Abse2001/g350-linux-handheld/docs/AM3352_DDR38_CHECKPOINT.md

# DDR38 routing checkpoint — 2026-10-04

Installed versions: tscircuit **0.0.2744**, core **0.0.2080**, capacity-autorouter **0.0.958**, CLI **0.1.2237**. The earlier immutable upgrade binder still verifies these packages and the unchanged default DDR30 copper.

The editable [DDR38 candidate](../experiments/am3352-command-clock-seeded-775-replay.circuit.tsx) preserves all 23 checked data/reset guides, the previously checked clock pair and all fixed host copper. Trials 766–776 replan uncommitted fanout reservations and negotiate manual command carriers on Top/Bottom. The complete replay restores every differential-pair declaration. Independent KiCad numeric-pad connectivity confirms **38 of 49 DDR signals connected** in one coherent placement, with 140 trace pieces, 175 full-depth through-vias, 212 logical components and 912 physical pads on four copper layers. All 125 original trace pieces and 141 original vias are retained. Both bytes and all three pairs pass planar relative skew.

The actual local tsci phase **DDR_COMMAND_CLOCK_BUS_LANES**, using **bus_lanes**, ran on the remaining 11 commands with all 140 fixed traces and 912 pads. Its input is independently verified against the complete replay. Only already guided pair declarations are omitted in the diagnostic continuation; the complete source retains them. [Trial 776](../dist/am3352-command-clock-seeded-775-native-phase-attempt-776/result.json) timed out at its configured 60-second routing limit (77.624 seconds total build wall time), producing no complete new output. Partial solver paths are not counted as successful routing.

All-layer Gerber shorts: **zero**. Independent physical clearance/drill violations: **zero**. KiCad still reports 418 presentation warnings, 499 reported/capped host opens and the same five explicitly ignored checks. Exact local library generation preserves all 15,379 physical records. RAM supply/ground/bypass plane connectivity remains 18/21/28; USB retains 38 numeric-pad assignments and 40 copper continuity checks. Top and Bottom snapshots were inspected. TypeScript and helper syntax checks pass.

DDR is unqualified: 11 command/control signals are missing; 14 routed command/clock signals fail the **41.75–44.29 mm** nominal range; **A2/A9/A13/A14/A8** exceed TI's **31.75 mm** reduced-class-spacing allowance. Complete command-group matching, coupling, impedance, return transitions, package/via delays and termination/ODT remain open. The separate DDR34 branch passes physical/connectivity checks but its A9 has a same-net length ambiguity: route sum 41.775130 mm versus graph path 40.536307 mm. That electrical branch is not promoted.

The fixture remains **100 × 124 × 1.6 mm** and does **not** have verified original G350 shell fit. Host power/storage/display/controls/audio/Linux work remains incomplete. Fabrication remains blocked before modification of any of the 205 historical fabrication files. No commit, GitHub push or tscircuit publication was made. The default stays DDR30; the older DDR33 spacing-repaired checkpoint remains immutable.

Evidence: [checked summary](../checks/integrated/am3352-command-clock-seeded-775-replay-check-summary.json), [nominal and spacing review](../checks/integrated/am3352-command-clock-seeded-775-replay-spacing-and-nominal-review.json), [native input preservation](../checks/integrated/am3352-command-clock-seeded-775-replay-native-phase-input-validation.json). Guidance: [tscircuit DDR routing](https://docs.tscircuit.com/guides/routing-ddr) and [TI AM335x datasheet SPRS717L, Tables 7-61/62/68/69](https://www.ti.com/lit/ds/sprs717l/sprs717l.pdf).

Next work: coordinate the remaining 11 command escapes and native phases, repair nominal lengths and spacing, then run fresh complete-interface checks. Measured original-shell geometry and the powered handheld/Linux implementation remain required before release.
