Abse2001/g350-linux-handheld/docs/AM3352_DDR_ROUTING.md

# AM3352 DDR routing record — 2026-10-04

## Compatible command package exits — trials 794–808

The first five-path opening leaves BA0/A3 competing for one RAM exit. Exact owner diagnostics identify additional reservations, and opening nine unqualified command routes provides individually legal candidates for all 32 remaining endpoints. The initial joint search reaches 400,000 choices. Factoring independent candidate regions and propagating pairwise support identifies an incompatible CPU candidate set in 0.829 seconds; this is a result for the generated candidate domains, not a proof that the PCB cannot be routed.

The next source opens all 17 staged command/control routes for a complete 24-signal replan, preserving both checked data bytes, reset, the clock pair and all reference/USB copper. It retains 25 complete DDR channels, 127 trace pieces, 145 vias, 212 logical components and 912 SMT pads. Actual local tsci `DDR_COMMAND_CLOCK_BUS_LANES` trials 796/801 use core 0.0.2080 on 16/24 open commands; both time out with no complete output. Source/input audits verify the actual numeric pad endpoints, all fixed copper and the four-layer Top/Bottom signal restriction. All three pair declarations remain present in the complete editable sources.

The factored manual search assigns **all 48 package exits in 48 choices**, including exact mutual foreign-land and drill separation. It adds 48 through-vias and 48 Top prefix pieces. The source refills its original continuous GND/DDR1V5 boundaries around those signal holes with the existing 0.12 mm pour margin. Independent KiCad verifies all **24 CPU and 24 RAM numeric pads to their intended full-depth vias**, all 25 retained complete CPU/RAM DDR channels, RAM supply/ground/bypass connectivity at **18/21/28**, and USB numeric assignments/continuity at **38/40**. Both byte groups and all three pairs retain relative planar skew. All-layer shorts and physical clearance/drill violations are zero. The partial board explicitly retains **48 dangling-via warnings**, **418 presentation warnings**, **499 reported/capped host opens** and the same five ignored checks. Exact local library generation preserves 13,725 physical records; both surface snapshots were inspected. [Independent checked package-exit summary](../checks/integrated/am3352-command-compatible-fanouts-802-check-summary.json).

Direct combined native trial 803 fails negotiated lane search. Phased native trial 804 obtains six via-free carriers: A11, RASn, A2, A7, A14 and A6. A guarded manual repair pass retains those exact six and plans five additional carriers, leaving 13 commands unresolved. These interconnect plans remain nonexportable until combined with their local prefixes in an editable source and independently checked. The true through-via terminal permits either outer face; the wrapper records the face actually chosen by the unchanged guarded bridge. Earlier off-grid and wrapper-assertion retries are retained as rejected logs; one retry loaded its old assertion before the edit finished and its runtime helper snapshot is explicitly marked unreproducible. No PCB copper from those retries was accepted.

The package pad and via shape audit confirms circular geometry is already represented correctly. Next work should coordinate the unresolved carriers with exit choices and examine whether the conservative raster guard excludes physically legal thin corridors. Every accepted repair must preserve the actual 0.1016 mm copper clearance, 0.20 mm drill-to-pad clearance and 0.254 mm drill-edge spacing, then pass independent combined checks. The full target remains all 49 DDR signals, complete timing/spacing/impedance/returns/termination, the powered handheld and Linux, and measured original G350 shell integration. The checked fallback remains DDR42; the default remains DDR30. Registry rechecks still match tscircuit 0.0.2744, core 0.0.2080, capacity-autorouter 0.0.958 and CLI 0.1.2237. Typechecking passes. Fabrication stays blocked and all 205 historical fabrication files are unchanged. No GitHub or tscircuit push was made.

## Latest checked partial routing: DDR42

The editable [DDR42 replay](../experiments/am3352-command-fine-782-replay.circuit.tsx) connects **42 of 49 actual CPU/RAM pad pairs** on four layers. It preserves the original 23 data/reset guides, the previously checked clock pair, all 125 original trace pieces, all 141 original vias, and every component, physical pad and fixed reference/USB piece. The new replay contains **144 trace pieces and 187 full-depth through-vias**. Independent KiCad connectivity, all-layer shorts, physical clearance/drill checks and filled RAM reference-plane connectivity pass. Both bytes and all three pairs pass relative planar skew. [Bound checks](../checks/integrated/am3352-command-fine-782-replay-check-summary.json).

Installed and registry-verified versions remain **tscircuit 0.0.2744, core 0.0.2080, capacity-autorouter 0.0.958 and CLI 0.1.2237**. The [native continuation](../experiments/am3352-command-fine-782-replay-native-phase.circuit.tsx) runs the Host's `DDR_COMMAND_CLOCK_BUS_LANES` phase through local tsci with `autorouter="bus_lanes"`. Trial 783 preserves all 144 fixed pieces and 912 SMT pads, then fails with **No collision-free local dogbone assignment**. Only already guided pair declarations are omitted in this diagnostic; the complete editable replay retains all three declarations.

Seven signals are missing: **A3, RASn, WEn, A2, A12, A11 and CKE**. Seventeen routed command/clock signals fail the placement-derived **41.75–44.29 mm** nominal range. **A9, A13, D12, A10, A14, A4 and A8** exceed the **31.75 mm** reduced-class-spacing allowance. Preserving D12 geometry does not preserve its spacing exposure when new neighboring command routes are added. The full command group, coupling, impedance, return transitions, package/via delays and termination/ODT remain unqualified. There are still 418 presentation warnings, 499 reported/capped host opens and five explicitly recorded ignored checks.

Exact local diagnostics identify five unqualified command carriers blocking the remaining package exits: **A7, BA0, CASn, A4 and ODT**. Opening these produces a temporary 37-signal planning stage while preserving data/reset/clock/reference/USB copper. Actual native trial 791 runs on its 12 open commands, 139 fixed traces and 912 pads, then times out without complete output. Simultaneous manual-fanout trials 792 and 793 find individually legal candidates for all 24 endpoints but fail the joint assignment: BA0's remaining RAM exit conflicts with every A3 RAM candidate. Expanded guarded surface searches do not resolve that conflict. These stages add no checked complete signals and do not replace DDR42. Trial 790's partial carrier plan also does not exceed the checked DDR42 result.

The default remains DDR30. Fabrication is blocked: complete DDR timing/spacing and host routing, the powered peripherals and Linux, and measured original G350 shell geometry remain required. The 100 × 124 mm routing fixture does not fit the original shell. No GitHub or tscircuit publication was made for this partial checkpoint.

The requested bootstrap uses tscircuit's **native `bus_lanes` preset**, implemented by `BusLanesPipelineSolver`. The installed core is now 0.0.2080 and capacity-autorouter is 0.0.958; historical trials retain their original version records; attempts 1–16 below used 0.0.2048, and attempts 17–207 used 0.0.2050. The current [DDR guide](https://docs.tscircuit.com/guides/routing-ddr), [autorouting phase API](https://docs.tscircuit.com/elements/autoroutingphase) and [breakout API](https://docs.tscircuit.com/elements/breakout) were read and applied. The user's `lane_bus` refers to the documented `bus_lanes` name.

## Implementation

The two packages are individual JLCPCB imports, corrected against primary ball maps. Every one of the420 physical balls remains present. There are49 numeric-pin trace connections:22 byte signals,26 synchronous address/command/clock signals and asynchronous reset. DQS0, DQS1 and CK have explicit differential-pair constraints. The old8-layer trials used independent L3/L7/L5 buses. The current4-layer candidate permits DDR wires only on top/bottom, reserving both inner reference layers.

The active `am3352-powered-host.circuit.tsx` uses four native DDR routing phases followed by a power/control phase. The isolated `am3352-ddr-clearance-bootstrap.circuit.tsx` retains the same DDR routing approach. Local pad-to-layer dogbones are generated by the DDR preset; the interconnect then stays on its assigned signal layer. Separate manual-fanout experiments preserve the autorouter for the channel. An opposing-boundary experiment reserves distinct bottom/top exit regions for the two bytes and command bus, with larger fanout areas.

The documented phase configuration is `autorouter="bus_lanes"`; `routingPhaseIndex` on each named electrical trace assigns it to that pass. Buses group those traces but do not create their electrical connections. The preset preserves prior fanout copper, includes its planar lengths in matching, and adds no intermediate channel vias. `pcbAllowedLayers` and `preferredLayers` restrict allowed layers. Supplied fanouts therefore need compatible layer exits and a winding order that permits a planar connection.

For manual local changes, the supported interface is `<breakout pcbTracePaths={paths}>` (also available on its `<fanout>` alias). Saved paths are keyed by port selector and must cover every routing connection owned by that breakout. The global channel still runs `bus_lanes`. A later `reroute` phase can target earlier routed connections or a rectangular region; this does not waive connectivity, clearance, or timing checks. Supply escapes need explicit connections and plane mapping through `fanoutPourNetMap`, rather than overlaying the guide's separate power-dogbone example.

The guide's Winbond example has 47 signals. Our selected Micron 4 Gb x16 part has 49, including A13 and A14; its map must not be replaced by the example's map. Its M7 is NC. All CPU/RAM terminals are independently checked against the selected primary ball maps.

## Checked partial result

Attempt 10 routed byte0 in 7.5 seconds, then byte1 timed out at 90 seconds. The aborted render discarded all copper. `export-am3352-diagnostic.mjs` recovers the **unchanged** completed first-phase traces from the exact second-phase input, verifies the original two pad endpoints and physical via dimensions, and retains the native timeout record. It makes a partial diagnostic with source/checkpoint/result hashes, never a release bundle.

| Check on this diagnostic | Result |
|---|---|
| Continuous processor-to-RAM signals | 11/49; 38 open |
| Full-depth through-vias | 22, 0.35 mm lands / 0.15 mm drills |
| Byte0 end-to-end planar skew | 0.635 mm, passes 0.635 mm limit |
| DQS0 end-to-end planar skew | 0.127 mm, passes 0.127 mm limit |
| Gerber shorts, all eight layers | 0 |
| KiCad copper/drill violations | 0 |
| Complete DDR continuity/timing | Fails: remaining buses incomplete |
| Powered host / fabrication readiness | False |

Evidence is in `checks/integrated/am3352-clearance-11-*`, with the actual checked circuit retained in `routing/am3352-byte0-native-diagnostic.circuit.json`. The inspected snapshot is `images/am3352-memory-clearance-11.png`. The original 0.30 mm lands had 31 copper-to-drill violations under the same 0.20 mm hole-clearance rule. Larger lands reserve the missing clearance without reducing that rule. KiCad exports are verified against the actual Circuit JSON before logical via-layer pairs are normalized to physical F.Cu–B.Cu spans; exact duplicates are removed and geometry is preserved during library preparation.

Timeout reports omit only `lastProgress.debugGraphics`, a large presentation overlay; the full original failure-file hash and all timeout metadata remain. A before/after hash comparison confirms that compacting the error message changed no physical or source records. The default continuity check still rejects the retained native error and all 38 open signals.

## Attempts and current failure

| Attempt | Geometry/strategy | Outcome |
|---|---|---|
| 1–2 | 0.4572/0.254 mm vias; numeric-terminal correction | Local dogbones, then negotiated search failed |
| 3 | Separate bus phases, larger vias | Byte0 timeout |
| 4 | Direct native dogbones, 0.30/0.15 mm | Byte0 routed; byte1 timeout; 31 drill-clearance errors |
| 5 | RAM shifted to (+3, −23) mm | Byte0 timeout |
| 6 | Manual opposing dogbone quadrants | Byte0 routed; byte1 timeout; incomplete export |
| 7 | Manual fanouts, 0.127 mm clearance | Byte0 timeout |
| 8 | Whole-byte swap, manual fanouts | Byte0 timeout |
| 9 | Within-byte DQ permutation | No shared DQS0 tuning corridor |
| 10 | Direct native dogbones, 0.35/0.15 mm | Byte0 routed and physical checks passed; byte1 timeout |
| 11 | All 49 dogbones coordinated in one phase, separate buses | Negotiated lane search exhausted |
| 12 | Byte1-first phase order | Byte1 timeout at 90.1 s |
| 13 | Larger, opposing ordered fanouts | First fanout stopped responding; externally terminated after exceeding 3 min |
| 14 | Permute byte1 DQ only; byte1 first | Native byte1 routed in 8.6 s; subsequent byte0 had no collision-free dogbone assignment |
| 15 | Both byte lanes together, separate timing buses | Negotiated search timed out at 90.0 s |
| 16 | Prepare all 98 native dogbones together; replay through `pcbTracePaths` | Both package escapes accepted; byte0 channel timed out at 90.2 s |
| 17 | Full 142-component power/DDR draft; latest core 0.0.2050 | Byte0 failed during local dogbone assignment after 30.7 s; no channel copper retained |
| 18 | Move bypass parts out of signal escape corridors, preserving TI limits | Local escape preparation advanced; native solver rejected the rounded board outline after 21.9 s |
| 19 | Same 142-component placement, rectangular outline | Byte0 routed in 51.4 s; byte1 dogbone assignment failed in 0.8 s |

Changing phase order tests whether prior through-vias consume later escapes. Coordinated dogbones test simultaneous site assignment. Ordered fanouts address winding and local congestion directly. Failed phases are not counted as completed connections. An empty-copper render is rejected by the independent connectivity check before the default shorts command.

TI allows [within-byte DQ swapping and complete byte-lane swapping](https://e2e.ti.com/support/processors-group/processors/f/processors-forum/1205797/am4376-about-ddr3-data-line-swapping), including the matching DQS and DM signals when swapping whole bytes. These trial maps have independent bijection/function/group checks. Address and command maps remain fixed. They are experiments, not a claim of successful routing.

The byte1-only map has a separately recovered, unchanged native 11-signal diagnostic. Its end-to-end byte skew is 0.635 mm, DQS1 skew is 0.011685 mm, and it has zero all-layer Gerber shorts and zero KiCad physical violations. The other 38 signals remain open. Its native failure and downstream missing-copper records are retained. Evidence: `checks/integrated/am3352-byte1-11-*`. The two independently checked byte diagnostics cannot be combined into a 22-signal result: their escape sites have not been routed and checked together.

The guide's saved-fanout interface was applied in attempt 16. `bootstrap-am3352-native-dogbones.mjs` verifies the actual source terminals, prepares the 98 escapes using the installed native DDR solver, and records hashes before translating only local coordinates into component-relative `pcbTracePaths`. The four global phases still run `bus_lanes`. Preparation is an escape result, not channel connectivity or DRC approval.

The default entry now advances the actual host source, including PMIC and decoupling. The two-package routing fixtures remain isolated experiments; their physical checks do not cover that larger board.

The power draft keeps three of its twenty CPU DDR high-speed capacitors beneath the CPU. The other CPU parts and all twelve RAM parts move beside the packages to leave signal-via corridors open. The generated-layout audit retains TI's maximum nearest power/ground distance of 10.16 mm for CPU capacitors and 3.81 mm for RAM capacitors, with zero native placement errors. These nominal placement checks do not establish the eventual capacitor-via topology or effective capacitance. Attempt 18 also exposed an additional native solver restriction: its lane stage rejects custom board outlines. The active routing draft therefore uses a rectangular 100 by 124 mm outline.

Attempt 19 supplies a new checked result on that actual larger placement: eleven continuous byte0 signals, twenty-two physical through-vias, 0.635 mm byte skew, 0.127 mm DQS0 skew, zero all-layer Gerber shorts and zero independent copper/drill errors. KiCad retains **402 silkscreen warnings and 499 unconnected host items**. The native byte1 failure and downstream missing-copper records remain intact. This is incomplete host copper, not an overall DRC pass. Evidence: `checks/integrated/am3352-host-byte0-19-*`; exact circuit: `routing/am3352-host-byte0-native-diagnostic.circuit.json`.

## Remaining qualification

The active board now uses **four layers maximum**. The preceding eight-layer attempts remain historical. Attempt 21 uses the actual 185-component clock/boot/power placement and completes byte0: 11/49 signals, 22 through-vias spanning exactly four layers, zero Gerber shorts, zero KiCad copper/drill errors, passing byte0/DQS0 planar skew, 416 silkscreen warnings and 499 unconnected host items. Attempt 22 reserves all 98 DDR escapes against all 821 actual SMT-pad obstacles but fails its complete planar channel search after 7.81 seconds. Attempt 23 rotates RAM by 180 degrees and times out in byte0. Attempt 24 explicitly guides native fanout exits into facing corridors and times out during CPU fanout. A general-router repair trial retains the native byte0 bootstrap; any resulting channels still require full continuity, end-to-end skew, shorts and independent physical checks. None of these trials qualifies the stackup or reference planes.

The standalone fixtures have no power nets, planes or decoupling. Through attempt25, the host source had logical power nets/decoupling but no completed power copper or planes. Repair attempt25 preserves native byte0 and times out after90 seconds. The0.635/0.127mm checks measure planar copper only; they exclude package delays and via depth. Pair spacing and impedance need the fabricator stackup. TI's reference via guidelines differ from the fine-drill trial. Complete all49 signals and the powered board, then rerun continuity, skew, shorts, physical DRC and stackup-aware review before producing fabrication files.

## Current four-layer candidate with reference regions

TI SPRS717L Tables7-61/62 require two signal layers, a full ground reference and a full DDR power reference. The current source therefore reserves **inner1 GND / inner2 DDR_1V5**, with signals on **top/bottom** and18mil lands/10mil drills. Attempt21's inner1 signal route is historical and cannot qualify this allocation. The independent routing check now rejects inner signal copper, undersized trial vias, missing reference regions and DDR wires outside the reserved region.

At attempt 27, the 204-component source integrated the DM3D-SF microSD holder, its separate regulator and reset supervisor. Both inner reference regions rendered, with one CPU DDR bypass loop: two bottom traces and two through-vias outside all solder pads. Further RAM power progress is recorded below. All 49 end-to-end DDR channels remain unfinished.

| Attempt | Current outer-layer strategy | Result |
|---|---|---|
|26|Fresh204-component tsci source, bytes bottom / command top,18mil vias|44 local escapes prepared; native planar channel search fails in9.43s|
|27|Retain authored bypass copper and its vias; keep all882 SMT-pad obstacles; confine routing to the reference region|44 local escapes; native channel search fails in9.82s|
|28|Ordered outer-layer fanouts|Constructor rejects the undersized27-exit corner band; no copper generated|
|29|Wider facing fanouts, separate0.6mm exit corridors, both outer layers available for local crossings|CPU fanout reaches its61s deadline without completing; no completed DDR copper|

That earlier source/partial-bypass diagnostic passes all-layer Gerber shorts and has zero KiCad error-severity violations after library preparation. It retains **418 warnings and 499 unconnected host items**. Independent DDR continuity fails 0/49. Those checks cover that partial source only. Evidence is `checks/integrated/am3352-four-layer-reference-*`; its snapshot is `images/am3352-four-layer-reference-source.png`.

The KiCad converter initially discarded `excludeRefs` and prohibited the socket housing over its own no-copper areas. Export preparation verifies both polygons against the source, retains all track/via/pad/pour prohibitions, and gives only the J_SD housing an explicit footprint exception. No copper item is exempted and no DRC error is hidden. At that stage, library preparation preserved 227 physical records while assigning 206 local footprint identities (204 parts plus two via primitives).

## RAM reference and bypass copper — 2026-10-03

The native DDR bootstrap now reserves 44 actual byte signal escapes while assigning all 18 RAM supply and 21 RAM ground escapes. The 39 reference escapes are represented in `RamReferenceEscapes.tsx` as individual tscircuit vias and direct traces from the exact package pins. Solver-only plane targets are not exported as artificial electrical terminals or manufactured copper. All 882 component pad obstacles and the original bypass copper remain in the input.

`RamBypassLoops.tsx` adds short manual traces and separate plane vias for both terminals of all 12 RAM 100 nF capacitors and both RAM 22 uF bulk capacitors. The source now contains 69 traces and 69 full-depth 18/10 mil vias, including the original CPU capacitor loop. CPU/PMIC power routing, VREF copper, effective capacitance and all DDR signal channels are still incomplete.

| Attempt | Strategy | Result |
|---|---|---|
|30|Run each source bus_lanes phase separately, preserving previous copper|Byte0 times out at 60 s; no completed channel|
|31|Joint supply/ground preparation with coincident virtual plane targets|Input direction cannot be inferred; corrected for the next trial|
|32–33|Joint CPU/RAM reference escapes, retaining 44 signal dogbones; narrower local stubs in 33|No complete collision-free assignment|
|34|RAM reference escapes, with all signal dogbones reserved|All 39 RAM supply/ground escapes assigned and then implemented as explicit source copper|
|35|Reprepare signals against the generated 39 RAM escapes|All 44 local byte escapes still available; no channel solve claimed|
|36|Byte0-only ordered CPU/RAM boundary fanouts on the actual source|CPU fanout times out after 92.69 s; one solver step overran the 60 s limit|
|37|Reprepare signals with 14 new manual capacitor loops|44 escapes prepared; physical checks then find two same-net overlapping drill pairs|
|38|Correct the affected capacitor row, retain the new package/bypass copper|44 signal escapes remain available; physical and RAM plane connectivity checks pass|

The right-side capacitor row at y=-28 mm now places its vias 0.4 mm above that row. This clears the top ZQ resistor while retaining legal spacing to the preceding row's holes. The minimum hole-edge separation across all 69 vias is 0.446 mm, exceeding the 0.254 mm rule. The failed pre-fix DRC is retained in `am3352-ram-bypass-before-hole-fix-drc.json`. Same-net holes are checked explicitly in source audits; the partial physical summary rejects all non-presentation violations regardless of severity.

KiCad's native connectivity engine verifies all 39 RAM supply/ground pads and all 28 bypass terminals reach the corresponding actual filled reference plane through the expected vias. Final independent DRC has **zero physical violations at any severity**, with **418 presentation warnings and 499 unconnected host items**. All-four-layer Gerber shorts pass. Source power, boot and storage audits pass on the same source hash. DDR continuity remains **0/49**, so this is not an overall DRC or fabrication pass.

Evidence: `checks/integrated/am3352-ram-bypass-check-summary.json` and `am3352-ram-bypass-copper-connectivity.json`; actual circuit and KiCad board are in `dist/diagnostics/am3352-ram-bypass`. Library preparation retains all 428 physical records with 273 matching local footprints. Snapshot: `images/am3352-ram-bypass-source.png`. No GitHub or tscircuit publication was made.

## Guided native channel and manual DQS tuning — 2026-10-03

Attempts39–46 edit local fanouts on a conservative 0.02 mm grid while retaining all actual pads, source copper, 18/10 mil full-depth vias and both inner reference planes. Attempt46 completes all22 byte0 package fanouts. Attempt48 uses the native channel as an explicitly untuned connectivity bootstrap, and attempt49 removes seven unused native via branches. The complete pad-to-pad paths are saved as editable `pcbPath` source in `am3352-guided-byte0-replay.circuit.tsx`; no completed board is imported. This first replay has eleven continuous DDR signals and30 DDR vias, but fails byte0 and DQS0 planar matching.

The matched channel initially stalled because the coupled-pair solver treated original package pads as channel terminals after their fanouts were complete. Attempt52 removes only those completed-package `componentId` associations from the global-channel obstacle descriptors. Every physical pad, position, layer, net owner and source metadata record remains unchanged and is asserted. The native solver immediately finds all eleven channel candidates, then rejects them for insufficient tuning room. Failed child candidates are not exported or counted as completed signals.

Attempt53 adds two chamfered 45-degree trombones to the shorter DQS0 CPU top fanout, adding2.073970 mm without new vias. Full-byte attempt54 still fails its common DQS tuning corridor. Attempt58 therefore checks a pair-matched intermediate channel with the original DQS constraint retained and the whole-byte limit deferred only for that intermediate solve. The saved tscircuit source and independent timing check retain the full0.635 mm byte requirement and correctly reject it.

| Check on the actual attempt58 source replay | Result |
|---|---|
| Actual CPU-to-RAM continuous signals |11/49; native KiCad and independent Circuit JSON agree|
| Physical layers / signal layers |4 / top and bottom only|
| DDR vias / all through-vias |26 /95;0.4572 mm lands,0.254 mm drills|
| Existing power/reference copper |All69 traces/vias retained|
| RAM reference / bypass connections |39 balls and28 capacitor terminals reach actual filled planes|
| DQS0 planar skew |1.42e-14 mm; passes0.127 mm limit|
| Byte0 planar skew |16.272935 mm; fails0.635 mm limit|
| Gerber shorts |0 across all four layers|
| Independent physical violations |0 at every severity|
| Presentation warnings / unconnected host items |418 /499|
| Fabrication readiness |False|

Exact editable source: `experiments/am3352-guided-byte0-pair-matched-replay.circuit.tsx`, with paths in `routing/am3352-guided-byte0-pair-matched-paths.json`. Generated circuit SHA256: `e13b018aac80c7a465efcc81e6e2b05556ffa2127124b5b3954e397dd82934cd`. Evidence: `checks/integrated/am3352-guided-byte0-pair-matched-check-summary.json`. The bottom snapshot was visually inspected. Package/via delay, differential coupling in the fanouts, stackup impedance and complete electrical timing remain unqualified.

Attempts55–57 test a TI-permitted complete byte swap on the same physical host; all22 local fanouts complete but the native full-byte matcher rejects23.175 mm skew. Attempts59–60 widen ordinary exit pitch to0.8 mm, retaining adjacent DQS exits; local fanouts complete but pair matching still fails. Attempt61 moves the DQS exits to the edge of the bundle; its fanouts complete and its channel remains unqualified. Attempt62 independently assigns both packages' DQ exits before deriving a permitted within-byte DQ permutation. That preparation is not completed channel copper; the actual numeric-pin tscircuit source must be rebuilt and checked before routing it.

The default entry still has0/49 complete DDR channels. These separate replay experiments do not relax its release guard. All work remains local; no GitHub or tscircuit push was made.

## Byte0 matched with the native router — attempt74

Attempts62/65–69 derive and rebuild an actual DQ-only permutation from both packages' independently assigned exits. The source, numeric pin ownership and all local copper identities are rebound together; DQS/DM, byte1 and command/clock remain unchanged. Conservative manual tuning balances DQS0, but the native global matcher still rejects the shared tuning corridor. Attempt63's edge-pair exits and attempt64's native octilinear tuning option also fail and contribute no completed channel copper.

Attempt70 shifts the candidate exit strip to start at x=-3.6 mm, with0.8 mm ordinary pitch and adjacent DQS exits at2.4/2.72 mm. Both package fanouts complete. The actual source is rebuilt with `memory-byte0-centered-swizzled-connections.json`; attempt71 prepares its native escapes and attempt72 verifies/rebinds every exact pad endpoint and copper owner. Attempt73 adds a2-tooth chamfered trombone to the CPU bottom DQS0 escape, adding1.931371 mm without new vias. A guarded geometric search rejects collisions and unintended return-leg shortcuts before any independent PCB approval.

**Attempt74 uses the unmodified native `BusLanesPipelineSolver`, with `fanout:'none'` and all original0.635/0.127 mm bus/pair limits retained. It solves the complete eleven-signal byte channel and performs the global length tuning.** No failed solver candidate is used. Saved full pad-to-pad paths are replayed through tscircuit `pcbPath`, with both packages still individual JLCPCB imports and all four native DDR phases present.

| Independent check on the actual attempt74 replay | Result |
|---|---|
| Actual continuous CPU-to-RAM signals |11/49; Circuit JSON and native KiCad agree|
| Byte0 planar skew |0.635000000393 mm; passes0.635 mm with floating-point tolerance|
| DQS0 planar skew |1.07e-14 mm; passes0.127 mm|
| Four-layer Gerber shorts |0|
| Physical DRC at every severity |0|
| DDR vias / total through-vias |22 /91;18/10 mil full-depth geometry|
| Existing power/reference copper |All69 traces/vias retained|
| RAM reference and bypass connectivity |All39 balls and28 capacitor terminals connected to actual filled planes|
| Presentation warnings / unconnected host items |418 /499|
| Complete DDR / fabrication readiness |False;38 DDR signals remain open|

Exact editable replay: `experiments/am3352-guided-byte0-matched-replay.circuit.tsx`. Paths: `routing/am3352-guided-byte0-matched-paths.json`. Actual circuit SHA256: `49e01f91deea61b258f6f12ec62dc0ed42582a47027c88eb4c14655a393a05f0`. Checked KiCad board SHA256: `bb7f0affe829d7f08f2c9478b18bdacae5465f8562be09f19c4dd89dec15b8db`. Evidence: `checks/integrated/am3352-guided-byte0-matched-check-summary.json`. The inspected snapshot is `images/am3352-guided-byte0-matched-bottom.png`. Library preparation preserves all6584 physical records and273 exact footprints.

Next routing work is byte1 on this same geometry and copper, followed by command/clock and reset. The separate earlier byte1 diagnostics cannot be combined with this result. Package/via delays, impedance and differential fanout coupling remain unqualified. The default source still has0/49 channel routes; the checked replay is explicit and separate. No files have been pushed to GitHub or tscircuit during this milestone.

## Both bytes in one checked four-layer source — 2026-10-03

Attempt 75 starts from the actual checked byte0 source and prepares only the 22 remaining byte1 pad dogbones. All 80 existing trace pieces, 91 existing holes and 882 SMT pads are retained. The first local trials identify a trapped RAM C2/D9 escape. The isolated source moves only C1's reference via from (-2.8,-23) to (-3.8,-22.2); its direct power connection is 0.7211 mm. The revised source independently retains all 39 RAM plane connections, all 28 bypass-terminal connections and the first byte's exact geometry, planar matching and physical checks.

Attempts 79–84 edit the native C2 dogbone and four inward-facing RAM dogbones, then test bottom channels on the left and right. Local package congestion prevents a completed channel. Attempts 85–94 assign byte1's channel to top while retaining byte0 on bottom. Unused bootstrap via branches are pruned before local search; all 22 native top pad wires remain. No actual power or byte0 hole is removed. The local search distinguishes the actual start layer from an existing via, enforces at most two new full-depth vias per local fanout, keeps guarded wire checks and checks via geometry at its exact point. Via-point grid padding had unnecessarily rejected legal interstices; fabrication clearances and drill limits are unchanged.

The top candidate places negative DQS1 at x=3.6 mm and positive DQS1 at x=3.92 mm, with a fixed DM1 handoff at x=-0.4 mm. Two CPU data dogbones turn north into different interstices. Attempt 96 completes all 22 package fanouts. The generated tscircuit source is rebuilt with `memory-byte1-top-centered-swizzled-connections.json`; attempt 98 verifies the actual pad endpoints and every rebound copper owner. Only DQ bits within byte1 are permuted. Byte0, DQS, DM, command, clock and reset retain their intended associations.

Attempt 99 finds all 11 native channel paths but rejects DQS length matching. Attempt 100 adds 2.682843 mm to the shorter CPU top DQS1 fanout. The full-byte trial then identifies insufficient tuning clearance on D8/D9. A pair-only intermediate remains explicitly unqualified. Subsequent manual edits add 11 mm to D8 across RAM bottom/top fanouts and 7 mm to D9 across RAM top and CPU top fanouts. Failed local candidates produce no accepted paths. These local edits add no holes. The native channel is still responsible for final routing and matching.

**Attempt 110 completes byte1 with both original limits enabled: 0.635 mm byte skew and 0.127 mm DQS skew.** It retains all actual copper and pad geometry. Only the already-completed package association is removed from global-channel pad descriptors, as in byte0; no physical obstacle or owner is removed. Both complete byte paths are then replayed as editable tscircuit `pcbPath` source using individual component imports.

| Check on the actual two-byte replay | Result |
|---|---|
| Exact continuous CPU/RAM pad pairs | 22/49; Circuit JSON and native KiCad agree |
| Copper allocation | Four layers; byte0 bottom, byte1 top, inner1 GND, inner2 DDR_1V5 |
| Byte0 / byte1 planar skew | 0.635 mm / 0.635 mm; both pass |
| DQS0 / DQS1 planar skew | Approximately zero / zero; both pass |
| DDR / all through-vias | 40 / 109; 0.4572 mm lands and 0.254 mm drills |
| Existing power/reference copper | 69 trace pieces and 69 vias retained |
| RAM reference / bypass connections | All 39 balls and 28 terminals reach the actual filled planes |
| All-four-layer Gerber shorts | Zero |
| Independent physical violations | Zero at every severity |
| Presentation warnings / unconnected host items | 418 / 499; host count does not measure DDR continuity |
| Complete DDR / fabrication readiness | False; 27 command/clock/reset signals remain open |

The active entry is now `experiments/am3352-guided-both-bytes-matched-replay.circuit.tsx`, selected by `index.circuit.tsx`. Its actual circuit SHA256 is `ed9d355f38dd8ef13c8c6104b7feae9632a7beb926dbcdce04dbdac01d6d978c`; its checked KiCad board SHA256 is `32b215d263182e077278e9e9be5e3bec9e8f4d4ae68e6ba23f39535207117feb`. Evidence: `checks/integrated/am3352-guided-both-bytes-matched-check-summary.json`. Library preparation preserves all 13286 physical records and 273 exact footprints. The top snapshot was visually inspected.

The complete 49-signal check correctly remains failed. This milestone qualifies planar matching and physical copper checks only. Package/via delays, differential coupling, stackup impedance, return paths, full CPU/PMIC power and the handheld peripherals/software remain unfinished. TI's [Table 7-69 and accompanying DDR3 guidance](https://www.ti.com/lit/ds/symlink/am3352.pdf) were rechecked for within-byte matching; separate byte lengths do not need to match each other. No fabrication bundle or remote publication was produced.

Attempt 111 prepares the next native input with all 22 checked byte signals, all 91 source trace pieces and 109 actual vias retained. The remaining 27 connections are command/clock/reset. Attempt 112 reaches its 30-second native lane-routing deadline without an accepted completed output; the checked two-byte source remains unchanged. The active index rebuild is electrically and physically identical to that source; only its filesystem metadata hash differs, recorded in `am3352-guided-both-bytes-active-index-equivalence.json`.

## Current active bytes and reset — attempt131

The active entry now selects `am3352-guided-both-bytes-and-reset-replay.circuit.tsx`: **23/49 exact CPU/RAM pad pairs are connected**, with all 22 previously checked byte paths preserved verbatim. All 26 command/clock signals remain open. The source has 92 trace pieces and the same 109 through-vias; reset adds no holes.

The direct reset trial129 reaches its45-second native routing deadline without accepted copper. Attempt130 manually escapes the actual G2/T2 pads to top-layer handoffs at CPU(-16,-7.96) and RAM(-9,-33.96). Attempt131 routes those handoffs with the native `BusLanesPipelineSolver` in four iterations. Its51.037mm complete planar reset path has no synchronous length-match requirement. No completed board is imported; the full path is editable `pcbPath` source.

Independent Circuit JSON and KiCad checks agree on23 connected signals. Both original byte limits remain passed:0.635mm byte skew and0.127mm DQS skew. All-four-layer Gerber shorts are zero, physical DRC has zero violations at any severity, and all39 RAM reference balls plus28 bypass terminals still reach their actual filled planes. The418 presentation warnings and499 unconnected host items remain. Library preparation preserves all13419 physical records and273 exact footprints.

Checked source SHA256:`2c72f2f082db98ec4b816ac334bd0502b2f1f926abdedd5a995b0ed6bafcab04`; checked board SHA256:`242068fb4237b632a9a545cc65f1aa451c029de279e4ffae07ee778152ab37a1`. Evidence: `checks/integrated/am3352-guided-both-bytes-and-reset-check-summary.json`. The top snapshot was inspected. Complete DDR, electrical timing/impedance, powered host, peripherals and Linux bring-up remain unfinished; fabrication is blocked. No remote publication was made.

### Command/clock experiments113–128

These experiments precede the checked reset route and are isolated from the active board. Full native bottom dogbone assignment fails; individual diagnostics find no CPU bottom dogbone for ODT, CSn0 and A1. Same-layer top preparation needs no dogbones. Local top search identifies the existing byte1 DQS1 fanout at(2,-27.8) and its adjacent wire as a barrier to the RAM clock breakout.

An isolated source opens only DQS1/DQSn1 while preserving the other20 byte paths and all69 power/reference pieces. Attempt119 prepares all26 RAM command/clock dogbones jointly. Its artificial bottom CPU targets are solver preparation descriptors only; the actual saved channel input keeps every real top CPU pad. No artificial terminal is exported as hardware. Manual CPU fanouts must start at those exact numeric pads.

Common facing handoffs remain congested. Left-side trials use RAM x=-9 with0.48mm exit spacing, CPU x=-16 and a26mm y offset. Initial clock exits at y=-28 hit the actual top bulk-capacitor pad; y=-30.4/-30.08 avoids it. Removing all unused native bottom branches preserves26 top pad wires but still fails aggregate fanouts. Attempt127 instead removes only CKE's unused native bottom branch, freeing the clock's adjacent escape while retaining25 native through-dogbones. Attempt128 still fails aggregate RAM fanout routing. Failed candidates contribute **zero accepted command/clock channels**.

The next command/clock run must retain or explicitly account for the newer checked reset copper. Native bootstrap outputs, temporary strobe openings and failed local fanouts cannot be counted as completed source routes. Four layers, both reference regions, all actual pads, wire clearances and same-net drill spacing remain enforced. Alternative outer-layer allocation or a revised bypass layout may need a separately rebuilt and checked source.

### Joint synchronous breakout reservation — attempt132

The fresh `am3352-joint-ddr-breakout-host.circuit.tsx` retains all69 actual power/reference pieces,882 SMT pads, both reference regions and the same corrected memory map. Its DDR channel paths are deliberately empty; the checked23-signal board remains active. Native preparation temporarily targets bottom for both bytes and command/clock, while reset remains top. This is a dogbone bootstrap only, not a final channel-layer decision.

**Native `BusLanesPipelineSolver.prepare` successfully reserves all96 CPU/RAM escapes for all48 synchronous signals together.** Each exact CPU/RAM pad has one18/10mil full-depth dogbone. This avoids freezing one byte's fanouts before providing command pins with breakout sites. The source audit checks every endpoint, layer span and diameter, and checks drill spacing across all69 existing plus96 reserved holes. Minimum hole-edge clearance is0.446mm, above0.254mm.

Evidence: `checks/integrated/am3352-joint-ddr-breakout-source-audit.json`. Source SHA256:`fe69070a7bc659551dacbb0774ac3d633de80bfd3925e3ba5bf2b562c34e6b13`. **No new end-to-end channel is counted from this reservation.** The next native phases must retain these shared breakout reservations while editing local fanouts and routing each actual channel. Unused native branches may be pruned only with explicit provenance; all manufactured power/reference copper remains fixed or separately rebuilt and checked.

### Independent joint breakout checks and command fanout trials

The native reservation diagnostic refills both existing reference boundaries around all96 signal holes. KiCad verifies every exact numeric pad-to-via connection:48 CPU and48 RAM. All18 RAM supply balls,21 ground balls and28 bypass terminals remain connected to the filled planes. All-layer Gerber shorts and clearance violations are zero. **All96 dangling-via warnings remain**, together with418 presentation warnings and499 unconnected host items. These are unfinished reservations, not a full physical-DRC or fabrication pass. Library preparation preserves all620 physical records and273 exact footprints. Evidence:`checks/integrated/am3352-joint-native-breakout-check-summary.json`; verifier:`npm run check:joint-breakout-evidence`.

Attempts134–136 complete all26 RAM left-side natural fanouts but fail aggregate CPU alignment. The four-via local crossing option preserves the same18/10mil geometry,4mil copper clearance and10mil hole-edge separation. Actual source copper and all other native reservations remain obstacles. Attempt139 tries a native bottom command channel directly from the joint dogbones with the original0.635mm/0.127mm limits; it fails with `no_planar_route` and produces no accepted channel. The alternative bottom allocation is declared in its separate source wrapper; the active top command allocation is unchanged.

Attempt145 completes **all26 CPU natural fanouts** to facing handoffs, with13 additional CPU vias. Direct RAM alignment to that order fails. Attempt146 instead reaches21 RAM fanouts toward the RAM lower edge; an extended48-pass ordering search in147 still fails. Neither contributes a completed command/clock connection.

Attempt148 composes the disjoint completed CPU natural fanouts from145 and RAM natural fanouts from135, preserving every exact source terminal. All52 command escape descriptors now contain their completed natural local routes. The44 native byte dogbones stay unchanged. Only unused, unmanufactured command via branches are pruned when a local route starts on their top land. This reserves106 signal vias plus69 original power/reference vias; all signal-hole spacing passes the source geometry check. Attempt149 aligns the already escaped CPU ends outside the BGA before another native channel phase. These local fragments still count as **zero new end-to-end channels** until independent complete-path checks pass.

The combined natural-fanout diagnostic now passes independent KiCad connectivity for all52 exact package pads to their outboard ends. All-layer Gerber shorts and clearance violations are zero. All39 RAM reference balls and28 bypass terminals retain plane connectivity. Its47 dangling-via warnings,44 dangling-track warnings,418 presentation warnings and499 unconnected host items remain; no full physical-DRC pass is claimed. Library preparation preserves all4726 physical records and273 exact footprints. Evidence:`checks/integrated/am3352-natural-command-fanouts-check-summary.json`; verifier:`npm run check:natural-command-fanouts`.

Attempt149 exhausts32 outboard alignment orders without a complete result. Attempt150 permits up to six new full-depth vias per local alignment and exhausts48 ordering passes without a complete result, with every copper and hole clearance unchanged. Both signal layers remain top/bottom; neither reference plane carries a signal. No native channel or timing pass is claimed from these incomplete alignments. The independently checked natural fanouts remain available for the next routing approach; no remote publication was made.

### Outer-layer command terminals and repair — attempts151–194

The separate `am3352-joint-ddr-dual-layer-command-host.circuit.tsx` explicitly permits command signals on top and bottom. Both inner reference planes remain reserved. Its physical and logical Circuit JSON records match the fresh host, apart from filesystem metadata. The checked 23-signal default remains unchanged.

Attempts151–157 add full-depth vias outside the natural command fanouts to provide both outer terminal lands. Attempt157 checks grid bounds and exact goal coordinates, and successfully prepares all 52 terminal paths: 51 new vias and one reused via. It retains all 69 original power/reference trace pieces and holes and all 44 native byte dogbones.

The actual terminal diagnostic independently verifies all 26 CPU and 26 RAM pad-to-terminal connections in KiCad. It has 226 through-vias, zero all-layer Gerber shorts and zero clearance violations at every severity. All 18 RAM supply balls, 21 ground balls and 28 bypass terminals still connect to the filled planes. The 96 dangling-via warnings, 418 presentation warnings and 499 host unconnected items remain. All 273 exact footprints and 4,808 physical records survive library preparation. **This is a terminal diagnostic with zero full DDR channels.** Evidence: `checks/integrated/am3352-dual-layer-command-terminal-check-summary.json`; verifier: `npm run check:command-terminals`.

The command channel is split into 24 individual connectivity phases and one clock-pair phase for the native bootstrap. The original 0.635 mm whole-command timing group is explicitly deferred in that bootstrap, retained in source and required by the final checker. The clock-pair target remains 0.127 mm. A bootstrap result without matching does not qualify DDR operation.

Native trials158/159 retain four partial command channels before `no_planar_route`. Manual sequential repairs160–174 keep every actual pad, source supply path, native fanout and drilled-hole obstacle, but trap later routes. Capacity-pipeline trials175/176 fail fixed-route promotion or static reachability; they produce no accepted output. Additional terminal vias restrict the available space.

Attempts177–184 therefore keep the natural non-clock fanouts and add only four clock-terminal vias. The native `BusLanesPipelineSolver` trial184 times out with four temporary channels, including both clocks. Attempt187 retains only the two native clock channels as an unqualified bootstrap; its clock skew is about 2.898 mm, so matching still fails. Attempts186/188 sequentially repair additional command paths but again trap later routes. Failed runs remain isolated from the checked source.

Attempt189 negotiates temporary manual bridges: fixed source copper and fanouts remain strict obstacles, while authored bridge paths may be moved to resolve crossings. Every proposed route must still meet the unchanged four-layer, 4 mil copper and 18/10 mil via geometry, 0.2 mm drill-to-pad and 0.254 mm hole-edge rules. Its 24 temporary manual paths plus two native clock paths retain two conflicts after ten passes, and the candidate is explicitly unaccepted. Attempt190's capacity solver also fails static reachability. Attempt193 resumes the temporary bridges with greater crossing penalties but retains the same conflict pair; it is interrupted to refine legal via-site search. Attempts191/192 stop at resume-prefix validation before routing.

Attempt194 resumes the unaccepted candidate using a 0.04 mm via-placement grid instead of 0.2 mm. This changes candidate-site search resolution, not via sizes or required clearances. No route from that trial is accepted without editable-source replay, exact pad continuity, all-layer shorts, independent DRC, original group/pair timing and combination with the other DDR channels.

The timing checker now correctly includes **A10–A14** in the 26-signal command group; the previous single-digit address regular expression omitted them. It asserts group sizes 11/11/26 and allows only top/bottom signal segments. The unchanged default still passes both byte and DQS limits, while its complete 49-signal check correctly fails on the 26 open command/clock signals. Its evidence verifier passes after the checker correction.

The user now requires fit in the **original G350 shell**. The 100 × 124 mm routing fixture is not the final mechanical PCB and does not fit the listed external envelope. Measured outline, mounts, ports, controls and assembly clearances are pending; see `G350_SHELL_FIT.md`. Integration into that geometry will require fresh routing checks. Fabrication remains blocked and nothing has been pushed remotely during these trials.

### Separate command connectivity milestone — attempt203

The finer via-grid trial194 retains conflicts and is interrupted for targeted terminal access. Trial195 adds the already checked RAM terminal vias for A10 and BA0. Trial199 still retains crossings. Trial200 also adds their two CPU terminal vias; the other package fanouts and original supply copper stay fixed. Trial201 verifies that every unchanged trace, physical obstacle and native clock path matches the prior bootstrap. Its changed terminal paths come from checked trial157. Attempts196/197 stop before routing because the rebind assertion initially compared package associations without applying native preparation's existing association normalization; attempt198 resolves that comparison without removing any physical pad.

Trial202 reduces its crossings to A10 and BA2. The coarse 0.04 mm wire grid still finds overlapping routes. **Trial203 also tests a 0.02 mm wire grid when a coarse path exists but overlaps temporary copper. It completes all 24 authored command bridges plus the two native clock channels with zero detected conflicts.** Via dimensions, all clearance limits and both reserved reference planes remain unchanged. Candidate-site resolution and crossing costs are search parameters, not manufacturing-rule relaxations.

The full pad-to-pad paths are saved as editable tscircuit source. Independent DRC finds a 0.04 mm A2 backtrack at the channel/RAM handoff; removing only its tip exposes another return leg. The final A2 cleanup removes same-layer wire loops and overlapping return legs, preserving every via and both package endpoints. It removes 5.461564 mm of redundant path traversal and changes no other signal. Every replacement follows existing copper. The initial and intermediate failed diagnostics remain separate from the final replay.

| Check on `am3352-command-unmatched-pruned-replay.circuit.tsx` | Result |
|---|---|
| Exact CPU/RAM pad pairs | All 26 command/clock signals; Circuit JSON and native KiCad agree |
| Copper allocation | Four layers; signals top/bottom; inner1 GND and inner2 DDR_1V5 |
| All-layer Gerber shorts | 0 |
| Independent physical violations at every severity | 0 |
| Existing power/reference copper | All 69 pieces and 69 vias retained |
| DDR / total through-vias | 130 / 199, with 0.4572 mm lands and 0.254 mm drills |
| RAM reference / bypass terminals | All 39 balls and 28 terminals reach filled planes |
| Command skew / original limit | 53.181565 mm / 0.635 mm; fails |
| Clock-pair skew / original limit | 2.897559 mm / 0.127 mm; fails |
| Open signals in this separate source | Both bytes and reset: 23 |
| Presentation warnings / whole-host unconnected items | 418 / 499 |
| Library preparation | 273 exact footprints and all 7,005 physical records preserved |
| Fabrication readiness / original-shell fit | False / unverified |

Actual Circuit JSON SHA256: `dc5757cf33c468e5fb7da9d55ff0c26e49b4cc113c1d504bdc1f0cb9a364c523`. Final checked KiCad board SHA256: `dd5020c238054a6ffafd325deb55a0559b655e76e9e630abfccc3ab185912063`. Evidence: `checks/integrated/am3352-command-unmatched-pruned-check-summary.json`; verifier: `npm run check:command-routing-evidence`. Full DDR continuity/timing correctly remains failed.

The active default still preserves the checked 23 byte/reset signals. A cross-candidate hole/via screen finds **five conflicts** if those paths are combined with the new command routes, including two different-net vias at identical coordinates. These candidates cannot be added together or counted as a complete 49-signal board. Evidence: `checks/integrated/am3352-command-byte-merge-hole-diagnostic.json`; its diagnostic command correctly exits with failure. New byte routing must use compatible shared package escapes, followed by original class/pair matching and independent checks on the combined source. No fabrication bundle or remote push was made.

### Compatible command-first byte reservations — attempts204–220

Native preparation204 retains the actual 95 command/power trace pieces, 199 holes, all 882 pads and both microSD keepouts. It prepares all 44 byte dogbones against that copper. Direct native remaining-channel trial205 exhausts negotiated lane search without a complete output. Local trial206 stops at priority-name validation; trial207 cannot escape the RAM strobe area toward right-side handoffs.

On 2026-10-03 the toolchain was updated to tscircuit 0.0.2742, tsci 0.1.2237, capacity-autorouter 0.0.955 and core 0.0.2056. Typechecking passes. Native preparation208 generates the same 44 dogbones as204. Layer selection209 restores byte0 bottom and byte1 top. Pruning210 removes only 22 unused, unmanufactured byte1 bottom branches, retaining all 44 native top pad wires, all 22 byte0 dogbones and all actual source copper.

The separate physical diagnostic has 139 trace pieces and 221 through-vias. Independent KiCad checks verify **all 22 CPU and 22 RAM byte pad-to-terminal paths** and preservation of all 26 command channels. All-layer Gerber shorts and clearance violations are zero. All 39 RAM reference balls and 28 bypass terminals retain filled-plane connectivity. Its 22 dangling-track and 22 dangling-via warnings remain; they prevent a full physical DRC pass. The diagnostic has 418 presentation warnings, 499 unconnected host items and 273 exact footprints; library preparation preserves all 7,071 physical records. **No new end-to-end byte channel is connected.** Evidence: `checks/integrated/am3352-command-first-native-byte-check-summary.json`; verifier: `npm run check:command-first-byte-breakouts`.

Trials211–214 keep the same manufacturing rules while pruning unused branches, widening the RAM search to x=-17.5 and trying a 0.04 mm candidate-via grid. They still cannot leave the strobe area. The 0.04 mm value controls candidate placement, not hole dimensions or required clearances. Boundary diagnostics215/216 identify contacts with WEn, RASn, ODT, additional command tracks and supply holes. Boundary contacts identify repair targets; they do not prove a minimum cut or authorize removing fixed power copper.

The new `am3352-command-local-access-host.circuit.tsx` deliberately opens only WEn, RASn and ODT channel copper while retaining every logical endpoint, all other 23 command paths and all 69 original power/reference pieces. It is an isolated access diagnostic, not an accepted replacement. The latest tsci build passes and native bootstrap217 again prepares all 44 byte dogbones. Trial220 reaches the left-side RAM corridor but cannot reach right-side handoffs. All three opened command signals require complete rerouting and original class/pair matching after compatible byte paths are established. The checked active byte/reset board and the checked full-command candidate remain unchanged. Original-shell mechanics and fabrication qualification are still pending; no remote push or order bundle was produced.

Trial221 routes both RAM byte0 strobe fragments to left-side handoffs, then fails on source_trace_3 (DDR_D1). Those local fragments are not independently qualified full channels and their pair skew is not accepted. Trial222 changes pair handoffs and routing priority; the RAM mask fragment reaches a handoff, but DDR_D1 also fails when attempted first. Its reachable region is bounded by A7, CKE, CASn and the neighboring byte1 mask pad wire. Both trials exit with `LOCAL_MODIFICATION_ORDER_CYCLE`; no solver remains running, no complete byte bus is saved, and no new end-to-end channel is counted. Further command/local-escape changes must retain explicit source provenance and repeat physical and original timing checks.

### RAM orientation trial — attempts223–255

The six-command access source223 opens only WEn/RASn/ODT/A7/CKE/CASn copper, retains the other20 command channels and every logical net, and preserves all69 power/reference pieces. A centralized guard accepts only the exact documented three- or six-command diagnostic opening sets. Fanout trials226–228 still fail aggregate routing and contribute no accepted full channel.

A separate source rotates RAM 180 degrees about(0,-27), while CPU and actual component placements remain fixed. All39 RAM supply/ground escape coordinates are transformed explicitly, including the prior C1 correction. Source-copper audits require the explicit rotated layout and exact180-degree placement; old paths default toRAM 0 and cannot silently replay atRAM 180. The69 power/reference pieces pass source checks, all-layer shorts, independent DRC and all39 RAM+28 bypass filled-plane connectivity. This is a separately checked placement, not a relaxation of fixed supply copper.

Native preparation 229 jointly reserves all96 CPU/RAM synchronous escapes using core 0.0.2056. Layer selection 230 restores byte0 BOTTOM and byte1/commandTOP. Pruning 231 removes only22 unused byte1 bottom branches; all96 native top pad wires remain. The unpruned diagnostic is rejected because its plane refill strands a RAM supply via; the plane guard is retained. The pruned diagnostic passes every48 CPU+48 RAM exact pad-to-terminal connection and every39 RAM+28 bypass reference connection. It has165 trace pieces/143 through-vias, zero all-layer shorts and clearance violations,74 dangling-via and22 dangling-track warnings,418 presentation warnings and499 host unconnected items. All598 physical library records and273 exact footprints are preserved. No full DDR channel is counted. Evidence:`checks/integrated/am3352-ram-rotated-180-pruned-breakout-check-summary.json`; verifier:`npm run check:rotated-breakout-evidence`.

Trial 232 completes all11 RAM+11 CPU byte0 fanouts, deriving an8-DQ-only within-byte permutation. The actual tscircuit source is rebuilt with that map. Trials233–243 preserve native reservations and explicitly rebind RAM copper owners and report names. Failed trial 242 is rejected before routing when stale report ownership disagrees with a handoff. Trial 244 keeps all RAM paths and replans CPU paths with y ≥ -10.5 mm, preventing CPU fanouts from entering the inter-package channel. All22 local fanouts complete. Trial 245 adds0.1439191898578649 mm to one RAM strobe fanout to balance their fixed lengths. Normalizing only the completed420 package-pad component associations retains every882 pad geometry and net owner.

Matched native trial 246 reaches all11 channels but fails whole-byte tuning because no shared strobe tuning corridor exists. Pair-matched bootstrap 247 retains the original0.127 mm strobe limit and defers only whole-byte matching in the intermediate solve. The original0.635 mm byte limit remains in the source, provenance and independent checker. Its11 native channels are saved as editable `pcbPath` source in `am3352-ram-rotated-180-byte0-pair-replay.circuit.tsx`. Unused future escape reservations are not exported as full channels.

The actual replay has204 components/882 pads,80 trace pieces and99 through-vias (69 power/reference+30 DDR). Independent Circuit JSON and KiCad checks agree on11 connected signals. All-layer shorts and physical DRC violations at every severity are zero;273 exact footprints and2147 physical records are preserved. All39 RAM and28 bypass connections retain filled-plane continuity. DQS0 planar skew is0 mm; whole-byte skew is16.1054563835856 mm, which **fails**0.635 mm. The other38 DDR signals remain open, with418 presentation warnings and499 host unconnected items. Source SHA256:`36cb1b7e99db09fb818299fc2f0aae61a9659a863b17c0f29f6d1112095f8731`; board SHA256:`edf60197598fd0a6a769e0b39bd798a1d9c6a529169150caf3280899bf5a3461`. Evidence:`checks/integrated/am3352-ram-rotated-180-byte0-pair-check-summary.json`; verifier:`npm run check:rotated-byte0-evidence`. Both full and detail bottom snapshots were inspected. This remains separate from the checked23-signal default and from all RAM 0 command paths.

Manual strobe extension 248 finds no clear candidate among354 guarded local trombones. Native octilinear matching 249 also fails tuning clearance, retaining11 unaccepted bootstrap channel records for diagnosis. Joint bottom preparation 250 around the saved byte0 copper fails dogbone assignment. Top preparation 251 retains all actual80 pieces/99 holes and uses the 76 exact remaining DDR pad terminals without creating new holes. Trial 252 stops at priority-name validation before fanout routing. Trial 253 completes all11 RAM byte1 fanouts but fails CPU aggregate ordering after24 replans; no new full byte1 channel is counted. Byte1-only bottom preparation 254 also fails dogbone assignment. Trial 255 reuses the same11 RAM fanouts and widens the CPU search region without changing actual source copper. Its final status is recorded separately below. Full DDR matching, stackup-aware timing, powered host, peripherals and measured original-shell integration remain required. No remote push or manufacturing bundle is produced.

Trials 255 and 256 fail CPU aggregate ordering after 32 replans, including the six-via option. Boundary diagnostics identify adjacent byte1 data/mask/strobe paths sealing a CPU ball's top-layer escape. Native CPU-only trial 257 also fails dogbone assignment around the saved byte0 copper; its virtual RAM preparation targets are diagnostic descriptors and are never exported as hardware. These trials contribute zero new channels.

Trial 258 returns to the fresh joint bootstrap, retaining all eleven native CPU byte1 through-dogbones before byte0 routing. Only the eleven unused RAM byte1 bottom branches are pruned. All 96 native top pad wires and 85 signal holes remain; all 69 source power/reference pieces are unchanged. The diagnostic exports 165 trace pieces and 154 through-vias and passes the continuous reference-plane refill guard. Independent checks are recorded separately; no completed DDR channel is claimed from these reservations. Subsequent fanouts must preserve the CPU reservations, route around their real holes, and pass original timing and physical checks together. This supersedes the failed approach of reserving CPU byte1 escapes after byte0 copper is frozen.

The early CPU-reservation diagnostic independently passes all 48 CPU and 48 RAM exact numeric pad-to-terminal connections and every RAM supply, ground and bypass-plane connection. All-layer Gerber shorts and clearance violations are zero. Its 85 dangling-via and eleven dangling-track warnings remain, together with 418 presentation warnings and 499 host unconnected items. All 273 exact footprints and 609 physical records are preserved. This provides no end-to-end DDR channels. Evidence: `checks/integrated/am3352-ram-rotated-180-byte1-cpu-reserved-check-summary.json`; verifier: `npm run check:rotated-cpu-reservations`.

Rebase 259 checks that the joint input, actual source hash, memory map and every native descriptor remain unchanged except for restoring the eleven CPU byte1 through-via branches. It reuses the eleven byte0 RAM paths, all confined to y <= -18 mm and clear of the restored CPU holes. Trial 260 replans only CPU byte0 fanouts with all early reservations retained. The actual native paths, memory owners, supply copper, signal layers and manufacturing clearances remain enforced.

Trial 260 completes all eleven CPU byte0 fanouts, retaining all eleven RAM paths and all 96 native terminal descriptors, including the eleven CPU byte1 through-hole reservations. Its fixed strobe lengths are 17.080874452027917 mm and 17.844204896855324 mm before matching; no complete byte channel is claimed from the local fanouts. Subsequent native phases must keep these early reservations throughout both-byte routing.

Trial 261 adds 0.7633304448274068 mm to the shorter fixed strobe path, balancing both at 17.844204896855324 mm. Native pair-bootstrap 262 completes eleven byte0 channels while preserving the early CPU byte1 reservations. Native strobe skew is zero; whole-byte skew remains **15.48604512861603 mm against 0.635 mm**. This new shared geometry has not yet received independent combined copper checks and does not inherit the earlier replay's physical pass.

Stage 263 retains all 33 byte0 local/channel pieces alongside the actual source and all 96 native terminal descriptors. A dedicated provenance guard checks exact source/native hashes, the saved native output, signal owners, layer/via geometry, and retention of the original timing requirements. Local and channel helpers validate this explicit phase prefix rather than treating it as newly connected source copper. Coordinated trial 264 reaches both RAM byte1 strobe handoffs, then cycles on DDR_D10. Its reachable-boundary diagnostics identify source supply vias14/20, nearby real pads, unused RAM native top wire ends and one retained byte0 fanout. It adds zero accepted byte1 channels. The next repair must retain the early CPU reservations and actual supply copper; it may need to revise unused RAM native wire handoffs before planning new local escapes. All owned solver/native-check sessions finished; no remote push, commit, fabrication archive or order was made.

## Full native via pattern with explicit RAM power bridge (269–270)

The RAM180 coordinated trials 265–267 replaced exactly eleven unused RAM byte1 tip descriptors with actual pad starts. The strict edit validator rejects any other native geometry change. These single-point starts are not physical breakout copper. The local search still trapped neighboring DQ/DM pins; the alternative bottom-start byte0 trial 268 also ended in a route-order cycle. No new complete channels were accepted from these trials.

A separate editable source, `experiments/am3352-ram-rotated-180-power-bridge-host.circuit.tsx`, now retains the full native 96-via signal pattern. It authors a 1.93137085 mm, 0.1016 mm-wide **power** trace on inner2 from existing D2 supply via `(2, -30.2)` to existing B2 supply via `(2, -31.8)`, via `(2.4, -30.6)` and `(2.4, -31.4)`. It adds no drill. Signal routing remains TOP/BOTTOM. This trace restores D2's connection when the native signal holes isolate it from the continuous pour; removing an isolated pour island must not delete this explicit copper.

Core 0.0.2056 creates Via's named ports before parent attachment and assumes two layers at that point. A diagnostic-only local adapter exposes inner2 on exactly those two named reference vias. It changes no router, physical via position, diameter or span. The exported inner2 layer, actual net and all three trace segments are independently verified. The source-copper audit requires explicit opt-in and rejects any different bridge position, layer, width or endpoints. The refill guard accepts only D2 through this exact bridge, with B2 inside the continuous plane; every other reference via must remain directly contained.

`checks/integrated/am3352-ram-rotated-180-power-bridge-breakout-check-summary.json` binds the final artifacts by SHA256. All-layer Gerber shorts are zero. Final native KiCad DRC has zero clearance violations, **96 dangling signal-via warnings**, 418 presentation warnings and 499 host unconnected items. All 96 native pad-to-via breakouts, all 18 RAM supply balls, 21 RAM ground balls and 28 bypass terminals pass independent connectivity checks. The power bridge survives native export as all three exact segments and connects D2 to the filled plane. All 273 local footprints and 623 physical records survive library preparation. The circuit contains 166 trace pieces and 165 through-vias, including 70 source power traces and 69 source vias. **Zero of 49 CPU-to-RAM channels are complete in this diagnostic.**

Preparation 269 uses native `BusLanesPipelineSolver.prepare`; 270 retains every native escape while restoring byte0 BOTTOM and byte1/command/reset TOP channel allocation. These checks qualify that breakout geometry only. Later fanouts/channel copper need fresh combined shorts, DRC, plane, continuity and timing checks. This candidate is separate from the checked RAM0 23-channel replay and the separately checked RAM180 11-channel replay. Their counts cannot be added. The original shell geometry is still unverified, and the 100 × 124 mm diagnostic fixture does not fit that shell. Run `npm run check:rotated-power-bridge-breakouts` to revalidate the saved evidence.

The full-via local byte1 trial 271 exposed an outer-layer search bug when it encountered the new fixed inner2 power trace. The correction 272 restricts wire blockage to the searched outer layers while retaining that trace as an obstacle to all new full-depth vias. Trial 272 achieved all eleven RAM and ten CPU local escapes, then exhausted its 24 CPU replans. Trial 273 retained the same eleven RAM paths and tried existing CPU vias' bottom lands; it also ended incomplete. Trials 274–275 permitted within-byte DQ exit reassignment, with strobe/mask paths fixed; neither completed all local escapes, so no new pin map was emitted or applied and no new complete byte1 channels were accepted. The local helper may reuse the fixed first RAM package during this reassignment only with the same source, native-escape hash, bus, channel layer, grid, pitch and validated actual endpoints. Any successful permutation must still rebuild the actual tscircuit source and copper ownership before native channel routing. These incomplete local paths inherit none of the checked breakout's physical qualification.

## Matched rotated byte1 replay (276–332)

The next local trials retain the exact 70-trace power-bridge source, reference geometry, 882 real pads and four-layer rules. Only unused CPU byte1/command bottom branches are pruned. Nine CPU byte1 routes start at their actual numeric top pads; both CPU strobes reuse their original full-depth native vias and start on bottom. Restricting their new return vias to the handoff corridor avoids blocking the data fanouts. The final preparatory geometry has 61 reserved signal holes. These preparation descriptors are routing inputs, not a claim of completed copper.

Trial 288 completes all 22 CPU/RAM byte1 local fanouts. Its physical diagnostic independently verifies all 22 pad-to-exit paths, all RAM reference/bypass connections, zero all-layer shorts and zero clearance violations. It still contains 50 dangling-via and 43 dangling-track warnings and no end-to-end channels. The 273 exact footprints and 3115 physical records survive library preparation. Later local edits require their own checks.

After a local strobe balance, native trial 292 completes all eleven channels. Its separately saved editable replay passes physical checks and correct numeric pad-to-pad continuity, but whole-byte skew fails at 17.927981 mm. That candidate remains recorded as `checks/integrated/am3352-ram-rotated-180-byte1-pair-check-summary.json`.

Manual trials 294–331 test local length additions against actual fixed copper and full-depth drill obstacles without adding holes or relaxing clearance. A single large D8 edit fails, while smaller edits fit. The final accepted branch contains 34 additions; the earlier pair-only branch is retained separately. Native trial **332** then runs `BusLanesPipelineSolver` in `matched-handoffs` mode with the original **0.635 mm byte and 0.127 mm differential limits present in its input**. All eleven channels solve with 0.000758615 mm byte skew and effectively zero strobe skew. The original source owns every pad and net; manual fanouts and native channels are replayed as editable `pcbPath` points.

The actual matched replay contains 204 components, 882 pads, 81 trace pieces (70 power + 11 DDR) and 111 full-depth vias (69 power + 42 DDR). Source geometry checks and native KiCad agree on eleven correct pad-to-pad channels. All-layer Gerber shorts and physical DRC violations at every severity are zero. All 18 RAM supply balls, 21 ground balls, 28 bypass terminals and the three-segment D2 power bridge pass filled-plane connectivity. Library preparation preserves all 273 footprints and 3402 physical records. The minimum hole-edge clearance is 0.255117 mm. Its full and detail top snapshots were inspected.

Source SHA256: `93584236ccc2abf71f833b2d6c55de801a3e3f4281291c013875403a156fbe39`; final native board SHA256: `dc419e1f0d832d91572c59182e566204e5fa3d33ebec1e6fff4b5d7edcfde85f`. Evidence: `checks/integrated/am3352-ram-rotated-180-byte1-matched-check-summary.json`; verifier: `npm run check:rotated-byte1-matched-evidence`; source: `experiments/am3352-ram-rotated-180-byte1-matched-replay.circuit.tsx`.

This is a **separate eleven-channel planar/physical milestone**. The other 38 DDR signals, complete powered host, USB-C/display/controls/audio, impedance and electrical timing, Linux startup and measured original-shell fit remain unfinished. There are still 418 presentation warnings and 499 host unconnected items. Neither the checked RAM0 23-signal source nor earlier RAM180 byte0/command candidates are combined with this geometry. No ordering files are released and the default entry is unchanged.

Follow-up 333 preserves this exact 81-trace replay and all real obstacles, but native preparation of the remaining byte0/command escapes fails with `No collision-free local dogbone assignment`. Isolating byte0 in 334 prepares all 22 native pad escapes. The phase-selection option changes only the connections passed to native preparation; every actual pad, keepout, existing route and hole stays in the input. Trial 337 reaches an order cycle at RAM DQM0. Routing the mask first in 338 does not escape. Trial 339 replaces only its unused RAM via branch with a single-point descriptor at the exact actual pad; trial 340 still fails. That marker is not manufactured copper, and none of these trials adds a complete checked channel.

Comparison 341 starts from the earlier, physically checked but unmatched byte1 replay and also prepares all 22 byte0 escapes. Trial 342 fails at the same mask, so the failure cannot be attributed solely to the later length additions. A separate source replays early byte0 trial 262 with the explicit power bridge, preserving actual pad ownership and audited 70-trace power copper. Its source geometry audit passes, but joint remaining-bus preparation 343 fails. This new composition is not independently physically qualified. Both-byte routing requires further coordinated escape/corridor work; the two eleven-signal candidate counts are not added. All follow-up solver handles ended, and fabrication export remains blocked before ordering files are written.

## Fixed byte0 with remaining native reservations (344–348)

Trial 344 reuses 74 byte1/command terminal descriptors from native preparation 258 against the actual early-byte0 replay. A strict rebase checks the source and input hashes, unchanged component/pad/keepout geometry, the connection map, all actual terminal positions and the authored byte0/power copper. It adds 63 future signal holes to the 97 existing holes. The eleven RAM byte1 descriptors retain top tips without new holes. The resulting diagnostic contains 155 trace pieces and 160 through-vias; the actual byte0 routes stay fixed.

Fresh all-layer Gerber checks find zero shorts. Native KiCad verifies eleven correct byte0 pad-to-pad channels, all 74 remaining CPU/RAM pad-to-terminal paths, all 18 RAM supply balls, 21 ground balls, 28 bypass terminals and the exact three-segment D2 power bridge. There are zero clearance violations at every severity. All 273 footprints and 2466 physical records survive library preparation. The diagnostic still has **63 dangling-via warnings, eleven dangling-track warnings, 418 presentation warnings and 499 host unconnected items**. Byte0 planar skew remains **15.486045 mm against 0.635 mm**; strobe skew is zero. The reservations add no complete channels, and the separately matched byte1 replay is not combined with this layout.

Evidence: `checks/integrated/am3352-ram-rotated-180-byte0-fixed-reused-reservations-check-summary.json`; verifier: `npm run check:fixed-byte0-reservations`. Circuit SHA256: `1c346099fa9651fdd96b9d0438675baa06024ac6181c830fab1d99a2333f877f`; native board SHA256: `ed10e711fa3db65c17daa398f2af60d2459595c2fa74ff445912e3e534fdcedc`. Its top/detail CAD snapshots were rendered and inspected. This qualifies only the stated reservations and existing copper, not a fabrication release.

Trials 345–348 change unused byte1 native branches into exact top-pad start markers while retaining the actual byte0 copper. Both local trials finish eleven RAM fanouts. With CPU strobe bottom branches retained, 346 cycles at the CPU strobe; with all eleven CPU starts on top, 348 cycles between mask/data approaches. Neither completes the new byte1 phase or inherits trial 344's physical checks.

## RAM180 whole-byte-swap alternative (349 onward)

The alternative source `experiments/am3352-ram-rotated-180-byte-swapped-power-host.circuit.tsx` uses the existing `memory-byte-swapped-connections.json` map with RAM180 and the explicit power bridge. Each complete group moves together: eight DQ signals plus its DM and DQS/DQSn. Command/address/reset mapping remains fixed. This follows [TI's AM335x DDR3/DDR3L swapping guidance](https://e2e.ti.com/support/processors-group/processors/f/processors-forum/1205797/am4376-about-ddr3-data-line-swapping); AM335x software leveling still needs to be configured and tested. The pin/byte-association validator passes. Improved routing is an experimental hypothesis, not an established benefit.

Native preparation 349 supplies all 96 synchronous escape descriptors, and 350 restores byte0 BOTTOM and other channel buses TOP without changing the escapes. Trial 351 rejects an incorrect priority source ID before routing. Corrected trial 352 completes all 22 byte0 local fanouts while preserving all other native reservations. Trial 353 adds 1.326173 mm to the shorter strobe locally. Native coupled trial 354 still fails with `No legal coupled corridor and package approaches`; the connectivity-only diagnostic 355 also fails to finish. These trials contribute zero accepted complete channels and have no independent physical qualification. The original byte/differential limits remain mandatory for any release.

On 2026-10-03, the official npm registry was checked again: pinned tscircuit 0.0.2742, tsci CLI 0.1.2237 and capacity-autorouter 0.0.955 were still current. Installed core remains 0.0.2056. Typechecking and the existing matched-byte1 and power-bridge evidence verifiers pass after the new helpers were added. No remote push, fabrication archive or order was made.

Trial 356 reuses the same eleven RAM paths and confines new CPU fanouts to y >= -10.5 mm. All 22 local paths then complete. After local pair balance 357, native **358 completes all eleven byte0 channels** in fourteen steps. Its strobe planar skew is effectively zero; whole-byte skew still fails at **13.888612 mm against 0.635 mm**. This shows that the earlier local paths' backtracking beyond the channel handoff was obstructing this candidate's solve; it does not qualify the complete interface.

The new editable replay builds with `--routing-disabled --disable-parts-engine`, the same workflow used for other saved native/manual paths. Native channel routing has already run separately in 358. An attempted default replay build triggered core's differential-pair lookup on the incomplete remaining phases and emitted incomplete-board errors; that output was rejected and replaced by the deliberate replay build. The saved source has zero circuit errors and exactly preserves the authored power and eleven DDR paths.

Fresh independent checks verify all eleven correct numeric pad-to-pad routes, all 18 RAM supply balls, 21 ground balls, 28 bypass terminals and the three explicit D2 bridge segments. All-layer shorts and physical DRC violations at every severity are zero. All 273 exact footprints and **2081 physical records** survive library preparation. The replay contains 81 trace pieces and **93 through-vias (69 power + 24 DDR)**, with 418 presentation warnings and 499 host unconnected items. The earlier byte0 replay used 28 DDR vias. That comparison does not imply complete DDR timing or fabrication readiness.

Evidence: `checks/integrated/am3352-ram-rotated-180-byte-swapped-byte0-pair-check-summary.json`; verifier: `npm run check:byte-swapped-byte0-evidence`; editable source: `experiments/am3352-ram-rotated-180-byte-swapped-byte0-pair-replay.circuit.tsx`. The current checked circuit is preserved at `dist/diagnostics/am3352-byte-swapped-byte0-checked/circuit.json`, SHA256 `b2a550463ac76cec7149902942f9ad01a3c4e17df5641562f1c7cb52264f284f`; native board SHA256 remains `3535ba6d10cc94fc13cfe9337cb9d79167e331ea45b901a85b07235154adc44b`. A CLI rebuild changed the project-wide filesystem metadata hash. Source/shorts/planar checks and native DDR/reference audits were refreshed against the preserved snapshot; native regeneration 377 exactly matches both the earlier 359 input and its 74 escape descriptors.

Native preparation **359 prepares all 74 remaining byte1/command terminal descriptors against this actual byte0 copper**. Phase 360 retains them while restoring the final TOP channel allocation. Unlike earlier failed joint preparations, this requires no reuse of reservations from a different source. These descriptors have not been independently physically qualified together. Trial 361 returns nine CPU and eleven RAM byte1 starts to exact top pads, keeps both CPU strobe through-vias, and retains CPU command top tips/RAM command full vias. Trial 362 cycles at RAM D8. Trial 363 additionally prunes only the 26 unmanufactured RAM command via branches into top tips, leaving every actual source hole and trace unchanged; trial 364 then cycles at RAM D10. Neither adds a complete byte1 channel, and those edited bootstraps inherit no physical check.

Follow-up trials 365/366 reorder data before the strobe pair and allow up to six local vias; both fail to complete all RAM byte1 escapes. Preparation 367 retains the eleven RAM native via branches and prunes the command branches into top tips; forced-bottom trial 368 and top-start trial 372 fail at D10. Preparation 369 replaces all 52 unused command descriptors with exact TOP pad markers, retaining the real source pads and copper; trial 370 still cycles after 58 route-order attempts. Right-facing trial 373 and outward-facing trials 375/376 also fail (376 exhausts 32 replans). No trial contributes accepted byte1 channels. Invalid 371 used a nonexistent bootstrap path and was rejected before routing. All solver handles have ended.

Native regeneration 377 uses the preserved, freshly checked byte0 source. Layer restoration 378 and pad-start preparation 379 exactly reproduce the earlier native inputs/descriptors without changing the fixed 81 traces, 93 holes, width, clearance or original timing requirements. The new bootstrap is the current reproducible starting point. The separately added USB source draft is checked independently; it is not part of these 882-pad DDR search inputs.

The new candidate remains separate from the active 23-channel RAM0 replay and the matched RAM180 byte1 replay. The default entry stays unchanged. Whole-byte matching, all other DDR phases, powered host/peripherals, Linux/software leveling, impedance/electrical timing and original-shell dimensions remain required. All owned solver handles ended without a commit or remote push.

USB follow-up runs 380/381 fail pipeline package refinement, while direct native lane bootstrap 382 routes both CPU data connections and 383 routes both CC connections. Editable manual local connections and a 0.0635mm D− loop addition produce the checked USB replay described in `docs/INTEGRATED_HOST.md`. Its fresh source, all-layer shorts, native USB/DDR/reference connectivity and physical DRC checks pass. This replay retains eleven DDR channels and still fails whole-byte matching; it is not part of the 882-pad DDR input above. Integrating it with the default checked RAM0 23-channel source requires a fresh combined routing/check pass, rather than adding separate counts.

The latest registry check finds capacity-autorouter 0.0.956. It is installed and pinned in both lockfiles; tscircuit 0.0.2742, tsci 0.1.2237 and core 0.0.2056 remain unchanged. Typechecking passes. Fresh native USB runs 384/385 produce byte-identical inputs and outputs to 382/383. Frozen circuit/board checks remain bound to their snapshots. No solver handle is live, no fabrication package or order was generated, and no commit or remote push was made.

The current default is now the combined RAM0 DDR23/shared-USB-C replay, `experiments/am3352-ddr-usbc-replay.circuit.tsx`. Its DDR connection map, both byte/reset paths and RAM reference geometry remain unchanged. Fresh all-layer shorts, independent physical DRC, actual KiCad pad connectivity and planar timing checks preserve all 23 channels. The six USB control phases use native `SOLVERS.BusLanesPipelineSolver`; same-net ownership aliases in fixed-copper routing input correct the solver's ID-only obstacle handling while retaining every original coordinate, width, layer, via and other-net obstacle. Manual local PMIC escape/ground traces remain editable in `routing/am3352-ddr-usbc-final-routes.json`. The evidence binder checks each native output against its authored route and all prior copper against the hash-bound source. See `checks/integrated/am3352-ddr-usbc-control-check-summary.json`.

This adds no DDR command/clock channels: 26 remain open. The four-layer limit and original-shell target remain in force; full timing, host completion and measured shell geometry are still required before fabrication.

## RAM0 clock and strobe continuation — 2026-10-03

Fresh phases now operate on every actual pad and all fixed DDR/USB copper of the checked combined source. `scripts/route-am3352-ddr-on-checked-source.mjs` uses native `SOLVERS.BusLanesPipelineSolver`, reserves inner1/inner2 for reference planes, and restores the converter's omitted fixed-via dimensions from the actual source holes. All 912 pad obstacles, four copper layers, 18/10 mil full-depth vias and original source timing limits remain enforced. CPU-only preparation uses explicitly non-exportable virtual opposite endpoints; manual adapters restore the actual top-side pads before any channel solve.

| Trials | Result and accepted scope |
|---|---|
| 398–410 | Clock preparation on fixed DDR23 fails at RAM local access. Opening DQS1 alone permits CPU preparation and individual manual RAM exits, but no complete clock pair. A bypass-pad obstruction and the D7/DQS1 fences are recorded. |
| 411 | Joint command/strobe native preparation fails after opening both strobes. |
| 412 | Both-strobes-open source permits a full native clock pair: four real CPU/RAM dogbones, two complete channels, 5539 steps. |
| 414–418 | Strobe bottom routing and RAM preparation fail local dogbones; top routing times out. CPU-only preparation creates two real dogbones. |
| 419–425 | Guarded manual fanouts restore all four strobe exits after extending the CPU search. Every existing copper item and physical clearance stays fixed. |
| 426/429 | Native coupled pair routing fails package/corridor search, including after the fixed fanout lengths were balanced. |
| 427 | Native continuity bootstrap completes both strobe channels. Source timing requirements remain unchanged; this intermediate solve defers matching. |
| 428 | One guarded manual trombone balances the fixed fanout lengths, but coupled run 429 still fails. This local-only candidate is not exported or accepted. |
| 430–434 | A manual carrier repair fails its clearance guard. Directional top/bottom handoff trials fail to escape both CPU strobes together. No failed geometry is promoted. |

The first replay, `experiments/am3352-ddr-usbc-native-clock.circuit.tsx`, has source SHA256 `8fd18065e5761b51b1ae10e9ff0bb5c08513f23ae06880642be76c50a78bba5c`. Its 23 connected DDR signals comprise 21 preserved original channels plus CK/CKn; DQS1/DQSn1 are open. Clock planar lengths are 34.499100/34.422483 mm, giving **0.076616 mm skew against 0.127 mm**. Exact source geometry, native pad connectivity, RAM references, preserved USB-C, independent physical DRC and all-layer shorts pass. It preserves 123 earlier trace pieces and 125 earlier holes, adding two clock traces and four holes. The complete trial has 125 trace pieces and 129 through-vias. Evidence: `checks/integrated/am3352-ddr-usbc-native-clock-check-summary.json`; run `npm run check:ddr-clock-evidence`.

The next replay, `experiments/am3352-ddr-usbc-clock-strobes-unmatched.circuit.tsx`, has source SHA256 `b873abda47fab6d420109e1bbf3376e8e995e595f5c1fc5795a7d8affafb3ee2`. It preserves every previous clock/DDR/USB trace and hole, and joins the native run 427 carriers to the guarded manual fanouts. The saver removes the unused CPU native via branch when the actual local path reuses its top land; no dangling branch is included in the authored paths. This **single source connects 25/49 DDR signals**, with 127 trace pieces and 137 through-vias. All 25 exact pad pairs, USB's 38 numeric assignments/40 connected pad and ground checks, and all 18/21/28 RAM supply/ground/bypass connections pass native independent checks. Physical DRC and all-layer shorts are zero. All 293 local footprints and 14147 physical library records are preserved; 418 presentation warnings and 499 reported host opens remain.

**DQS1 and whole-byte1 planar skew still fail at 7.145626 mm.** The positive and negative strobe routes contain two and six vias respectively, so propagation delay and return-path qualification also remain unresolved. Clock, byte0 and DQS0 planar limits still pass. The remaining 24 DDR address/control signals are open. Evidence: `checks/integrated/am3352-ddr-usbc-clock-strobes-unmatched-check-summary.json`; run `npm run check:ddr-strobe-evidence`. The default stays on the checked both-byte/reset/shared-USB-C source; these diagnostic counts are not added to it.

The shell's global CLI was found to report runtime 0.0.2444 and omit microSD keepouts in exports. Use `node_modules/.bin/tsci` (CLI package 0.1.2237/runtime 0.0.2742). Affected new exports and shorts checks were rerun. Current-project-CLI builds reproduce every non-metadata record of both frozen replays; source snapshots were not overwritten. The corrected export verifies both keepout polygons and enforces their copper restrictions with the explicit housing exception only for J_SD. All solver handles have ended. No commit, remote push, fabrication package or order was made.

Next: preserve the checked new clock and repair the DQS pair with original byte/pair limits. The original checked CPU/channel sections reach RAM-boundary handoffs DQSn1=(3.6,-18), DQS1=(3.92,-18); reusing those sections while repairing the obstructed RAM tails is a candidate to check. Equal via/package delays and controlled impedance still require qualification. Then route all 24 address/control signals and verify the entire command/clock class. Full host/peripherals, Linux bring-up and the measured original G350 shell remain release requirements.

## Repaired clock and both bytes together — 2026-10-04

Run 435 reuses the exact checked CPU/channel strobe sections through RAM-boundary handoffs (3.6,-18)/(3.92,-18). RAM-only runs 436–439 each reach one handoff but the first top route fences off the other pad. The guarded short RAM via in 440 passes preliminary geometry but 441 remains trapped on bottom. A longer positive escape reaches a full-depth via at (1.2,-25.4). Reproducible preparation 445 samples wires at no more than 0.005 mm with a 0.003 mm guard, while retaining all 125 clock-source traces, 129 physical holes and 912 pads. Run 446 reaches both RAM handoffs, using three further positive RAM vias. These local paths remain manual supplements to the checked native bus_lanes clock/byte bootstrap. The CPU/channel sections are reused checked copper, not newly generated dogbones. Crossing proposal 444 fails its unchanged copper/drill preflight and is not exported.

Joining the CPU sections to the RAM tails gives strobe lengths 53.720144/51.001321 mm. Replacing only the positive inward tuning turn between (10.723902814,-13.97236) and (10.723902814,-14.90324) with its straight outer leg removes 2.767005 mm. Guarded preflight finds a minimum 0.12 mm copper edge gap there. Actual tscircuit source validation then confirms **DQS1=50.953139 mm, DQSn1=51.001321 mm, skew=0.048182 mm**, with four/two through-vias. The original other nine byte1 lengths remain 50.535880–51.170880 mm, preserving the byte's 0.635 mm planar limit. Clock skew remains 0.076616 mm. Via/package delays, coupling and the reviewed fabrication stackup still need electrical qualification.

The frozen checked source is `dist/diagnostics/am3352-ddr-usbc-repaired-strobes-candidate/circuit.json`, SHA256 `aa7dce6e20cf0173895ecee9ed5e7dbfd8f815fba47bfc64b8dc8eed3f536ae3`. It has **127 trace pieces and 135 full-depth 18/10 mil vias**, preserving every prior 125 trace/129 hole of the clock source. All 25 exact DDR pad pairs, USB's 38 numeric assignments/40 connected checks and the 18/21/28 RAM supply/ground/bypass terminals pass independent native checks. All-layer Gerber shorts and physical DRC violations are zero; 418 presentation warnings and 499 reported host opens remain. KiCad library preparation preserves all 13831 physical records and 293 footprints. Both snapshots were visually inspected. [Bound evidence](../checks/integrated/am3352-ddr-usbc-repaired-strobes-check-summary.json); `npm run check:ddr-repaired-strobe-evidence`. The complete 49-signal audit correctly fails on 24 open address/control signals and the incomplete full command/clock timing group.

The repaired replay is the working default. Its fresh active build must reproduce every checked electrical and physical record except project metadata; `check:shorts` enforces this equivalence before checking all-layer Gerbers. Registry versions remain tscircuit 0.0.2742, CLI 0.1.2237 and capacity-autorouter 0.0.956 on 2026-10-04. No fabrication ordering bundle was produced. The current rectangular 100×124 mm fixture still does not fit the original G350 shell; measured internal geometry is required.

Next: native bus_lanes address/control routing on this complete checked source, with guarded manual fanout/channel repairs as needed. Signals remain on the two outer layers; inner1/inner2 reference planes and the four-layer maximum stay reserved. Complete the entire 26-signal command/clock timing class, full host, Linux/provisioning, final assembly/export and measured shell integration before release.

The 2026-10-04 TI nominal-length review is separate from relative planar skew. Table 7-68 uses the longest actual command/clock Manhattan distance plus 300 mils: this placement has 35.4 mm for A6/A8, giving **CACLM=43.02 mm and a nominal range of 41.75–44.29 mm**. Existing CK/CKn lengths 34.499100/34.422483 mm fall below that range. Their small pair skew is a routing milestone, not electrical qualification; retune both clocks with the complete address/control class. Recompute after mechanical placement changes. Byte DQLM references, spacing, impedance, package/via delay and return paths also need final review. [Placement-derived review](../checks/integrated/am3352-ddr25-ti-nominal-length-review.json), [TI SPRS717L Table 7-68](https://www.ti.com/lit/ds/symlink/am3352.pdf).

Address/control follow-up: native full-bus trials 447/448 fail local dogbones/planar routing respectively. Native top preparation 449 supplies actual pads without new dogbones; adapter450 retains all 127 traces,135 holes,912 pads and the checked25 paths. Manual fanout451 reaches14 RAM endpoints before exhausting handoffs. Trial452 is interrupted to expand the candidate rows inside the existing reference region. Wide-row453 ends in a reordering cycle; even CKE first is trapped on top by the negative-strobe RAM tail and adjacent reference holes/pads. No complete new signal is accepted. [Trial record](../checks/integrated/am3352-ddr25-address-control-trial-status.json). The next repair must preserve or freshly recheck both strobe/byte matching and every changed physical route. All owned solver processes have ended; no commit or remote push was made.

## CKE and joint RAM repairs, attempts 454–467 — 2026-10-04

The checked CKE-access DDR25 replay moves only the negative-strobe RAM elbow and neighbouring D7 tail/channel, retaining all 135 physical holes and every other source record. Both byte groups and all three differential pairs retain relative planar matching. Native attempt454 prepares actual CKE CPU/RAM dogbones but cannot complete its channel. Attempt455 binds those native terminals; attempt456 confirms that the RAM CKE via is enclosed by existing data/strobe copper and reference holes.

Attempt457 temporarily opens only three RAM tails (DQSn1, D1, D7), retaining their checked CPU/channel prefixes and every physical hole. This intermediate is explicitly unexportable. Attempt458 aborts at an overly strict converter-metadata comparison before routing; the guard is corrected to compare physical geometry and independently verify normalized native via dimensions. Attempts459/460 reach left-side RAM/CPU handoffs with guarded local fanouts. Native **bus_lanes attempt461** routes the intervening CKE channel. Attempt462 stages that exact channel while binding the three checked CPU prefixes. Attempt463 exhausts the restricted RAM band; attempt464 expands its upper limit from y=-18 to -16 within actual fixed obstacles and reconnects all three RAM tails.

The first DDR26 replay has a zero-length dangling CKE segment from floating-point join coordinates. The cleaned replay removes only coincident wire points below 1e-7 mm; vias and layer transitions remain. All 26 exact DDR pairs, USB and physical checks then pass, but a new CKE via isolates RAM J9/VDDQ in the DDR power plane. The strict single-plane continuity check rejects it. No reference rule is waived. A scoped DDR power-pour antipad clearance of **0.12 mm** reconnects that supply island while retaining 0.1016 mm copper, 0.20 mm copper-to-drill and 0.254 mm hole-edge minimums, unchanged GND clearance and exact outer plane boundaries. Native zone minimum thickness remains 0.25 mm. Both filled planes and all **18 supply / 21 ground / 28 bypass terminals** pass. [Bound unmatched-DDR26 evidence](../checks/integrated/am3352-ddr-usbc-cke-joint-power-plane-bounded-check-summary.json). This earlier replay still fails DQS1 and byte1 planar matching at 10.167587/10.584847 mm.

Attempt465 aborts at the layer boundary guard before saving copper; the shortcut search is corrected to exclude segments across an immediately preceding via. Attempt466 uses exact segment/circle/rectangle distance checks with a 0.003 mm guard to find ordered wire shortcuts around every current pad, hole and other trace. Attempt467 removes only two negative-strobe wire detours, retaining all **143 holes** and every other electrical/physical record. Negative/positive lengths become **51.032548 / 50.953139 mm**; pair skew is **0.079409 mm**, and both strobes now use four vias. Byte0/byte1 skews are **0.157421 / 0.635000 mm**. Clock and DQS0 relative limits also pass.

The resulting working default is **experiments/am3352-ddr-usbc-cke-matched.circuit.tsx**: 212 components, 912 actual pads, four copper layers, 128 trace pieces, 143 through-vias and **26/49 DDR channels**. Its source SHA256 is **37cce5810c43cc3f70485d5e2990512f6a2a7d8a2f35d316e02bbea0fbbf4997**; checked board SHA256 is **a5056014dbba278425bcc1521d571a67d66062d30a3c2cf73218357fad913aff**. All exact DDR pairs, 38 numeric USB assignments/40 USB connected-pad checks and all RAM references pass. All-layer Gerber shorts and reported physical DRC violations are zero; 418 presentation warnings and 499 reported/capped host opens remain. Exact library preparation preserves all 293 footprints and 13809 physical records. [Checked DDR26 evidence](../checks/integrated/am3352-ddr-usbc-cke-matched-check-summary.json); revalidate with **npm run check:ddr-cke-matched-evidence**. The fresh active build reproduces all 7939 non-metadata source records.

This is relative planar matching, not electrical timing qualification. CKE remains **49.907479 mm**, above the current placement-derived 41.75–44.29 mm nominal range; the clock pair remains below that range and requires retuning. All **23 remaining address/control channels**, package/via delays, coupling/impedance/return paths, full powered host/peripherals/Linux and measured original-shell layout remain required. The original shell target was reconfirmed on October4. The 100×124 mm fixture still does not fit; no fabricated outline, mounting positions or assembled clearance are inferred from its external dimensions. No commit, remote push or ordering package was made.

Follow-up attempts468/469 request all 23 remaining address/control signals on bottom/top while retaining all128 traces,143 holes and912 pads. Bottom fails native dogbone assignment; top exhausts native planar search. Single ODT/CSn0/RASn probes470–475 also fail or time out; no extra channel is counted. Adapter476 binds the checked DDR26 source to real ODT pad starts and retains the native bus timing requirement. Guarded manual attempt477 reaches RAM ODT to the left-side bottom handoff with one added via, but the CPU pad remains enclosed between D14/D10 top copper with no legal layer change. This unfinished fanout is not exported or added to the default. [Trial status](../checks/integrated/am3352-ddr26-address-control-trial-status.json). All owned solver handles have ended.

## ODT channel and nominal repair, attempts 478–490 — 2026-10-04

Exact via-access diagnostics478/479 inspect the reachable CPU ODT pocket against all actual pads, 128 fixed traces and 143 holes. The 0.04 mm search finds no legal via center; 0.02 mm finds three at x=-1.98, y=-9.16/-9.18/-9.20. The land/drill and physical minimums remain 0.4572/0.254 mm and unchanged. A finer search grid only samples more positions. Fanout480 reaches both outer layers but cannot exit above the package. Attempts481–484 move the left-side handoff toward the reachable corridor while preserving the source; x=-13 is reachable on top. Bottom trial485 succeeds with five CPU vias and one RAM via. The preferred top preparation486/fanout487 reaches the same corridor with four CPU vias and no new RAM via. The smaller handoff offset and finer via grid are gated to one command selected from the hash-bound checked DDR26 source.

Native **bus_lanes run488** routes the top carrier in 12.12 seconds. Run489 also routes the bottom alternative but needs six total vias. The preferred source retains run488's actual native carrier plus fanout487's four CPU layer changes at (-1.98,-9.16), (-1.18,-8.4), (-1.18,-9.48), (-2.4,-10.7). The initial complete ODT route is 47.680369 mm. That bootstrap independently passes exact DDR/USB/reference continuity, all-layer shorts and physical DRC, but fails the placement-derived nominal range. It remains separately frozen as `dist/diagnostics/am3352-ddr-usbc-odt-bootstrap-candidate/circuit.json`.

Guarded manual shortcut490 replaces only the via-free top wire section between saved points209/329. It saves **4.662088 mm**, with a preliminary minimum copper edge gap of 0.108218 mm, retaining every ODT via and every other trace. The authored nominal replay has **ODT=43.018281 mm**. Its binder recomputes the actual longest command/clock endpoint Manhattan distance across all26 class members: 35.4 mm, giving CACLM=43.02 mm and range41.75–44.29 mm under the existing TI primary-source review. This is a planar placement check; it does not qualify propagation delay or the unfinished full class.

The new working default is **`experiments/am3352-ddr-usbc-odt-nominal.circuit.tsx`**, with 212 components, 912 actual pads, four layers, 129 trace pieces, 147 full-depth vias and **27/49 connected DDR signals**. Every prior128 trace and143 hole is preserved. Frozen source SHA256: **3f2ef3f83fb4a1aaf427e24dacb24b189cbfc9a30a982d6387641c00b336d6ee**. Checked KiCad board SHA256: **df59459d6aac0c73679ee7976630a1ba64b111c544bf40d8ccd144cc1bb9b644**. Saved paths SHA256: **fd789c5a9f8d2d2eb6170f63090b8f98443b97ac6f2d6d89ef5029c983c56431**.

All27 exact DDR pad pairs,38 numeric USB assignments/40 USB connected checks,18 RAM supply/21 ground/28 bypass terminals and both connected filled reference planes pass. All-layer Gerber shorts and reported physical DRC violations are zero;418 presentation warnings and499 reported/capped host opens remain. Exact local library preparation preserves293 footprints and14149 physical records. Both snapshots were visually inspected. Both byte groups and all three differential pairs retain their checked relative planar limits. [Bound evidence](../checks/integrated/am3352-ddr-usbc-odt-nominal-check-summary.json); revalidate with **`npm run check:ddr-odt-evidence`**.

The full49-signal audit correctly fails on22 open address/control signals and incomplete command/clock matching. CKE remains49.907479 mm and CK/CKn34.499100/34.422483 mm, outside the placement nominal range. Full power/peripherals, Linux provisioning, impedance/package/via timing, final manufacturing exports and measured original G350 shell geometry remain required. The100×124 mm fixture does not fit the shell. No commit, remote push or ordering package was made. All owned solver handles have ended.

The fresh DDR27 active build reproduces all **7,944 non-metadata source records** of the frozen nominal replay. `npm run check:shorts` passes active-source equivalence and all-layer Gerber shorts. TypeScript and owned helper syntax checks pass. The fabrication guard exits before writing ordering files, as expected for this incomplete host and unmeasured shell. [Active equivalence](../checks/integrated/am3352-ddr27-active-index-equivalence.json).

Follow-up runs491/492 request all22 remaining signals while retaining129 traces,147 holes and912 pads. Bottom cannot assign collision-free dogbones; top exhausts planar routing. Individual native CSn0/RASn trials493/494 also fail. Preparations495/496 and499/500 bind the registered checked DDR27 source to its actual top package pads for guarded manual top/bottom alternatives. Manual runs497/498 and501/502 do not finish the left-side fanouts. CSn0's CPU search is confined near its pad by D14/D10 copper. Central facing-handoff RASn trials503/504 reach the RAM handoff at (-0.08,-18), using one/two added RAM vias, but cannot escape the CPU. No complete new channel is counted and none of this partial copper is promoted. The next attempt needs a guarded neighbouring CPU data-trace repair, with fresh byte/pair/reference checks, followed by a native bus_lanes carrier. [Bound trial status](../checks/integrated/am3352-ddr27-address-control-trial-status.json). All owned processes have ended; the checked working count remains27/49.

## CSn0 carrier and D14 CPU repair — attempts 505–524 (2026-10-04)

RASn's guarded local fanouts reached independent left/right CPU handoffs on top and bottom, but the native carriers timed out at attempts 507–513. Inward top CPU targets at 514–515 remained unreachable. These staged copper pieces add no accepted channel.

Attempt 516 opened only the via-free top CPU prefixes of D10 and D14, preserving their channel/RAM tails, every old physical hole and all other copper. Guarded manual CSn0 fanouts at 517 then reached the actual package pads and handoffs. Native **`@tscircuit/core SOLVERS.BusLanesPipelineSolver`** routed the top carrier at 518 in about **1.974 seconds**; joined CSn0 is **42.800714 mm**, with no added vias. The stage remained unexportable until data continuity was restored.

Native attempts 519/520 could rebuild D14 but could not finish D10. The staged D10 manual rebuild at 522 also failed. Attempt 523 restored the entire original D10 route unchanged; it clears the new CSn0 copper by **0.266096 mm**. Only D14's CPU prefix remained open. Guarded manual repair 524 reached the exact unchanged channel handoff using **two new full-depth 18/10 mil vias**, giving final D14 **50.919109 mm**. Its original channel/RAM tail stays unchanged. The intermediate repair report retained an older two-open-prefix bookkeeping count; the final source audit derives complete connectivity from all actual traces and pins rather than that staged count.

The complete replay `experiments/am3352-ddr-usbc-csn-joint.circuit.tsx` now connects **28/49 DDR signals**, with **130 trace pieces/149 through-vias**. All old 147 holes and the other 128 traces are preserved. Native KiCad verifies all 28 exact DDR pad pairs, USB's 38 numeric assignments/40 connected records and all 18 RAM supply/21 ground/28 bypass terminals. Each filled reference plane is one connected region. All-layer Gerber shorts and reported physical DRC violations are zero; 418 presentation warnings and 499 reported/capped host opens remain. Exact local footprint preparation preserves 293 footprints and 14573 physical records. Both snapshots were visually inspected. Byte0/byte1 and all three differential pairs retain relative planar matching. [Bound checks](../checks/integrated/am3352-ddr-usbc-csn-joint-check-summary.json); **`npm run check:ddr-csn-evidence`**.

CSn0 and retained ODT meet the current placement-derived nominal range. CK/CKn/CKE still need nominal tuning; **21 address/control signals remain open**. The full 49-signal audit correctly fails on those opens and the incomplete command/clock timing group. Package/via delays, impedance/return paths, full host power, storage/display/controls/audio, Linux provisioning and measured original G350 shell integration remain required. The active index rebuild reproduces all 7947 non-metadata records of the checked replay. Fabrication remains blocked before generating ordering files. No remote push or order was made.

## A5 native carrier and nominal tuning — attempts 525–535 (2026-10-04)

Fresh native top attempts on A5, A3 and WEn (525–527) timed out without new accepted copper. Registered actual-pad preparations 528/529 preserve all 130 checked DDR28 traces, 149 holes and 912 SMT pad obstacles. Two command invocations at 530/531 stopped at a trace-selection assertion; 532/533 use A5's actual `source_trace_8`. The top CPU fanout remains unreachable. The bottom fanouts at 533 succeed with one CPU and one RAM through-via. Invocation 534 stopped at an argument guard before solving; corrected native **`bus_lanes`** carrier 535 routes in **0.831 seconds**, preserving all existing copper. Joined A5 initially measures **38.744491 mm**.

The editable nominal replay inserts only a via-free octilinear bottom jog into one native carrier segment. Its 0.6 mm chamfers and 2.840698 mm lateral offset add **4.275509 mm**, giving **A5=43.020000 mm**. Both original package fanouts and vias remain unchanged; all previously checked routes and holes remain unchanged. The source audit independently reconstructs the manual/native/manual route before checking the exact declared wire insertion. This changes no clearance rule, plane boundary or physical via dimension.

The complete **DDR29** replay has **131 trace pieces/151 full-depth 18/10 mil vias**. Independent native checks verify all 29 exact DDR pad pairs, USB's 38 numeric assignments/40 connected checks, RAM's 18 supply/21 ground/28 bypass terminals and one connected region per filled reference plane. All-layer shorts and reported physical DRC violations are zero. Both byte groups and all three differential pairs keep their relative planar limits. Exact local library preparation preserves 293 footprints and 14755 physical records. Both snapshots were visually inspected. [Bound evidence](../checks/integrated/am3352-ddr-usbc-a5-nominal-check-summary.json); **`npm run check:ddr-a5-evidence`**.

This becomes the working source only after those independent checks. **20 address/control signals remain open**; the full 49-signal audit fails on those opens and the incomplete command/clock group. Clock/CKE nominal tuning, electrical timing and impedance, complete host/peripheral/Linux integration and measured original G350 shell fit remain unfinished. Fabrication stays blocked. No remote push or order was made.

## WEn nominal native carrier — attempts 536–553 (2026-10-04)

Fresh native top routing of A3, WEn and BA2 at 536–538 times out without accepted copper. Registered actual-pad preparations 539–541 retain every checked DDR29 trace, hole and obstacle. Guarded RAM fanouts succeed at 542–544, while their corresponding CPU target heights remain inaccessible. The CPU search reaches the left side at other heights, so this is a target-location failure rather than a boxed package ball. RAM fanouts are reused unchanged at 545–547, with CPU side offsets of 24 mm for A3 and 22 mm for WEn/BA2. All three complete package-fanout sets then succeed.

Native channel search is limited to the actual rectangular DDR power-reference envelope with a 0.3 mm border margin: X=−17.5…17.5 mm, Y=−38.5…9.5 mm. Every fixed trace, pad, via and obstacle is retained. The 420 completed CPU/RAM fanout pads lose only their channel-terminal component association; their geometry and copper owner identifiers remain unchanged. Initial ring adapters at 548–550 stop before solving; corrected native **`bus_lanes`** runs 551–553 complete all three separate candidate carriers in about 1.8 seconds each. A3 totals **47.601879 mm** and still fails nominal length. WEn totals **43.228641 mm**, and BA2 **43.245209 mm**, both within the placement-derived range. These candidates are separate alternatives and must not be added to one another's connection counts.

WEn's replay `experiments/am3352-ddr-usbc-wen-nominal.circuit.tsx` retains all 131 old traces and 151 old holes, adding one trace and **six full-depth 18/10 mil vias**. It connects **30/49 DDR signals**, with **132 trace pieces/157 vias**. All 30 exact DDR pad pairs, USB's 38 numeric assignments/40 connected checks, RAM's 18 supply/21 ground/28 bypass terminals and one connected region per filled reference plane pass independent native checks. All-layer shorts and reported physical DRC violations are zero; 418 presentation warnings and 499 reported/capped host opens remain. Both bytes and all three differential pairs retain relative planar limits. Exact library preparation preserves 293 footprints and 15079 physical records. Both snapshots were visually inspected. [Bound evidence](../checks/integrated/am3352-ddr-usbc-wen-nominal-check-summary.json); **`npm run check:ddr-wen-evidence`**.

BA2 uses via sites overlapping the accepted WEn copper. A3 remains outside the nominal length range. Their earlier source29 candidates cannot be merged directly. New routing must use the checked source30 obstacle set. **19 address/control signals remain open**, while clock/CKE nominal tuning, full command/electrical timing, powered host/peripherals/Linux, measured original shell geometry and final manufacturing exports remain incomplete. Fabrication stays blocked. No remote push or order was made.

## A3 carrier endpoint correction and copper checkpoint — attempts 554–574 (2026-10-04)

All new phases start from the checked WEn source, retaining 132 traces, 157 holes and 912 actual SMT pads. Native top trials 554/555 time out on A3/BA2. Preparations 556/557 bind exact package terminals to the guarded bottom fanout search. BA2's RAM fanout at 559 cannot clear the accepted WEn copper.

A3's local fanouts at 558 reach RAM (-9, -33.16) and the independently selected CPU point (-10.5, -10.5). The adapter incorrectly used a calculated CPU point (-13, -7.16) for the carrier. Native run 560 therefore routes an **invalid carrier**, not a complete A3 signal, and is never accepted. The adapter now derives every carrier terminal from the saved fanout's actual final wire point. A new pre-solver assertion checks both package endpoints. Regression invocation 562 rejects the old mismatched adapter before creating solver output. Corrected local stage 561 passes the endpoint guard, but native run 563 finds no planar route. [Bound trial and endpoint evidence](../checks/integrated/am3352-ddr30-address-control-trial-status.json); `npm run check:ddr30-command-trials`.

The front-facing RAM trial 564 fails its clearance search. Top preparation 565 and fanouts 566 reach an inward CPU exit, but native carrier 567 times out. Lower CPU target (-13, -17) succeeds on bottom at 568; its carrier 569 has no planar path. Top trial 570 cannot reach that lower target. The reachable top interval allows CPU (-13, -9.4) at 571, reusing the unchanged RAM fanout from 566 at (-9, -32.52). Native **bus_lanes run 572** routes the carrier in **14.343 seconds**. The exact joined A3 route is **45.411583 mm**, with two CPU and two RAM full-depth 18/10 mil vias. It fails the placement nominal range of 41.75–44.29 mm.

The editable replay is `experiments/am3352-ddr-usbc-a3-bootstrap.circuit.tsx`, with **31/49 DDR signals, 133 trace pieces and 161 through-vias**. All prior copper, hole dimensions, actual pads, keepouts and plane boundaries remain unchanged. A default build without the replay flags started unfinished routing phases and was rejected; that failed source is separately retained. The correct build uses `--routing-disabled --disable-parts-engine` after the native/manual routes have been authored. Its source hash is **2a3f7fb2671d07a9115db7334681715306848576324c07bb0655ae767d3e2a43**. The checked KiCad board hash is **7585e0ae27541a51ac17a1ddbecb0f462e987c85547f1c890f91478b6371769f**.

Native checks verify all 31 exact DDR pad pairs, all 38 USB numeric assignments/40 connected records, 18 RAM supply balls, 21 ground balls and 28 bypass terminals. Each filled reference plane remains one connected region. All-layer Gerber shorts and reported physical DRC violations are zero. Byte and differential-pair relative planar limits retain their earlier passes. The complete 49-signal check correctly fails on **18 remaining opens and the unfinished command/clock group**. The report retains 418 presentation warnings, 499 reported/capped host opens and the existing ignored native checks. Exact library preparation preserves 293 footprints and 15174 physical records. Both snapshots were visually inspected. [Copper-only bootstrap checks](../checks/integrated/am3352-ddr-usbc-a3-bootstrap-check-summary.json); `npm run check:ddr-a3-bootstrap-evidence`.

Wire-only shortcut search 573 finds no single cut sufficient to reach the range. Iterative search 574 finds eight conservative cuts, but its hypothetical 45.097322 mm path still fails. It saves no replacement path. The actual checked bootstrap remains **45.411583 mm**. Its registration explicitly permits subsequent staged routing as a copper checkpoint, with A3/CK/CKn/CKE nominal repairs still pending; it does not promote the checkpoint or waive timing requirements. The active default remains DDR30. Full propagation delay, impedance, coupling and return-current transitions remain unqualified. TI's [DDR3 routing specifications](https://www.ti.com/lit/ds/symlink/am3352.pdf), Tables 7-68/69, also require review of reference-plane transitions and associated bypassing. Full host, Linux, measured original shell geometry and final manufacturing exports remain unfinished. No commit, remote push or ordering package was made. All owned solver processes have ended.

## A6 independent handoffs and copper checkpoint — attempts 575–591 (2026-10-04)

All new phases retain the checked DDR31 source. Native top phases 575/576 time out on BA0/A6; actual-pad preparations 577–579 preserve 133 traces, 161 holes and 912 SMT pads. BA0's guarded top/bottom RAM searches 580/581 remain inside a small pocket bounded by CKE/WEn copper. This requires neighboring-route work rather than treating another handoff guess as a completed connection. A6's top fanouts 582 succeed, but their fixed lengths plus the straight carrier lower bound already exceed the nominal upper limit.

The local helper now permits a separately selected RAM handoff as well as a CPU handoff, restricted to one registered new command signal. Both native terminals still come from the saved fanouts' actual final wire points. A6 stages 584/585 reach CPU (-9.42, -4.8) and RAM (-3, -34.44), with fixed total length **11.844895 mm**. Top uses no vias; bottom adds one full-depth 18/10 mil via at each exit. Native top carrier 586 times out at 45 seconds. Native bottom **bus_lanes carrier 587** solves in **37.893 seconds**, giving **A6=51.715840 mm**, two vias and nominal failure. The extended top phase 591 solves in 42.668 seconds, but its **55.440562 mm** route is longer and is not merged into the checkpoint. Its success does not add a second A6 signal.

The exact replay `experiments/am3352-ddr-usbc-a6-bootstrap.circuit.tsx` connects **32/49 DDR signals**, with **134 trace pieces and 163 through-vias**. It preserves all prior traces, holes, pads, keepouts, plane boundaries and manufacturing minimums. Source SHA256: **b541e91b183675265480029dbc04850c6f4df69b5cf94fc0f73e24b5758665aa**. Filled native board SHA256: **293c39b2537cba9a67875b90c7e824be5c06fc410dee883ed4dfe167ae256696**. Exact native checks pass for all 32 DDR pad pairs, USB's 38 numeric assignments/40 connected records, RAM's 18 supply balls/21 ground balls/28 bypass terminals and one connected filled outline per reference plane. All-layer Gerber shorts and reported physical DRC violations are zero. Both byte groups and all three differential pairs preserve their prior relative planar passes. The full DDR audit correctly fails on **17 opens and the unfinished command/clock group**. It records 418 presentation warnings, 499 reported/capped host opens and unchanged ignored native checks. Local library preparation preserves 293 exact footprints and 15465 physical records. Both snapshots were visually inspected. [Bound copper checks](../checks/integrated/am3352-ddr-usbc-a6-bootstrap-check-summary.json); `npm run check:ddr-a6-bootstrap-evidence`.

Wire-only search 588 finds five cuts, but even its hypothetical **50.956231 mm** route fails; no replacement path is saved. The guarded two-via carrier search 589/590 tests **3116 octilinear bridges between 59 sampled legal via sites**. Its shortest unchecked sampled bridge totals **46.496951 mm**, already over range. None is saved. This sampled result is not a proof that every possible reroute is impossible. Existing holes and all physical rules are retained. Further improvement needs different fanouts or guarded neighboring-route repairs. The copper registration explicitly retains pending CK/CKn/CKE/A3/A6 nominal repairs and fabrication failure. The active default remains DDR30. Full command/package/via timing, impedance/return paths, powered host, display/controls/audio, Linux provisioning and measured original-shell integration remain required.

## Remaining commands on DDR32 — attempts 592–613 (2026-10-04)

Fresh native top phases 592–594 use the copper-checked 32-signal source. A7/RASn time out; CASn has no collision-free visibility path. Preparations 595–597 bind the exact package pad starts. Initial local searches 598–600 produce valid A7 bottom fanouts but fail RASn/CASn RAM exits on the left. Attempt numbers 601/602 were not issued. A7 CPU retry 603 reuses the exact RAM fanout and reaches (-10.5, -10.5); native bottom carrier 606 ends with no planar route. This does not add a connected signal.

Independent front handoffs 604/605 are obstructed. RASn/CASn RAM searches 609/610 instead enumerate front exit columns and reach (0.12, -18). The selected RASn CPU exit coincides with occupied A3 copper; CASn's CPU clearance search remains in a small pocket near its actual pad. RASn CPU retry 611 preserves its successful RAM escape and reaches (-10.5, -10.5), with two CPU and two RAM vias and fixed length 22.562094 mm. Native top carrier 612 times out at 45 seconds. The extended run 613 exhausts its frontier and fails with no_planar_route in 64.640 seconds. The tested A7/RASn corridors need neighboring-route changes; the results are not a proof that all four-layer alternatives are impossible.

[Bound terminal trials and actual-handoff proofs](../checks/integrated/am3352-ddr31-32-command-bootstrap-trial-status.json); `npm run check:ddr-bootstrap-command-trials`. All issued stages have terminal results and every native carrier terminal matches its saved fanout. No new command from these trials is accepted or added to the DDR32 count. The active default remains DDR30; the separate copper checkpoint remains DDR32, with 17 opens and explicit nominal failures. No clearance or via rule was weakened, no signal was moved onto an inner reference layer, and no commit, remote push or ordering package was made. All owned build/solver/check processes have ended. The original shell target was reconfirmed; its measured internal geometry remains missing.

## CASn neighboring-prefix access — attempts 614–625 (2026-10-04)

The checked DDR32 circuit remains intact. Staged preparation 614 opens only the via-free CPU prefix of CSn0, through cut index 26, retaining its exact tail at (-4.22, -7.18). Every other trace and all 163 old holes remain unchanged. The stage has 31 previously completed signals and one pending CSn0 repair; it is explicitly non-exportable. This precise neighboring-wire change lets CASn's CPU escape succeed, confirming the local blockage identified in trial 610.

Bottom fanouts 615 reach CPU (-10.5, -10.5) and RAM (0.12, -18), with three CPU and one RAM through-vias. Top fanouts 621, prepared independently in 620, reach the same coordinates with two vias per package. Both profiles retain 23.787190 mm of fixed planar fanout length. Native `bus_lanes` bottom carrier 616 and top carrier 622 exhaust their tested visibility paths with `no_planar_route`; top takes 65.655442 seconds. Alternative central CPU handoff 617 is obstructed.

Guarded manual carrier probes 618/619 search both outer layers, first locally and then over X ±17.5 mm, Y -38.5 to -3 mm, with up to four new vias. Both searches exhaust without a bridge. A direct actual-pad search avoids committing those fanouts. Trial 623 incorrectly treated part of its own terminal-pad clearance band as an obstruction and is superseded, excluded from routing-failure conclusions. The corrected helper permits wire contact only with the selected actual terminal pads while retaining all pad/drill and other-net clearance guards. Corrected trial 624 times out after 14,550,000 expanded states. The bounded longer run 625 exhausts after 19,037,563 states with no route in its six-via, 0.02 mm grid search. These scoped failures do not establish global four-layer impossibility; changed neighboring routes, via locations or search configuration still need engineering review. No manual path is saved and no native-leg success is claimed.

The prefix validator binds the declared slice to the checked source and rejects undeclared copper changes, owner changes and deletion of old holes. The replay saver also explicitly rejects an opened command prefix, independently of its export flag. [Guard checks](../checks/integrated/am3352-ddr32-command-prefix-guard-validation.json) pass against the actual staged source. [All twelve terminal trials, actual pad/handoff proofs and native input bindings](../checks/integrated/am3352-ddr32-casn-prefix-trial-status.json) revalidate with `npm run check:ddr-command-prefix-trials`. TypeScript and all nine changed JavaScript helpers pass. The DDR30/31/32 evidence binders reproduce their unchanged frozen summary hashes.

No complete new signal is counted: the separate checked checkpoint remains **32/49**, with 17 opens; the active default remains **30/49**. CSn0 must be restored before any staged CASn result becomes a complete replay, and changed neighboring routes require fresh timing, plane, shorts and physical checks. CK/CKn/CKE/A3/A6 nominal repairs, full electrical timing, host/peripherals/Linux and measured original G350 shell integration remain incomplete. All owned solver/check handles have ended. Fabrication remains blocked; no commit, remote push or ordering bundle was made.

## CASn joint data-access replanning — attempts 626–662 (2026-10-04)

The guarded 0.02 mm topology diagnostic finds no CPU-to-RAM CASn passage with only CSn0's CPU prefix opened, even without a layer-transition count cap. Read-only wire-omission trials retain every pad, annulus and all 163 old physical holes. Opening DQM1 alone or D10 alone does not connect the tested region; opening their pair does. This is a scoped search result, not a proof about every four-layer alternative. Staging opens only the two declared, via-free top data routes and the exact CSn0 prefix, leaving 29 previously connected signals and three required repairs.

Native whole-pad CASn phase 637 routes **23.596587 mm** on top in **21.998430 seconds**, with no new vias. Guarded CSn0 approaches and native bottom prefix phase 641 restore CSn0 at **43.897917 mm**, within its current nominal range. The two data signals remain open. Subsequent data searches and topology checks show that this CASn path closes their RAM access. No checked DDR33 replay is produced. The original native report used a nonexistent stats method; this binder derives its CASn length from the hash-bound actual output. Later drivers read the solver's real `stats` property; the original executed snapshots and reports remain intact.

Revised preparation 646 retains the exact DQM1/D10 RAM tails, starting at (-0.4, -18) and (-1.2, -18), rather than removing their fanouts. Whole-pad native CASn trial 647 times out. Guided local escapes 649/650 shift the CPU handoff to (0.12, -10.6), clearing the unchanged conservative sampling guard; RAM remains (0.12, -18). Native `bus_lanes` carrier phases **651/652** solve on bottom/top at **24.729991/24.409991 mm**, respectively, each with two planned full-depth 18/10 mil vias across its local fanouts. Both fail the current **41.75–44.29 mm** command nominal target and require tuning. Fresh manual/native CSn0 repairs **653/654 and 660/661** preserve the actual new CASn geometry and restore the same nominal CSn0 length. Each stage has **31 connected signals with DQM1 and D10 still open**, not a complete 33-signal replay.

Data-carrier searches 655/657 exhaust without a bridge; native data phase 656 times out at 120 seconds. Guarded topology checks 658/659 diagnose disconnected data-tail and CPU regions; alternate top-CASn check 662 also finds no passage. Next work must jointly replan the blocking package/data-access routes, including neighboring copper and vias when required, instead of repeatedly routing CASn while treating its two opened data signals as restored. All 37 issued phases have terminal results. Historical helper hashes resolve to captured immutable executed snapshots; no failed trial is rewritten as a successful route.

[Trial and actual-terminal evidence](../checks/integrated/am3352-ddr32-casn-neighbor-replan-trial-status.json) revalidates with `npm run check:ddr-casn-neighbor-replan-trials`. [Staging guard regressions](../checks/integrated/am3352-ddr32-data-wire-guard-validation.json) reject undeclared copper/owner changes, obstacle changes, old-hole deletion, incorrect retained tails and export of a real native routed stage. TypeScript and all 25 bound JavaScript helpers pass. The DDR30/31/32 evidence binders reproduce their frozen summary hashes, and a fresh project-tsci all-layer shorts check passes on the preserved DDR32 checkpoint. No independent CAD qualification is claimed for the incomplete staged routes. The fabrication guard stops before touching any of the 205 existing historical fabrication files.

The checked checkpoint remains **32/49** with 17 opens; the working default remains **30/49**. Four layers and the two inner reference planes remain unchanged in these trials. Whole-byte matching must be rechecked after data restoration; full DDR timing/impedance, host/peripheral routing, Linux provisioning and measured original-shell layout remain required. No commit, remote push or ordering package is made. The 100 × 124 mm fixture does not fit the original G350 shell, whose internal outline, mounts and assembly clearances are still pending.

## CASn coupled signal-hole replan and DDR33 checkpoint — attempts 663–688 (2026-10-04)

Joint CASn/DQM1/D10 native phases 663/664 fail local dogbone preparation or time out. Read-only topology trials 665–669 instead allow explicitly identified neighboring signal holes to move in the search model. Only the tested D3 wire/two-hole profile connects CASn's CPU and RAM regions, with two minimum layer transitions. This is not a global minimality proof. The checked DDR32 source is never modified, and power/ground holes remain fixed.

Preparation 670 opens only D3 and its two old signal holes (145/146), plus the previously declared CSn0 CPU prefix. It preserves the other 161 holes, all 912 pads and every other obstacle. Guarded actual-pad plan 671 supports native bottom CASn phase 673. D3 plan 675 and native bottom carrier 676 restore D3, while native CSn0 phase 681 and RESETn phase 683 restore their precise opened CPU prefixes. All opened signals are reconstructed; the new complete dictionary has 33 signals, 135 trace pieces and 169 full-depth 18/10 mil vias. DQM1 and D10 remain unchanged. Native joint phases 672/674 fail local dogbone preparation. Prefix trials 677/678 cannot reach their local tail; 679's six-via 74 mm detour is discarded. Opening RESETn's via-free prefix in 680 permits a zero-via CSn0 repair, after which RESETn receives two vias.

The initial complete replay passes independent pad connectivity, filled reference planes, all-layer shorts and physical DRC, but D3=23.065382 mm makes byte0 skew fail at 7.662401 mm. It is retained as diagnostic-only evidence. Initial sampled meander trials 684/686 reject candidates, partly because they add search margin to unchanged native stretches. The old-meander recovery trial 685 reaches its CPU handoff with one via but cannot restore RAM access in its guarded grid search. The executed helper snapshots and failure reports remain intact.

Exact segment-to-circle/rectangle/segment screening retains the manufacturing 0.1016 mm wire and clearance rules without requiring extra sampled margin on unchanged stretches. Trial **687** adds an eleven-tooth bottom D3 meander with no new holes, reaching **30.727783541 mm**. Trial **688**, on that freshly built D3-matched source, adds four bottom CASn teeth with no new holes, reaching **43.020000000 mm**. Both insertions are reconstructed from their hash-bound native/manual paths and declared points; all other 29 original DDR paths, power/USB copper, pads, keepouts and plane boundaries remain exact.

The final editable replay is `experiments/am3352-ddr-usbc-casn-nominal-d3-matched.circuit.tsx`. Its frozen source SHA256 is **3586d0bda894376291f99bd17612868a3b79334d319eed66a36c3f4fbb22ef1e**; its filled native board SHA256 is **2fa670b599e5f24ab2c328446bc04415cfb785dfadb67a400feeda03c0eed134**. Independent checks confirm **33/49 DDR pad pairs**, USB's 38 numeric assignments/40 connected records, RAM's 18 supply balls/21 ground balls/28 bypass terminals and one connected filled outline per reference plane. Gerber shorts and physical DRC violations at every reported severity are zero. Byte0/byte1 skews are **0.157421108/0.635000001 mm**, within the original 0.635 mm limit with the recorded numerical epsilon; all three differential-pair limits pass. The audit correctly fails on **16 open signals and the incomplete command/clock group**. The 418 presentation warnings, 499 reported/capped host opens and configured ignored native checks are explicit. Both snapshots were inspected.

[Checked DDR33 evidence](../checks/integrated/am3352-ddr-usbc-casn-nominal-d3-matched-check-summary.json) revalidates with `npm run check:ddr-casn-coupled-evidence`. [All 26 terminal trials, executed helpers, actual native inputs/outputs and staged restoration proofs](../checks/integrated/am3352-ddr32-33-casn-d3-coupled-trial-status.json) revalidate with `npm run check:ddr-casn-coupled-trials`. The D3 guard rejects undeclared copper/pad/hole changes, reference-hole removal and incomplete-stage export; `npm run check:ddr-d3-signal-guards`. This registers a **33-signal copper bootstrap** for further routing, with CASn nominal passing but **CSn0=45.013123 mm still outside 41.75–44.29 mm**. Pending nominal repairs are CK, CKn, CKE, A3, A6 and CSn0. RESETn=52.646543 mm is asynchronous and outside the command matching group.

The working default remains DDR30. This checkpoint does not qualify package/via delays, impedance, TI class spacing/coupling or complete electrical DDR operation. Full powered host, microSD routing, FPC display, front controls, audio, Linux installation and measured original-shell integration remain incomplete. The 100 × 124 mm fixture still does not fit the shell. Fabrication remains blocked; no ordering package or remote push is made.
# CSn0 nominal repair and coordinated trials 689–702 — 2026-10-04

The original G350 shell is the required enclosure, reconfirmed by the user on 2026-10-04. The 100 × 124 mm fixture does not fit it. No internal outline, mounting geometry or assembly clearances have been obtained; the shell integration remains unverified. Central DDR work may continue, but it needs new checks after measured mechanical integration.

The checked 33-signal CASn bootstrap remains the initial source for trials 689–701. Trial 689 attempts all sixteen missing command signals together on top. Trials 690/691 test BA2 on top/bottom, trial 694 exhausts its guarded actual-pad six-via search, and trial 696 fails the top A9 search. These scoped failures establish no global routing impossibility and add no completed copper.

Trial 692 fails before search because the shortening helper declares a duplicate identifier. Its original log and rejected executed helper are retained, separately classified as a code error. The corrected helper produces two wire-only CSn0 candidates: 44.250824 mm in trial 693 and 43.662771 mm in trial 695. The preferred trial 695 makes seven sequential top-wire shortcuts against current pads, all existing holes and other-net copper, with a 0.003 mm extra wire guard. No holes or other paths change. Its declared shortcuts are reconstructed from the native CSn0 route by the source audit.

The new editable replay is `experiments/am3352-ddr-usbc-casn-csn0-nominal-d3-matched.circuit.tsx`. It contains 33 connected DDR signals, 135 trace pieces and 169 full-depth 18/10 mil vias. Fresh actual-source and KiCad pad connectivity checks agree on all 33 signals. Both byte groups and three differential pairs retain their relative planar passes. USB-C data in both orientations, charger/control connectivity and all RAM reference/bypass connections remain checked. All-layer Gerber shorts and reported physical copper/drill violations are zero. Both new PCB snapshots were viewed. The 418 presentation warnings, 499 reported/capped host opens and configured ignored checks remain explicit.

- Source SHA256: `5c8aeb2a452df32905653abb4f747d47893af667d90949df230eea4e140f5f07`
- Native board SHA256: `ac0dc0b774faad4e29b89f17bce1aca0601ce3af2308a6a2c05996273774c021`
- Checked copper summary: `checks/integrated/am3352-ddr-usbc-casn-csn0-nominal-d3-matched-check-summary.json`
- Bound terminal trials: `checks/integrated/am3352-ddr33-csn0-coordinated-trial-status.json`

CSn0 now passes the individual 41.75–44.29 mm nominal range. This does not establish full command matching: sixteen signals are still open, CK/CKn/CKE/A3/A6 still need nominal repairs, and the CASn-to-CSn0 difference alone is 0.642771 mm. Via/package flight time remains excluded from these planar checks. The new source is registered only as a copper bootstrap; the working default remains DDR30.

Trials 697–699 explicitly open all ten existing synchronous command/clock paths and their 28 owned signal holes for a coordinated replan. Both byte lanes, reset, all reference escapes, USB, 912 pads and keepouts remain fixed. Top and both-layer trials fail global routing; bottom fails local dogbones. These stages are nonexportable and count no new connections.

Trials 700/701 explicitly open all 33 existing DDR paths and their 80 owned signal holes while preserving 102 non-DDR trace pieces, 89 other physical holes, all pads and keepouts. Five separate buses cover both bytes, address/control, clock and reset; signals use only the outer layers. The same native input times out at 45 and 180 seconds; the extended search has fourteen partial lanes and no solved output. Trial 702 repeats complete-DDR staging from the newly checked CSn0 replay, constraining commands/clock to bottom. It prepares 74 local escapes but times out in channel routing. No partial native output is accepted, no source copper is deleted, and every opened path must be restored before a candidate can be checked.

The [tscircuit DDR guide](https://docs.tscircuit.com/guides/routing-ddr) and [TI SPRS717L](https://www.ti.com/lit/ds/sprs717l/sprs717l.pdf), Tables 7-61/62/68/69, were rechecked on 2026-10-04. Routing and relative length matching do not select stackup impedance or qualify differential spacing and return paths. TI specifies class-dependent normal center spacing and a limited reduced-spacing length allowance.

`scripts/check-am3352-ddr-class-spacing.mjs` measures exact line/capsule intersections and unions their exposure on each actual signal layer. It audits inter-net DDR wires in the connected subset and excludes each differential partner for separate impedance/coupling review. **D12 fails: 32.176112 mm of reduced-spacing exposure exceeds 31.75 mm.** The other 32 connected routes pass this partial exposure test. Missing signals, non-DDR interactions, same-net meander coupling, pad/via discontinuities, filled-reference return paths, termination/ODT and the supplier stackup remain unqualified. An ordinary 0.1016 mm clearance pass does not clear this class-spacing failure.

Typechecking, syntax checks for 23 valid current/executed helpers, the expected historical syntax rejection and five registered source revalidations pass. The fabrication guard blocks before producing ordering files, with all 205 historical files unchanged. No GitHub or tscircuit push was made. Next work must repair D12 spacing and develop coordinated fanout corridors, restore all opened nets, finish DDR electrical qualification and the complete powered handheld/Linux, then apply the measured original-shell geometry before release.

## D12 spacing repair and bottom-RAM studies — trials 703–709, 2026-10-04

Trial **703** screens wire-only shortcuts against every actual pad, hole and other-net trace, using an additional 0.003 mm clearance guard and the unchanged byte1 relative limit. One legal top-wire cut reduces D12 from 51.170880 mm to **50.983197 mm**. Its analytically measured reduced-spacing exposure falls from **32.176112 mm to 28.195190 mm**, below TI's 31.75 mm allowance. All 169 holes, 134 other trace pieces, 32 other complete DDR routes and fixed logical/physical records remain unchanged. The native bootstrap provenance is retained.

The authored replay is `experiments/am3352-ddr-usbc-d12-spacing-repaired.circuit.tsx`. Fresh source and independent KiCad audits verify the same **33 actual CPU-to-RAM channels**, all 38 USB numeric-pad assignments and 40 USB connectivity records, the 18 RAM supply balls, 21 ground balls and 28 bypass terminals to filled planes. Gerber shorts and physical DRC violations at every severity are zero. Byte0/byte1 planar skews are **0.157421/0.496669 mm**; all three pairs pass their relative planar limits. The final board retains 418 presentation warnings, 499 reported/capped host opens and the existing five ignored native checks. Both layer images were inspected. [Checked source/board summary](../checks/integrated/am3352-ddr-usbc-d12-spacing-repaired-check-summary.json), [partial class-spacing audit](../checks/integrated/am3352-ddr33-d12-repaired-class-spacing.json).

This spacing audit covers inter-net DDR wires in the connected subset. Differential partners still require separate stackup-aware coupling review. It does not qualify missing signals, non-DDR interactions, same-net meanders, package/via delay, actual impedance, return discontinuities, termination/ODT or full DDR operation. Sixteen signals remain open and CK/CKn/CKE/A3/A6 nominal repairs are still required. The new checkpoint remains separate from the 30-signal default.

The bottom-RAM study is an independent placement of the same complete host source and all 49 logical DDR connections. All 96 RAM pads and 39 RAM reference escapes mirror across X onto bottom. Fourteen small RAM capacitors move to top at unchanged numeric-pad positions by rotating 180 degrees. The ZQ resistor moves to bottom beside RAM; 39 other fixed non-DDR copper pieces remain exact. Both inner planes remain reserved. The study has **212 components, 912 SMT pads, 102 trace pieces and 89 full-depth 18/10 mil vias**, with **zero routed DDR channels**.

Early builds identify capacitor/ZQ courtyard collisions, which are corrected before the frozen placement. The first otherwise-clear source reveals eight USB vias using the router's 0.3/0.15 mm defaults, with 24 native physical violations. This rejected source, board, logs and [rejection report](../checks/integrated/am3352-ram-bottom-source-via-style-rejection.json) are preserved. Making the host via style unconditional repairs these dimensions. A new immutable rebuild passes numeric-pad/net correspondence, shorts, physical DRC and independent USB/filled-reference checks, with the same presentation warnings and capped host opens. Its top and bottom images were inspected. [Corrected placement evidence](../checks/integrated/am3352-ram-bottom-via-style-corrected-check-summary.json).

Native `SOLVERS.BusLanesPipelineSolver` trials **704/705** keep all 102 fixed pieces, 89 holes, 912 pads and actual top-CPU/bottom-RAM endpoints while allocating commands/clock to top/bottom respectively. Both prepare **49 local escapes** and exhaust planar routing. Trial **706** requests ordered native package fanouts with separate left/center/right boundary regions; the CPU fanout fails without a complete bus set. Trials **707/708** swap the byte signal layers for the mirrored RAM; the same exact input times out after 60/180 seconds. The extended run ends with 14 partial lanes and 33 conflicting lanes, not a solved output. Trial **709** tries ordered fanouts with local use of both outer layers and common channel targets; CPU preparation times out. Its individual solver step exceeds the requested 60-second wall-clock window, ending at about 67.799 seconds. None of these six routing attempts has complete output or qualifies a new signal. The study does not replace or add channels to the checked 33-signal replay.

[All seven terminal trials](../checks/integrated/am3352-ddr33-d12-ram-bottom-trial-status.json) bind executed helpers, exact inputs, source evidence and terminal results. A report-field assumption and a file-list sorting mismatch in bookkeeping helpers are corrected; their rejected logs remain separate from routing/physical results. Syntax checks pass for 13 current and seven executed helpers, all six recent registered checkpoints revalidate, and typechecking passes. The active rebuild reproduces all **7957 non-metadata records** of DDR30 and passes a fresh all-layer shorts check. The fabrication guard still blocks, preserving all **205 historical fabrication files**. No GitHub or tscircuit push, ordering bundle or order is produced.

Next work requires compatible package escape corridors for all DDR groups, a complete replay and fresh combined checks, then the remaining electrical timing, host power/storage/display/controls/audio and Linux work. The original G350 shell requirement remains firm. The 100 × 124 mm fixture does not fit; its measured internal outline, mounting/button/port geometry and both-side clearances must be applied and rechecked before fabrication.

## Bottom-RAM native bootstrap and manual repair — trials 710–747, 2026-10-04

Native partition trials 710/711 preserve the checked bottom-RAM source's 102 fixed trace pieces, 89 holes, 912 pads and all 49 real CPU/RAM endpoints. Both prepare 49 local escapes and fail full routing. Trial 711's best internal partial state contains nineteen carrier paths. It is saved as an explicitly nonexportable, unsolved seed; the public `getOutput()` method is never called on an unsolved pipeline. Partitioning does not split the electrical command/clock timing class or waive cross-partition matching.

Manual trials 712–741 show that pad access depends on routing order. Opening uncommitted dogbone reservations permits seven additions to the native seed. Their first editable 26-channel replay passes exact source preservation, numeric-pad DDR/USB/filled-reference connectivity, all-layer shorts and physical DRC. Later sequences find other paths but stop with missing channels; their counts are not combined across branches. Native-carrier rip-up trials 742/743 remain unqualified and do not improve the checked candidate.

Fixed-fanout trial 744 exposes a search-model bug: the selected terminal via is exempted only inside a 0.32 mm radius, while its inflated clearance shape extends farther out. This creates a false closed ring around its own electrical terminal. The corrected helper treats the selected real terminal via as same-net copper while retaining the drill prohibition against adding another hole there. A synthetic regression confirms that the terminal can exit, foreign-net copper clearance remains enforced and a foreign-owned start remains blocked. This test is separate from PCB qualification. Trials 745–747 preserve all original source copper and holes; uncommitted native fanouts may be explicitly pruned when the actual component-side layer is used. The historical reservation-count field describes initial native inputs, not a promise that every uncommitted hole is physically retained.

Trial 747 preserves all nineteen original native paths and adds nine manual paths. Its fresh editable replay has **28 connected DDR signals, 21 missing signals, 130 trace pieces and 129 physical through-vias**. Every original host/reference/USB piece and hole, all 212 components and all 912 pads remain exact. Fresh KiCad checks independently verify all 28 numeric CPU/RAM pad pairs, 38 USB numeric-pad assignments and 40 USB continuity records, and all 18 RAM supply/21 ground/28 bypass terminals to filled reference planes. Gerber shorts and physical DRC violations at every severity are zero. The 418 presentation warnings, 499 reported/capped host opens and five configured ignored checks remain explicit. Both images were inspected; 293 exact local footprints preserve every physical record.

Both byte groups and the full command/clock group still fail because routing is incomplete. All three retained differential pairs pass the relative planar limit. The bottom placement's command/clock nominal target is **40.62 mm**, range **39.35–41.89 mm**, derived from all 26 actual endpoints; A3 alone currently meets it. This separate target does not replace the top-RAM fixture's 43.02 mm target. Every connected path passes the partial reduced-spacing exposure limit, with maximum **31.421059 mm**, but missing nets, non-DDR interactions, same-net meanders, pair coupling, impedance, returns, termination, package/via delays and the supplier stackup remain unqualified.

[Checked 28-channel replay](../checks/integrated/am3352-ram-bottom-flexible-fanout-747-replay-check-summary.json), [nominal/spacing review](../checks/integrated/am3352-ram-bottom-flexible-fanout-747-replay-spacing-and-nominal-review.json), [all 38 terminal trials and three bounded continuations](../checks/integrated/am3352-bottom-manual-trial-status.json), [terminal-via regression](../checks/integrated/am3352-bottom-terminal-via-guard-regression.json). The new bottom candidate is independent of the 33-channel D12-repaired checkpoint. The default still reproduces all 7957 non-metadata records of the checked 30-channel circuit and passes all-layer shorts. Current/executed helper syntax and typechecking pass. The fabrication guard blocks before modifying any of 205 historical files. No remote push or order was made. Measured original-shell geometry, the complete powered host/peripherals and Linux provisioning remain required.

## Latest core and native phases, attempts 748–754

The project now uses tscircuit 0.0.2744, core 0.0.2080, capacity-autorouter 0.0.958 and CLI 0.1.2237. Registry versions were checked again at the end of the update. Root Circuit JSON 0.0.515 and React/React DOM 19.3.0 pins resolve stale peer hoisting; a core override keeps the CLI and direct solver on the same class. npm and Bun locks agree.

The updated native pipeline was run on the exact checked bottom-RAM input from attempt 707. Attempt 748 used the same 60-second matching budget; 751 extended matching to 180 seconds, and 753 used a 180-second connectivity bootstrap without timing/pair constraints. All timed out with no complete solver output. Internal carrier counts are unqualified search state. The new shared-layer stage was observed, but these trials do not demonstrate a completed-channel improvement on this board.

The editable `am3352-latest-bus-lanes-ddr-phases.circuit.tsx` executes the normal Host `bus_lanes` phases. Attempt 750 reached byte0 phase 1 and failed with “No collision-free local dogbone assignment.” The earlier 749 run occurred before core unification and is not used as latest-core evidence.

Attempt 752 exposed the core SRJ importer's error when already guided differential pairs have no unrouted SRJ connection. The separate `am3352-latest-bus-lanes-ddr33-fixed-pairs.circuit.tsx` diagnostic omits only the three fully guided pair declarations while retaining their exact copper. The Host guard rejects unknown pairs, missing guides or a mismatched RAM layer/rotation. The default continues to declare all pairs. Any successful diagnostic output must be replayed with all pair definitions restored before qualification.

Attempt 754 then executed native phase 3 on the 16 open address/control connections. Its frozen input retains all 135 checked trace pieces, all 912 real pad centers/layers, all 169 fixed vias and the 32 actual package endpoints. Only top/bottom are allowed; inner1/inner2 remain reference planes. It failed after 55.688 seconds with “No collision-free local dogbone assignment.” No new DDR signal was qualified or promoted.

The updated default build passes, with 7957 electrical/physical records equivalent to the checked DDR30 source. The only reviewed migrations are two USB VBUS requirements from `"5V"` to `5` and 18 warnings for bare testpoint pads. Copper/connectivity mutation regressions confirm the equivalence guard still rejects hardware changes. Typechecking and a fresh all-layer Gerber shorts check pass. Historical DDR30, DDR33 and bottom-RAM DDR28 evidence remains separate; the 205 old fabrication files are unchanged and the fabrication guard stays closed.

Use `npm run build:latest-ddr33-phase` for the scoped diagnostic; its output directory must be fresh. The helper snapshots execution inputs on subsequent runs. [Final upgrade evidence](../checks/integrated/tscircuit-update-2744/final-summary.json), [phase preservation audit](../checks/integrated/tscircuit-update-2744/phase-754-source-preservation.json). No GitHub or tscircuit push was made.

## Command replan with checked manual fanouts — attempts 755–765

The latest registry versions were checked again at 13:00 UTC on 2026-10-04: tscircuit 0.0.2744, core 0.0.2080, capacity-autorouter 0.0.958 and CLI 0.1.2237 remain current. Both lockfiles and the checked default are unchanged.

The fixed 33-channel candidate leaves several command pads without a legal surface path to a through-via. Direct native trial 755 fails; manual searches 756/757 still find closed escape corridors. The separate editable `am3352-ddr23-command-replan.circuit.tsx` retains both checked data bytes and RESET exactly and removes ten command/clock routes for replanning. It retains all host/reference/USB copper: 125 trace pieces, 141 physical vias, 212 components and 912 SMT pads. This branch starts with 23 complete DDR channels and 26 open command/clock channels; it does not replace the independently checked 33-channel checkpoint or the default.

Actual tsci trial 758 executes the command `bus_lanes` phase with the latest core on all 26 real CPU/RAM connections. Its frozen input preserves all retained copper, all physical pads, all 52 actual numeric-pad endpoints, the full command class and CK/CKn constraints. The already fixed DQS pair declarations are omitted only in this native diagnostic to avoid the already-guided-pair SRJ importer error. Every pair declaration must be restored in a complete editable replay before qualification. Trial 758 times out without complete native output. The separately bounded bootstrap input has different bus member ordering; both input orders are recorded, and the sources are not treated as identical performance comparisons.

Manual trial 759 finds candidates for every endpoint but exhausts its static joint assignment search. Diversifying legal via corners and using forward checking with the most constrained live domain produces a 52-endpoint assignment in trial 761. The mutual foreign-via land clearance rule is then made explicit, alongside drill separation, and corrected trial 763 again assigns all 52 fanouts in 52 choices. No clearance limit is relaxed: wire width/foreign copper gap are 0.1016 mm; through-via land/drill are 0.4572/0.254 mm; hole separation is 0.254 mm and drill-to-pad clearance is 0.20 mm. All new prefixes run on top and terminate at full-depth vias for future bottom carriers. Inner1/inner2 remain reference planes.

The first appended-copper JSON has stale filled reference polygons and reports 104 inner-layer shorts. It is retained as a rejected diagnostic. The corrected export refills the original continuous boundaries using tscircuit's native copper-pour solver and the source Host's 0.12 mm pour margin. It checks that every original reference via remains in its continuous plane; independent KiCad connectivity then checks actual RAM supply/ground/bypass terminals. Signal holes receive proper plane clearances; no short or reference requirement is suppressed.

Fresh checks for the refilled trial-763 bootstrap pass: all 52 CPU/RAM numeric pads connect to their intended manual fanout vias; all 23 retained DDR channels remain connected; all 18 RAM supply, 21 RAM ground and 28 bypass terminals remain connected to the filled planes. USB retains 38 numeric-pad assignments and 40 continuity records. All-layer Gerber shorts and clearance violations at every KiCad severity are zero. There are **52 dangling-via warnings** because the command carriers are absent, **418 presentation warnings**, **499 reported/capped host opens** and the same five previously configured ignored checks. They remain explicit. Native serialization preserves all 13461 physical records and exports 293 exact local footprints. Top and bottom snapshots were inspected.

Native trials 762 (full matching, 120 seconds), 764 (connectivity bootstrap with CK constraints retained, 60 seconds) and 765 (CK pair only, 60 seconds) all time out. The clock-only trial reaches coupled-pair search. No unsolved pipeline is accessed through `getOutput()`, no new complete DDR channel is qualified and no route is promoted. All solver handles are terminal. Typechecking and current/executed helper syntax checks pass; the fabrication guard still blocks before changing any of 205 historical fabrication files. There was no GitHub or tscircuit push.

The new bootstrap is useful pad-access evidence, not a finished DDR layout. Continue command carriers from these verified exits while preserving the checked byte/reset/reference/USB copper. Complete all 49 channels in one replay, restore all pair declarations, and qualify nominal/relative timing, spacing, coupling, impedance, returns and termination. The powered host, Linux provisioning and measured original G350 shell fit remain required. The 100 × 124 mm fixture is still not the original-shell PCB outline.

[Checked manual fanout evidence](../checks/integrated/am3352-command-replan-check-summary.json), [editable native phase](../experiments/am3352-ddr23-command-replan.circuit.tsx), [native phase preservation](../checks/integrated/am3352-command-replan-native-phase-758-preservation.json), [latest registry recheck](../checks/integrated/am3352-command-replan-registry-verification.json).

### DDR38 and latest bus_lanes phase — 2026-10-04

The separate DDR38 replay passes independent numeric-pad connectivity, all-layer shorts and physical clearance checks. Both byte groups and all three pairs pass planar relative skew. The latest native bus_lanes continuation on the remaining 11 commands timed out; 14 routed command/clock nominal lengths and five class-spacing exposures require repair. Fabrication remains blocked and the original-shell fit is unverified. See [DDR38 checkpoint](AM3352_DDR38_CHECKPOINT.md) for checked evidence and exclusions. No remote publication was made.
