Abse2001/g350-linux-handheld/docs/INTEGRATED_HOST.md

# Integrated AM3352 host — 2026-10-04

Command package-access study, trials 794–808: independent KiCad verifies all **48 actual command/control pad-to-via exits** in a coherent four-layer diagnostic retaining 25 complete DDR channels. Filled RAM planes, USB, shorts and physical clearance/drill checks pass; 48 dangling-via warnings, 418 presentation warnings, 499 reported/capped host opens and five ignored checks remain explicit. Six native and five manually planned command carriers have not been combined or qualified. The checked DDR42 subset remains the best connectivity result. [Bound package-access evidence](../checks/integrated/am3352-command-compatible-fanouts-802-check-summary.json).

Latest separate routing checkpoint: **DDR42**, with seven DDR signals open, zero all-layer Gerber shorts and zero reported physical clearance/drill violations. Both bytes and all three pairs pass relative planar skew, but seventeen command/clock nominal lengths and seven reduced-spacing exposures still fail. The latest `bus_lanes` command phase and subsequent coordinated package-exit trials have no complete new output. The default remains DDR30. The full host/Linux implementation and measured original-shell fit remain incomplete; **fabricationReady=false**. See [current DDR routing record](AM3352_DDR_ROUTING.md#latest-checked-partial-routing-ddr42) and [checked DDR42 evidence](../checks/integrated/am3352-command-fine-782-replay-check-summary.json). Older milestones below retain their original scope.

The historical unmatched `experiments/am3352-ddr-usbc-cke-joint-power-plane.circuit.tsx` candidate adds CKE and connects **26/49 DDR signals** on four layers, with 128 trace pieces and 143 through-vias. Native bus_lanes supplies its CKE channel; guarded manual fanouts rebuild three RAM tails. Exact DDR/USB endpoints, RAM supply/ground/bypass connections, all-layer shorts and physical DRC pass after repairing a floating RAM supply-plane island. **DQS1 skew is 10.167587 mm and byte1 skew is 10.584847 mm, which was repaired by the later DDR26 default.** CKE's 49.907479 mm route also needs placement-derived nominal length repair. The other 23 address/control signals and complete host/shell qualification remain required. [Bound evidence](../checks/integrated/am3352-ddr-usbc-cke-joint-power-plane-bounded-check-summary.json); revalidate with `npm run check:ddr-cke-joint-plane-evidence`.

Current working source (2026-10-04): `experiments/am3352-ddr-usbc-wen-nominal.circuit.tsx`. One checked four-layer replay connects **30/49 DDR signals**, with 132 trace pieces/157 through-vias. Native `bus_lanes` supplies WEn's carrier inside the DDR reference-region bounds, supplemented by guarded manual package fanouts. **WEn=43.228641 mm** is within the placement nominal range. All checked DDR29 copper and holes remain unchanged. Both byte groups and all three differential pairs retain their relative planar limits. Exact native DDR/USB/reference continuity, all-layer shorts and reported physical DRC pass. CKE/clock nominal lengths still fail. The **19 address/control opens**, full command matching and electrical timing, complete powered host/peripherals/Linux, measured original-shell geometry and final manufacturing exports remain incomplete. **Not order-ready.** [Evidence](../checks/integrated/am3352-ddr-usbc-wen-nominal-check-summary.json); `npm run check:ddr-wen-evidence`. Entries below record earlier milestones.

The user selected **AM3352** and accepted CPU rendering for simple games. The computer must be built from individual chips on the handheld PCB. Both assembly sides and both outer routing layers are allowed. The required controls are eleven front buttons, no analog sticks and no rear buttons. The display needs an FPC connector, storage needs an onboard microSD holder, and a single USB-C connector must support charging and data/provisioning.

The user confirmed that the PCB must fit the **original G350 shell**. The current 100 × 124 mm board is a routing fixture and does not fit the listed 81 mm outside width. Original PCB perimeter, mounts, controls, ports and assembly clearances are pending; outside case dimensions cannot substitute for them. Mechanical fit is an explicit release requirement. See [G350 shell fit](G350_SHELL_FIT.md).

## Current parts

| Function | Part | JLCPCB part | Verified scope |
|---|---|---|---|
| Linux processor | AM3352BZCZ100, 1 GHz Cortex-A8, 324-ball ZCZ | C468247 | tsci import; all primary ball functions, 0.8 mm grid and 0.4 mm nominal lands checked |
| RAM | MT41K256M16TW-107:P, 4 Gb x16 DDR3L, 96-ball TW | C253882 | tsci import; full primary ball map, 0.8 mm grid and 0.42 mm nominal lands checked |
| PMIC source stage | TPS65217CRSLR | C116081 | Individual tsci import; generated rail/control netlist checked against TI; paste, thermal vias, routing and startup qualification pending |
| microSD holder | Hirose DM3D-SF | C719027 | Individual tsci import; 14lands, pitch, card-detect operation and no-copper regions checked against manufacturer drawing |
| MMC0/card regulator | TPS62162DSGR | C40256 | Fixed3.3V/1A source and startup-enable wiring checked; layout/load qualification pending |
| Reset supervisor | TPS3808G33DBVR | C43698 |1.8V reset output domain,3.3V sensing, PMIC PGOOD→MR and20ms nominal delay checked |

The memory is **512 MB**, single rank, with A0–A14. AM3352 DDR_A15 is unused with this part. Micron documents DDR3L compatibility at VDD=VDDQ=1.5 V ±0.075 V; the AM3352 DDR domain must be powered separately from its other supplies. The selected DDR3L part's higher speed grade does not raise the AM3352 controller's supported limit.

Supplier libraries are component sources, not an implementation specification. Corrections are recorded with original and corrected import hashes in `lib/am3352/*-ball-map.json`. All 420 balls remain in the circuit and routing obstacle set. Numeric pin selectors avoid ambiguous RAM aliases such as ball A3 versus address A3.

## Native DDR bootstrap

Read [tscircuit's DDR routing guide](https://docs.tscircuit.com/guides/routing-ddr). The public `bus_lanes` preset creates local dogbones for direct pad connections, connects each bus without intermediate vias, includes planar fanout lengths in matching, and couples declared differential pairs. It requires compatible endpoint layers. When it cannot route, adjust package placement, fanout directions, layers and available corridor space; add explicit manual escapes when needed.

The isolated signal fixture is `experiments/am3352-ddr-clearance-bootstrap.circuit.tsx`. The earlier byte/reset entry was `experiments/am3352-guided-both-bytes-and-reset-replay.circuit.tsx`; the current default is the checked DDR30/WEn/shared-USB-C replay; the separate powered-host file remains the base power/netlist draft. Both have 49 DDR traces, byte0 and byte1 buses (11 signals each), a combined command/clock timing group (26 signals), and asynchronous reset. TI's 25 mil intra-byte/class and 5 mil differential planar skew limits are configured as 0.635 and 0.127 mm. The active trial requests a 0.12 mm differential gap; other trials use 0.127 mm. Both remain provisional until the exact stackup establishes the required impedance.

The active integrated board is limited to **four copper layers**. TI SPRS717L Tables 7-61/62 specify top/bottom signals, inner1 ground and inner2 power. `FourLayerDdrConstraints.tsx` reserves those inner reference regions and uses 18 mil via lands/10 mil drills. The active replay routes byte0 on bottom and byte1 on top; the checked clock uses bottom and reset uses top. Remaining address/control fanouts may use both outer layers. No inner signal routing is allowed. Both reference regions render. Native preparation reserves the 44 byte signal escapes before assigning all 39 RAM supply/ground escapes. Explicit tscircuit vias implement those escapes; manual traces connect both terminals of its 12 high-frequency and two bulk capacitors to the planes. The separate CPU bypass loop remains. Complete CPU/PMIC supplies, final plane continuity, impedance and stackup qualification are still required.

KiCad's native connectivity engine verifies every RAM supply/ground ball and all 28 RAM bypass terminals reach the actual filled reference planes. All-layer Gerber shorts and independent physical DRC pass on this partial copper, with 418 presentation warnings and 499 unconnected host items retained. That earlier reference-only stage had zero complete DDR channels. Its evidence remains `checks/integrated/am3352-ram-bypass-check-summary.json`; the current release state is below.

The historical first-byte diagnostic contains the exact native routes from attempt 10: **11/49 connected signals**, **22 full-depth vias**, **0 all-layer Gerber shorts**, **0 KiCad physical violations**, and passing first-byte/DQS0 planar skew. The other 38 signals are open. The native second-phase timeout remains in the diagnostic Circuit JSON. The 0.35/0.15 mm dogbone construction removed 31 drill-clearance errors seen with the original 0.30/0.15 mm vias; it is still an unqualified fabrication process. See `AM3352_DDR_ROUTING.md` and `checks/integrated/am3352-clearance-11-check-summary.json`.

Attempt 19 also checks the first byte on the actual 142-component power/DDR placement: eleven connected DDR signals, twenty-two vias, zero Gerber shorts, zero KiCad copper/drill errors and passing byte0/DQS0 planar skew. It retains 402 silkscreen warnings and 499 unconnected host items, plus the failed byte1 phase. This is a partial integrated routing diagnostic; the source/netlist-only build has no copper. See `checks/integrated/am3352-host-byte0-19-check-summary.json`.

Attempt21's four-layer185-component diagnostic remains historical: it routes byte0 on inner1, which is reserved for ground in the current candidate. Its physical checks do not qualify the new204-component placement. Attempts26/27 use only outer signal layers and prepare44 local byte escapes; both exhaust native planar channel search. Current DDR continuity is0/49. Failures remain recorded; see `AM3352_DDR_ROUTING.md`.

## Clock and boot source

The individually imported TKD SX32Y024000BC1T001 (C7420736) provides 24 MHz with a 12 pF specified load, 40 ohm maximum ESR and 3 pF maximum shunt capacitance. Two 18 pF C0G capacitors are initial prototype values; actual parasitics and oscillator startup require qualification. A populated zero-ohm damping resistor and a DNP 1 Mohm bias option retain separate signal terminals and real assembly lands.

Sixteen external 10 kohm straps select `SYSBOOT=0x4017`: 24 MHz, MMC0 then SPI0, UART0 and USB0, per SPRUH73Q Table 26-7. The board includes warm reset and fourteen 1.5 mm SMT UART/JTAG access pads. RTC-only operation is unused, with RTC_XTALIN and RTC_XTALOUT explicitly NC. The independent generated-netlist audit checks these actual terminals, values, DNP lands and SMT pads in `checks/integrated/am3352-boot-validation.json`. This is logical source/placement validation; no clock/boot copper or tested installer exists yet.

## PMIC investigation

TI's TPS65217C sequencing guide specifically addresses AM335x ZCZ. Default rails are DCDC1=1.5 V for DDR, DCDC2=1.1 V for MPU, DCDC3=1.1 V for core, LDO1=1.8 V for VDDS/RTC, LDO3/LS1=1.8 V for PLL/analog/SRAM and LDO4/LS2=3.3 V for appropriate high-voltage I/O/USB analog domains. The default MPU voltage does not qualify 1 GHz operation; firmware must select a supported voltage/OPP. Every CPU domain and decoupling requirement needs its own verified connection.

PMIC PGOOD drives TPS3808 MR; its3.3V SENSE monitors the additional MMC0/card rail before releasing CPU PWRONRSTn at1.8V. PGOOD is push-pull and must not be wired together with the supervisor's RESET output. LDO_PGOOD drives RTC_PWRONRSTn and PMIC_PWR_EN controls PWR_EN. PMIC nRESET is a shutdown input. INT_LDO/BYPASS cannot power external loads. The C variant lacks RTC-only mode. Its charger is limited to700mA and bucks to1.2A each; the full power/thermal budget remains incomplete.

The source draft wires 73 CPU supply terminals, 43 CPU grounds, every RAM power/ground/reference/calibration terminal, PMIC buck stages and reset/enable/I2C. It includes 98 CPU/RAM decouplers, including 20 CPU and 12 RAM 0402 DDR capacitors on the bottom side and two bulk capacitors per package. An actual generated-netlist audit checks these connections, nominal counts, internal-output isolation and nearby terminal distances. The RAM supply/ground and 14 bypass capacitor connections now have independently checked copper; the rest of the powered host is incomplete. VPP is explicitly NC for functional GP operation, following TI's AM3352-specific guidance.

HV1–3 use1.8V; HV4 (MMC0) shares PERIPH_3V3 with the card, while HV5/6 and USB analog3.3V stay on IO_3V3. Conservative CPU-only totals are55mA on LDO1,265mA on LDO3,230mA on LDO4 and50mA on the separate peripheral rail. Memory/card/display/audio transients and losses still need a full budget. PMIC VIO is1.8V; I2C pull-ups use HV6's3.3V.

## microSD and reset source

The right-edge DM3D-SF socket has8card contacts,2card-detect switch contacts and4grounded shell lands. Its0.5A contact rating and active-low detect wiring are checked against Hirose's drawing. Both top no-copper regions are modeled; all socket lands remain outside them. TPS62162 powers both the card and CPU VDDSHV4 bank. CMD/DAT0–3 have10kohm pull-ups to that rail. A33ohm clock resistor is2.97mm from the actual CPU clock pad; firmware must enable RXACTIVE for MMC0_CLK. The socket's100nF bypass is2.18mm from its VDD contact. The TPS3808 supervisor waits for both PMIC PGOOD and that rail before releasing CPU reset. `check:storage-netlist` checks the generated nets, actual placements and keepouts; storage copper and startup testing remain incomplete.

A TPS61023 5 V boost supplements VINLDO and LS2_IN to preserve LDO headroom on battery. Its source-stage inductor/divider/capacitors are present; startup, tolerance, feedback stability, USB input limit, battery discharge protection, switching layout and thermal performance remain unqualified. Present testpoint input pads are placeholders for the qualified USB-C and protected battery/NTC connections. The power button is present; game controls are not yet integrated. See `checks/integrated/am3352-power-validation.json`.

## Shared USB-C and Linux provisioning

AM3352 provides USB2.0 interfaces and a boot ROM; one USB-C connector can carry USB0 data and input power for a charger/power path. The circuit needs correct CC sink termination, VBUS sensing, ESD protection, differential routing, battery protection and control of reverse current. Charger/PMIC choice and integration remain unfinished.

An onboard microSD socket is required. A USB-loaded installer or a running Linux USB gadget can write that storage, but boot ROM support alone does not implement an SD installer. The boot straps, reset/recovery control, compatible SPL/U-Boot DDR configuration, installer and Linux device tree must be designed and tested for this board. Historical Pi/Rockchip flashing commands do not apply.

## Release state

The active `am3352-guided-both-bytes-and-reset-replay.circuit.tsx` connects **23/49 DDR signals on four layers**, with both bytes and both DQS pairs passing their original planar-skew requirements. Native `bus_lanes` routes and matches the channels; manual package dogbones, fanouts and local tuning supplement it. All 22 checked byte paths are preserved exactly. Reset uses manual top-layer pad escapes and a completed native channel with no new vias. Byte1 uses the other outer signal layer and a permitted within-byte DQ map. Only RAM C1's reference via moves; all39 RAM reference balls and 28 bypass terminals still reach their filled planes.

The source contains 204 components, 882 actual SMT pads, 92 trace pieces and 109 through-vias (40 DDR plus69 power/reference). Independent checks verify23 exact CPU/RAM pad pairs, zero all-layer Gerber shorts and zero physical violations at every severity. Both byte skews are 0.635 mm; DQS0/DQS1 skew is approximately zero. It retains 418 presentation warnings and 499 unconnected host items. **26 DDR command/clock signals and full electrical timing remain unfinished.** Evidence: `checks/integrated/am3352-guided-both-bytes-and-reset-check-summary.json`. The following experiments are historical intermediate results.

A new **separate 26-signal command/clock candidate** passes exact pad connectivity, all-layer shorts, all RAM reference/bypass connections and physical DRC at every severity. It uses native `bus_lanes` bootstrap paths and manual repairs in editable tscircuit source. Its 53.182 mm command skew and 2.898 mm clock skew fail the original 0.635/0.127 mm limits. The candidate has no byte/reset routes and conflicts with five vias in the active byte layout. It therefore does not replace the default or establish a complete DDR interface. See `checks/integrated/am3352-command-unmatched-pruned-check-summary.json` and the latest routing record.

The separate `am3352-guided-byte0-pair-matched-replay.circuit.tsx` experiment now contains eleven complete DDR paths authored through tscircuit `pcbPath`. Native `bus_lanes` supplies the bootstrap and channel; manual outer-layer fanouts and two 45-degree DQS trombones supplement it. The replay retains every original source connection, all 882 SMT pads and all 69 RAM/CPU bypass/reference copper pieces. It passes all-four-layer Gerber shorts, native KiCad pad-to-pad connectivity for eleven signals, all 39 RAM supply/ground and 28 bypass-terminal plane connections, and physical DRC at every severity. Its 95 through-vias include 26 DDR vias. DQS0 planar skew is approximately zero, but byte0 skew remains 16.273 mm against 0.635 mm. The other 38 DDR signals and complete host remain unfinished. This candidate is kept separate from the default source; see `checks/integrated/am3352-guided-byte0-pair-matched-check-summary.json`.

`design-status.json` has `fabricationReady:false`. The 204-component source includes storage and reset, two rendered reference regions, 39 native RAM reference escapes and 15 bypass loops (14 RAM and one CPU). The base power-source experiment has 69 traces and69 through-vias; the active replay adds 23 DDR signal paths and 40 DDR vias. These do not complete the DDR channel or powered host. USB data/charging interface, FPC display, game controls and audio are still missing. It cannot boot Linux. Release requires the complete powered circuit, fully routed four-layer copper, shorts/connectivity/DRC, stackup-aware DDR/USB qualification, matching fabrication/assembly files and tested provisioning. Changes remain local.

Historical RK3566 experiments are retained in `RK3566_HOST_RECORD.md` and `RK3566_MEMORY_EXPERIMENTS.md`. Their partial-route passes are not AM3352 evidence. Revision B is an external Pi carrier and its order files do not satisfy this integrated architecture.

The command-first diagnostic now physically verifies all 44 native byte pad-to-terminal paths against retained command copper. It adds 22 through-vias and retains the existing 26 full command/clock paths. Gerber shorts and clearance violations are zero; its 22 dangling-track and 22 dangling-via warnings remain. RAM plane connectivity passes. This adds no complete byte channel, and command timing still fails. Evidence: `checks/integrated/am3352-command-first-native-byte-check-summary.json`. The separate access source temporarily opens WEn/RASn/ODT to plan byte fanouts; every opened signal requires rerouting. The default checked 23 byte/reset paths and the full-command candidate remain separate and unchanged.

The latest separate placement rotates RAM 180 degrees and explicitly transforms all supply/ground escapes. Independent checks pass all 96 native synchronous pad-to-terminal connections, with 74 dangling-via and 22 dangling-track warnings retained. A replay now connects eleven full native byte0 channels with zero all-layer shorts and physical DRC violations, preserving all RAM plane/bypass connections. Its strobe skew is zero; whole-byte skew fails at 16.105 mm against 0.635 mm. It contains 80 trace pieces and 99 through-vias. The active 23-signal replay is unchanged; its old RAM orientation and command paths cannot be merged with this placement. See `checks/integrated/am3352-ram-rotated-180-pruned-breakout-check-summary.json` and `checks/integrated/am3352-ram-rotated-180-byte0-pair-check-summary.json`. Complete DDR/host qualification and the measured original-shell outline remain required.

## Primary sources

- [TI AM3352 product](https://www.ti.com/product/AM3352) and [SPRS717L datasheet](https://www.ti.com/lit/ds/symlink/am3352.pdf): ZCZ functions pp15–17, DDR3 routing pp170–188, ZCZ lands p261.
- [Micron selected-part datasheet](https://www.lcsc.com/datasheet/C253882.pdf): 4Gb_DDR3L Rev Q 12/17, voltage p1, x16 map p17, TW package p27.
- [tscircuit DDR guide](https://docs.tscircuit.com/guides/routing-ddr): native `bus_lanes`, fanouts, timing groups and verification.
- [TI TPS65217 datasheet](https://www.ti.com/lit/ds/symlink/tps65217.pdf), SLVSB64I, and [AM335x sequencing guide](https://www.ti.com/lit/ug/slvu551i/slvu551i.pdf), SLVU551I: candidate rails, reset connections, variant and charger limits. Full circuit and thermal qualification pending.

The latest separate RAM180 breakout diagnostic retains all 96 full-depth native signal vias using an explicitly authored inner2 power bridge between existing D2/B2 supply vias. All native pad-to-via and RAM reference/bypass connections pass; all-layer Gerber shorts and native clearance violations are zero. Its 96 dangling signal vias and all 499 host unconnected items remain. This establishes local escapes, not complete DDR channels or a powered host. The source and scoped evidence are described in `docs/AM3352_DDR_ROUTING.md`; the active checked RAM0 replay remains unchanged.

A subsequent separate editable replay now completes **all eleven byte1 channels**, with native `bus_lanes` routing and 34 manually authored local length additions. Native trial 332 and the actual tscircuit replay both pass the original byte/strobe planar limits: 0.000759 mm and effectively zero skew respectively. Independent KiCad and Gerber checks pass correct pad connectivity, all RAM reference/bypass connections, shorts and physical DRC. It contains 81 trace pieces and 111 through-vias; all 273 footprints and 3402 physical records are preserved. The remaining 38 DDR signals and full host/mechanical/electrical qualification are still unfinished, with 418 presentation warnings and 499 host unconnected items. See `checks/integrated/am3352-ram-rotated-180-byte1-matched-check-summary.json` and `npm run check:rotated-byte1-matched-evidence`. Other candidates remain separate, and this does not establish order readiness or original-shell fit.

The shared USB-C hardware is now implemented in the separate `experiments/am3352-usbc-device-source.circuit.tsx` draft: 212 individual components on four layers. TYPE-C-31-M-12 VBUS feeds TPS65217 pin12, and USB0 DP/DM use ZCZ N17/N18 through USBLC6-2SC6. CC1/CC2 have separate imported 5.1kohm resistors. USB0 ID/CE/DRVVBUS and all unused USB1 signal terminals are explicitly open. There are no data-series resistors, external data capacitors, or data test points. VBUS sensing uses a 1.2kohm resistor, 100nF capacitor and imported BZT52B5V1, with physical pin1 explicitly corrected to cathode. The manufacturer specifies 5.0–5.2V at 5mA/25C; temperature/transient protection against the CPU's 5.25V limit remains unqualified. TPS65217 defaults to 500mA USB input, so legacy USB attach/suspend and negotiated charging limits still require a qualified current policy. Battery connector/NTC qualification is also pending.

Generated connections, all 36 exported USB numeric-pad net assignments, unchanged eleven DDR pad-to-pad channels and all RAM reference/bypass connections pass. The USB-extended board has zero all-layer shorts or physical DRC violations, retaining 418 presentation warnings and 499 unconnected items. Its USB tracks are entirely unrouted. Exact serialization preserves 281 footprints and all 2089 physical records. Evidence: `checks/integrated/am3352-usbc-device-check-summary.json`; verifiers: `npm run check:usbc-device-netlist` and `npm run check:usbc-device-evidence`. The default 204-component/23-DDR-channel entry is unchanged. None of these separate candidate counts are added, and no Linux USB installer, complete host timing or original-shell fit has been established.

The saved swapped-byte0 replay was rebuilt during this integration. The CLI hashes project documents/check reports as well as circuit source, changing the generated source metadata identity. A fixed snapshot is now preserved at `dist/diagnostics/am3352-byte-swapped-byte0-checked/circuit.json`; source, shorts, planar and native DDR/reference checks were refreshed. Native preparation 377 produces exactly the same input and 74 descriptors as historical 359. Preparations 378/379 reproduce the current editable terminal bootstrap without weakening physical rules.

The subsequent `experiments/am3352-usbc-routed-replay.circuit.tsx` adds actual USB copper. Native lane run 382 routes CPU N17/N18 to the ESD I/O pads, and native run 383 routes both CC resistors. Pipeline trials 380/381 fail final package refinement; their failure is retained. The lane bootstrap remains subject to independent checks. Manual routes join the receptacle's duplicate data pins, the physical ESD flow-through pads, local VBUS/100nF bypass and four ground returns. The CC2 bend moves below the VBUS via sites, and the D− tuning loop gains 0.0635mm for margin below the source's 0.127mm skew limit. Shared power vias are reused through explicit ports; no duplicate drills are emitted. Authoring points are transformed against each component's declared origin/rotation, including the asymmetric receptacle's origin rather than its bounding-box centre.

The fixed checked source is `dist/diagnostics/am3352-usbc-routed-tuned-checked/circuit.json` (SHA256 `5165f2f536469f7b80dee4a4fc507be05958d906932cbf1f20c673a345102cb3`), with 212 components, 912 SMT pads, 104 trace pieces and 105 through-vias. It retains all 81 previous trace pieces and 93 previous physical vias. KiCad independently verifies all ten physical data pads, both CC connections, local VBUS/ESD bypass, and ten USB ground returns to the filled inner1 plane. Both socket orientations have 0.0635mm planar skew; their via counts are respectively 0/0 and 2/2. Planar lengths do not qualify controlled impedance, return paths or actual propagation delay. The PMIC input feed and CPU VBUS-sense copper explicitly remain unconnected. No charging/provisioning or Linux boot qualification is claimed.

All-layer Gerber shorts and native physical DRC violations are zero. Exact local serialization preserves all 289 footprints and 2245 physical records. The report retains 418 presentation warnings, 499 reported unconnected items and the listed ignored checks. All eleven DDR channels, 18 RAM supply balls, 21 RAM ground balls, 28 bypass terminals and the three-segment inner2 bridge still connect. Whole-byte skew still fails; 38 DDR channels remain open in this candidate. This source is separate from the default 23-channel/RAM0 source. Integrating USB with that checked source is required before combining their scope. Evidence is `checks/integrated/am3352-usbc-routed-check-summary.json`; run `npm run check:usbc-routed-evidence`. Fabrication export remains blocked and the original G350 PCB measurements remain required. No remote push or order was made.

Registry verification found a new capacity-autorouter 0.0.956 patch while tscircuit 0.0.2742 and tsci 0.1.2237 remained latest. Both lockfiles were updated. Typechecking passes; fresh native USB runs 384/385 reproduce the exact inputs and outputs of 382/383. The npm lockfile requires `--legacy-peer-deps` for the existing upstream CLI/Circuit JSON peer mismatch; the working runtime uses Bun. Source and board snapshots were preserved through this update. See `checks/integrated/am3352-usbc-toolchain-verification.json`.

The working default now combines the checked RAM0 23-channel DDR replay with the shared USB-C copper in `experiments/am3352-ddr-usbc-replay.circuit.tsx`. The board has 212 components, 912 pads, 125 trace pieces and 129 full-depth vias on four layers. Native `SOLVERS.BusLanesPipelineSolver` supplies the CPU VBUS-sense, charging feed, divider input, filter, clamp and PMIC bypass phases in addition to the earlier data-pair/CC bootstrap. A manual QFN escape and three local ground returns supplement the solver. Existing same-net fixed-copper owner aliases are normalized in routing inputs without changing geometry or other nets; every successful phase records its original source/input/output hashes, and the combined verifier checks those aliases and the saved routes.

Fresh KiCad connectivity verifies all 38 USB numeric pad assignments and 40 pad/ground checks, including both cable orientations, socket-to-PMIC feed/bypass and CPU VBUS filter/clamp. All 23 DDR channels, 18 RAM supply balls, 21 RAM grounds and 28 RAM bypass terminals remain connected. Both bytes retain their 0.635 mm planar limits, both strobes retain their 0.127 mm limits, and each USB orientation has 0.0635 mm planar skew. Physical DRC and all-layer shorts are zero. Exact serialization preserves 293 footprints and all 13619 physical records; 418 presentation warnings and 499 reported host unconnected items remain. Evidence: `checks/integrated/am3352-ddr-usbc-control-check-summary.json`; run `npm run check:ddr-usbc-evidence`.

The new default supersedes the separate eleven-channel USB candidate; their counts are not added. It still has 26 DDR command/clock signals open and incomplete host power, clock, storage and handheld routing. Current policy, protection over temperature/transients, controlled impedance and full propagation-delay timing remain unqualified. Linux boot/provisioning is untested. The current 100 × 124 mm routing fixture does not fit the original G350 shell; its internal outline, mounts, button/port positions and clearances remain required. Fabrication export stays blocked. Work remains local.

The subsequent RAM0 clock-access trial opens both DQS1 signals while preserving all other DDR/USB copper. Native `bus_lanes` attempt 412 routes CK/CKn with four actual CPU/RAM dogbones and 0.076616 mm planar skew against 0.127 mm. Independent checks verify its 23 channels, USB data/control/ground and all RAM references, with zero shorts or physical DRC violations. Its count includes the clock pair and excludes the two strobes; it is separate from the default. Evidence: `checks/integrated/am3352-ddr-usbc-native-clock-check-summary.json`; verifier: `npm run check:ddr-clock-evidence`.
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
