Abse2001/g350-linux-handheld/docs/RK3566_HOST_RECORD.md

# Historical RK3566 investigation — superseded by AM3352

# Integrated Linux host requirement — 2026-10-02

The handheld must contain the Linux computer directly on its main PCB. The existing Revision B source and Gerbers use an external Raspberry Pi Zero 2 W through J_PI and a data pigtail; they do not meet this requirement. Their successful fabrication checks are not evidence that an integrated host has been designed or checked.
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
