Abse2001/g350-linux-handheld/checks/integrated/g350-byte0-complete-bus/g350-byte0-bottom.png

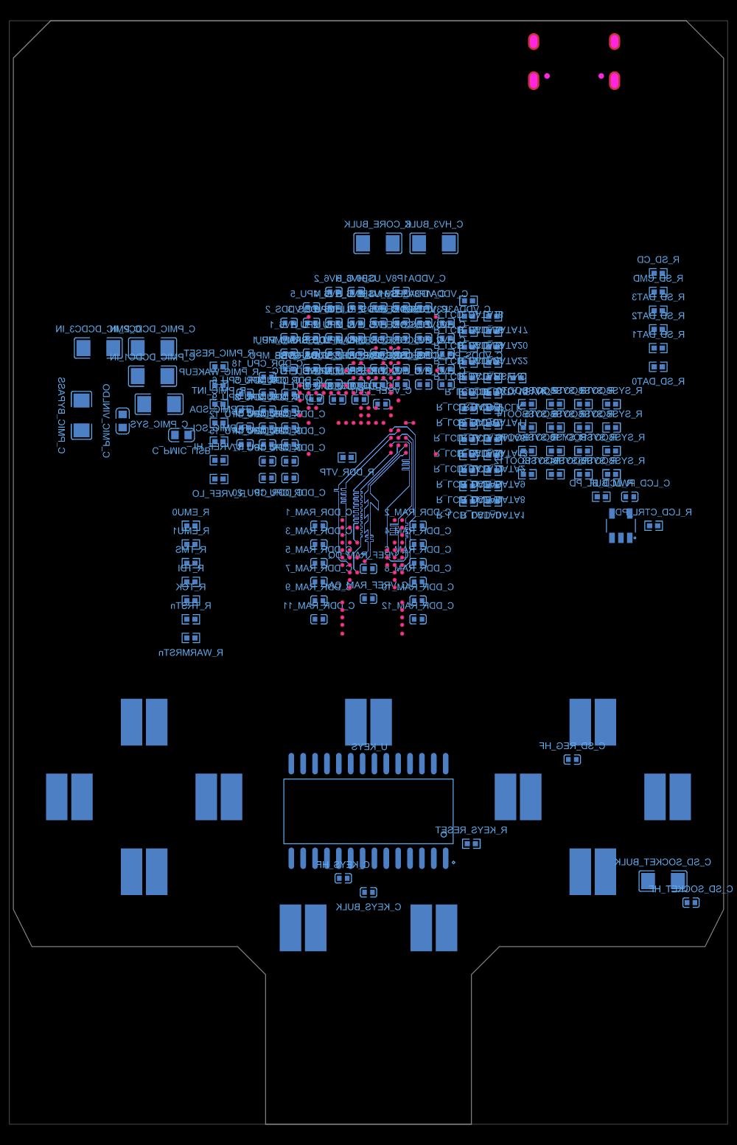
checks/integrated/g350-byte0-complete-bus/g350-byte0-bottom.png
