Abse2001/g350-linux-handheld/checks/layout/critical-variant/g350-critical-placement-top.png

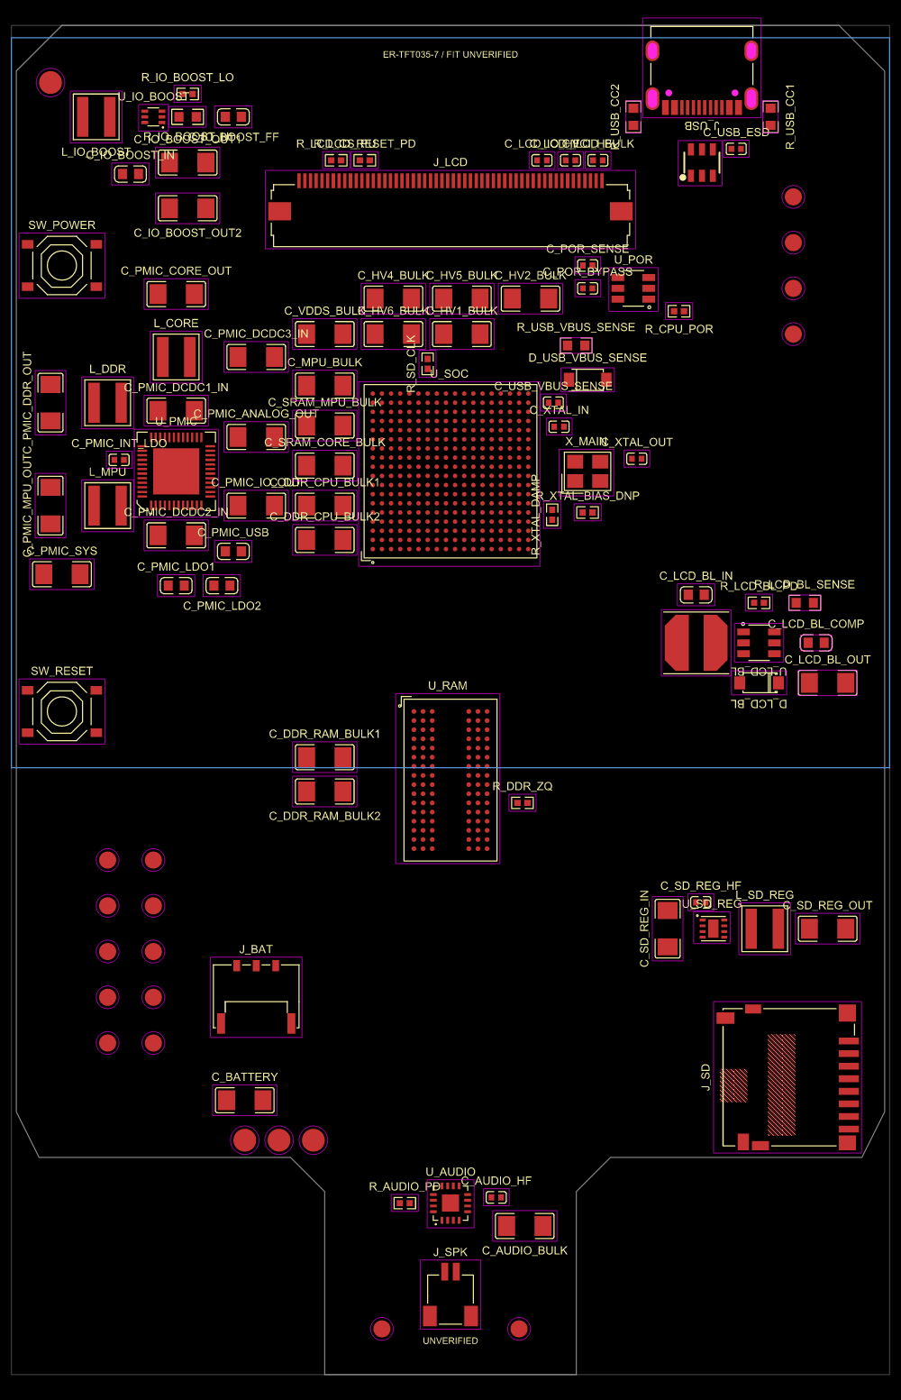
checks/layout/critical-variant/g350-critical-placement-top.png
