Abse2001/g350-linux-handheld/checks/layout/ddr-corridor-variant/g350-ddr-corridor-bottom.png

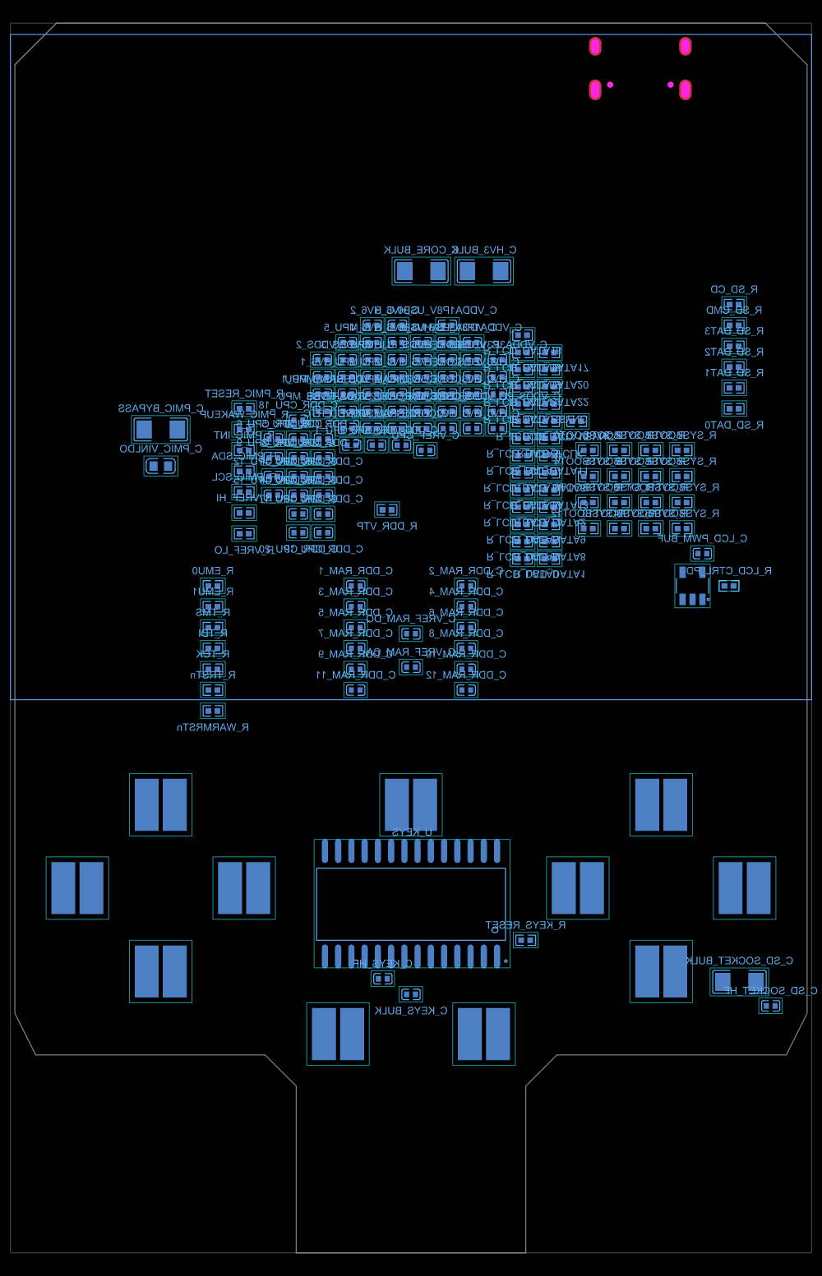
checks/layout/ddr-corridor-variant/g350-ddr-corridor-bottom.png
