Abse2001/g350-linux-handheld/checks/layout/display-variant/g350-display-placement-bottom.png

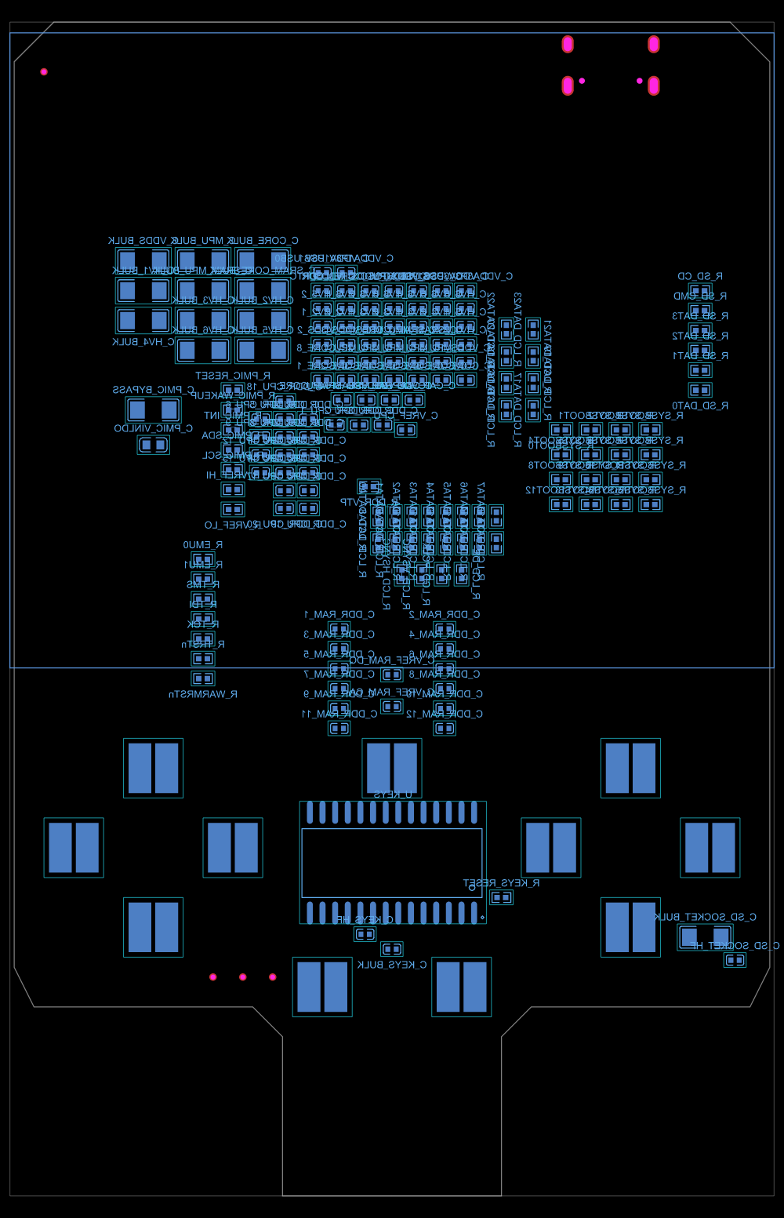
checks/layout/display-variant/g350-display-placement-bottom.png
