Abse2001/g350-linux-handheld/checks/layout/display-variant/g350-display-placement-top.png

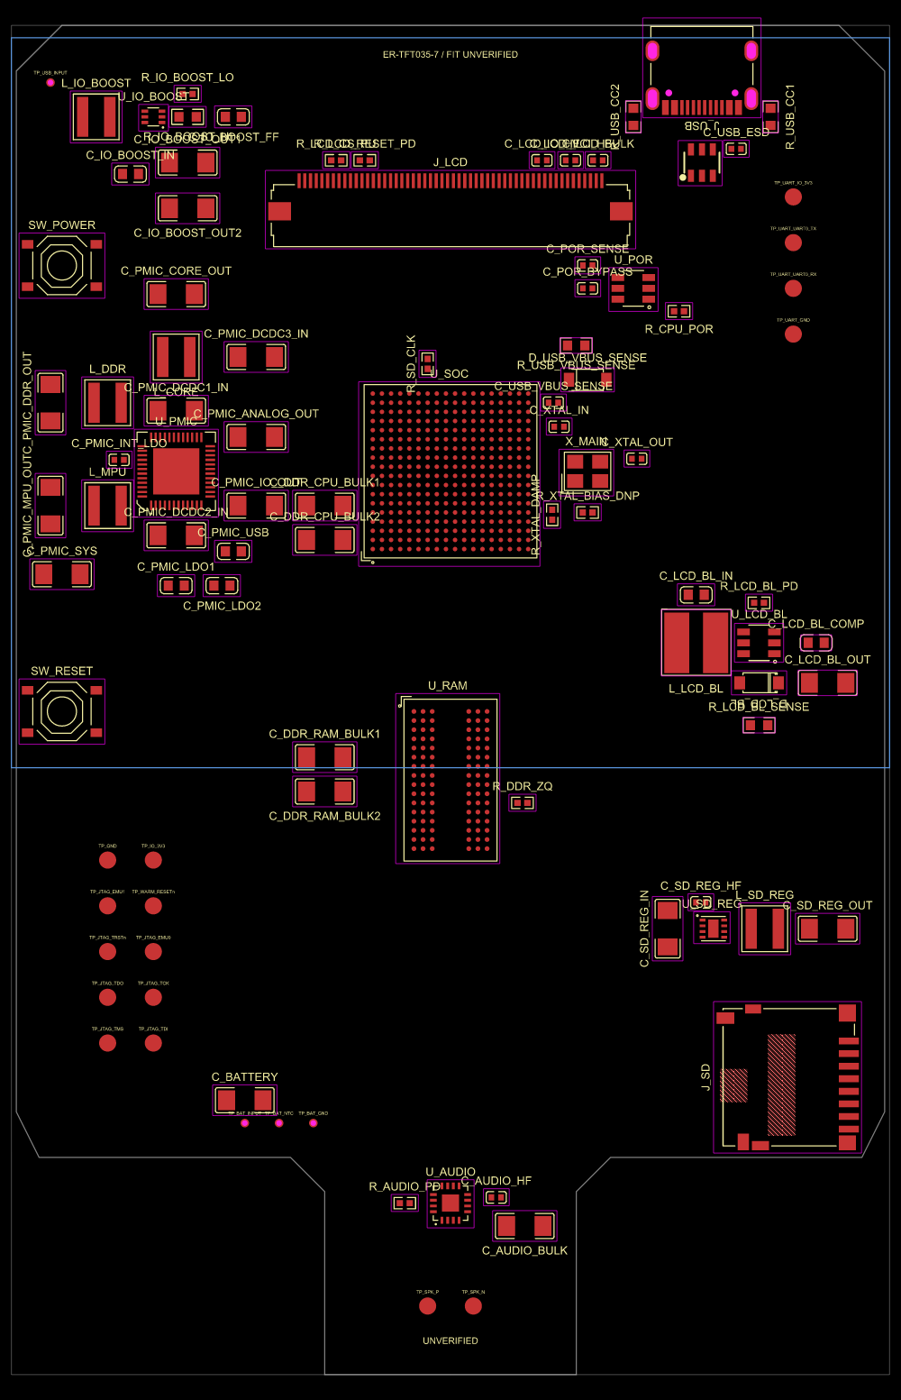
checks/layout/display-variant/g350-display-placement-top.png
