Abse2001/g350-linux-handheld/checks/layout/g350-placement-top.png

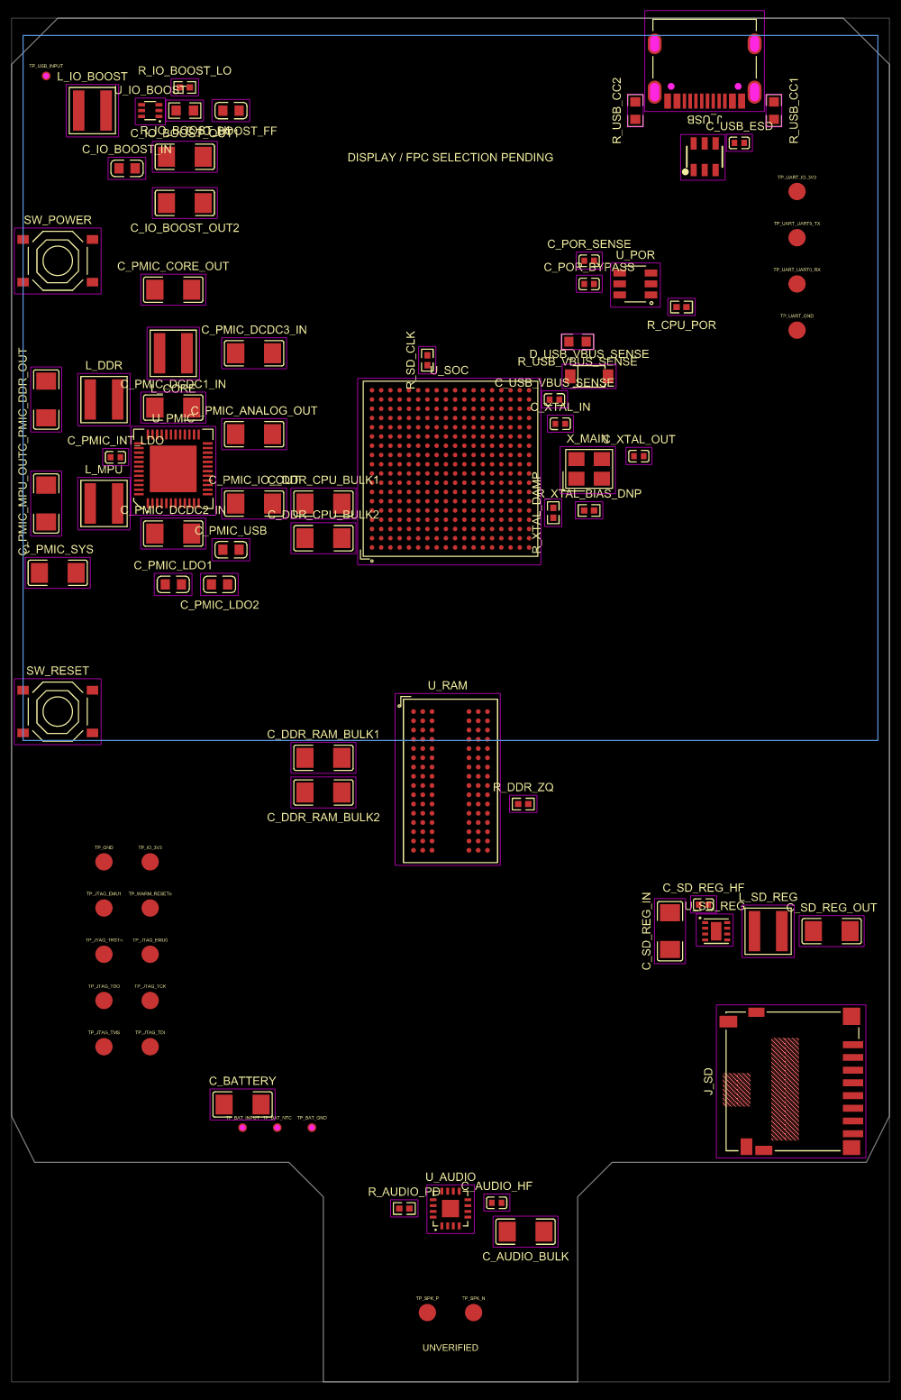
checks/layout/g350-placement-top.png
