Abse2001/g350-linux-handheld/checks/layout/pmic-placement-variant/g350-pmic-placement-top.png

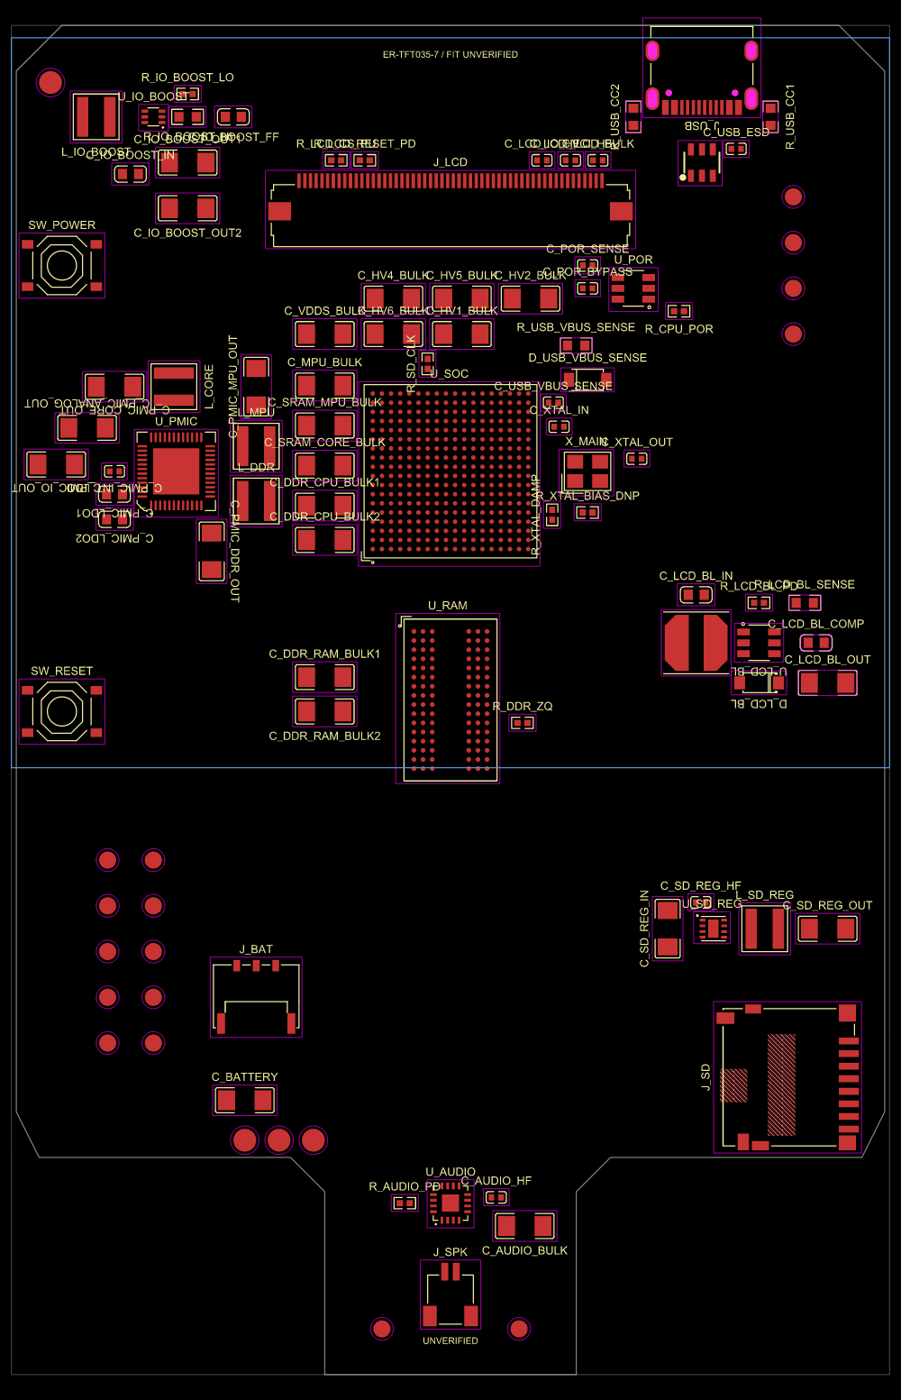
checks/layout/pmic-placement-variant/g350-pmic-placement-top.png
