Abse2001/g350-linux-handheld/cloud/screenshots/g350-cloud-published.jpg

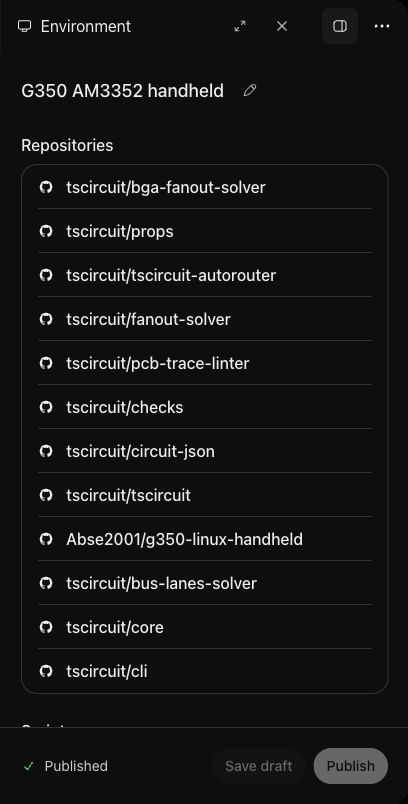
cloud/screenshots/g350-cloud-published.jpg
