Abse2001/g350-linux-handheld/images/am3352-command-first-native-byte-bottom.png

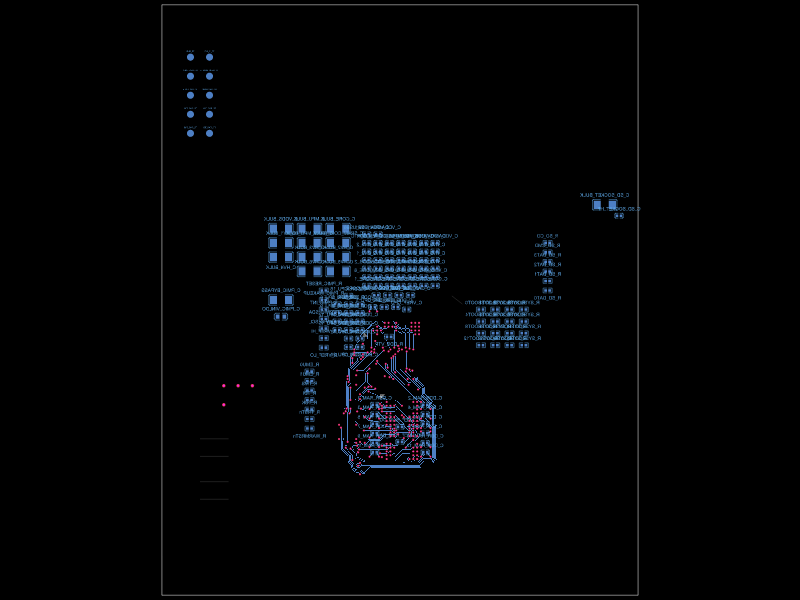
images/am3352-command-first-native-byte-bottom.png
