Abse2001/g350-linux-handheld/images/am3352-ddr-usbc-a3-bootstrap-bottom.png

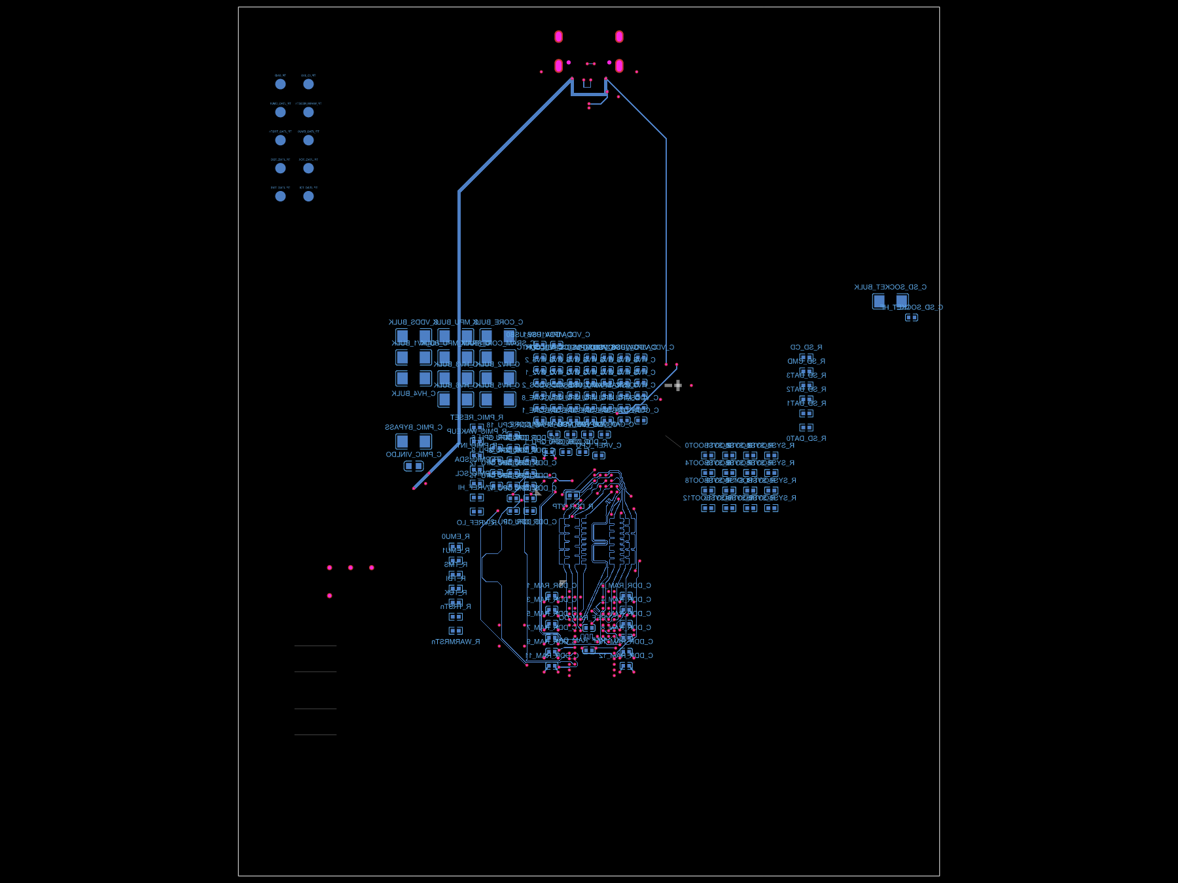
images/am3352-ddr-usbc-a3-bootstrap-bottom.png
