Abse2001/g350-linux-handheld/images/am3352-ddr-usbc-casn-d3-coupled-bottom.png

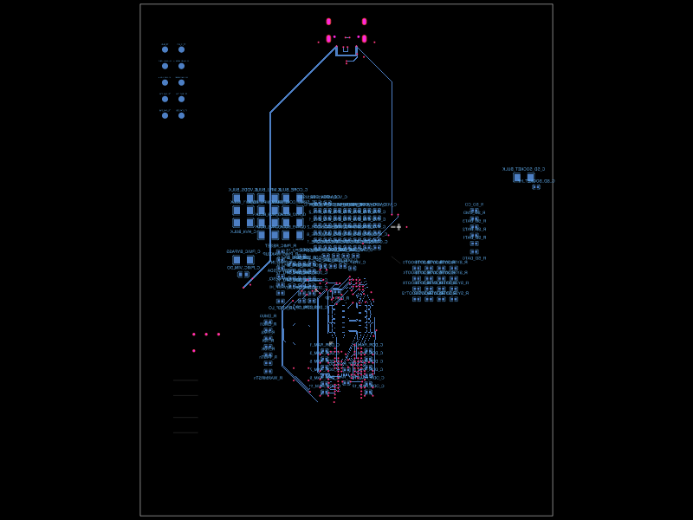
images/am3352-ddr-usbc-casn-d3-coupled-bottom.png
