Abse2001/g350-linux-handheld/images/am3352-four-layer-byte0-native-diagnostic.png

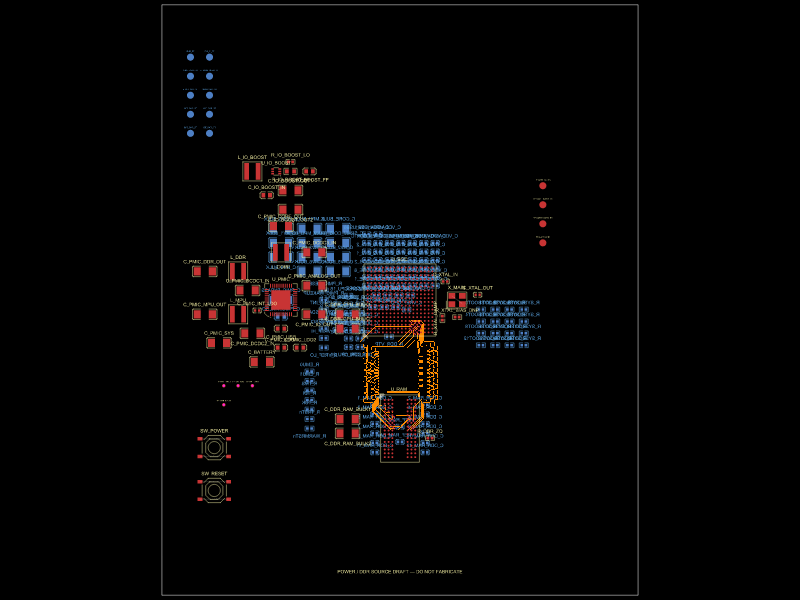
images/am3352-four-layer-byte0-native-diagnostic.png
