Abse2001/g350-linux-handheld/images/am3352-four-layer-reference-source.png

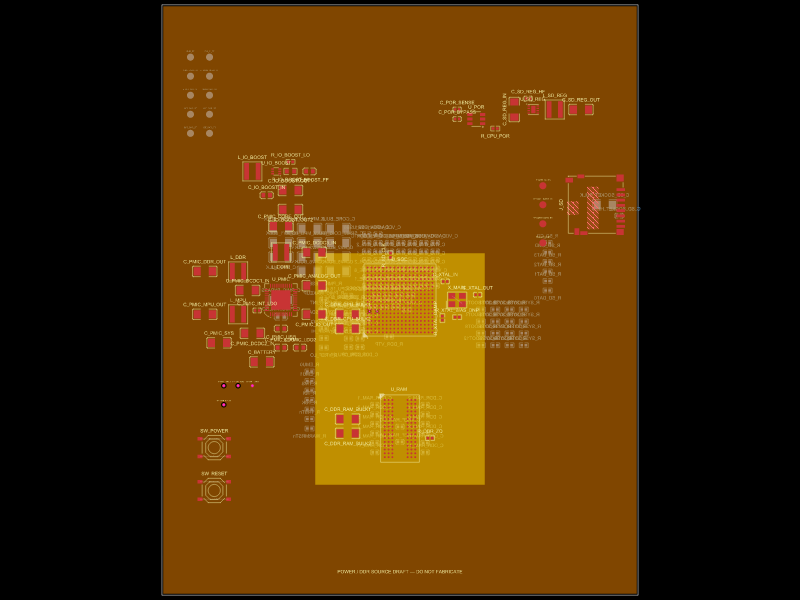
images/am3352-four-layer-reference-source.png
