Abse2001/g350-linux-handheld/images/am3352-memory-11.png

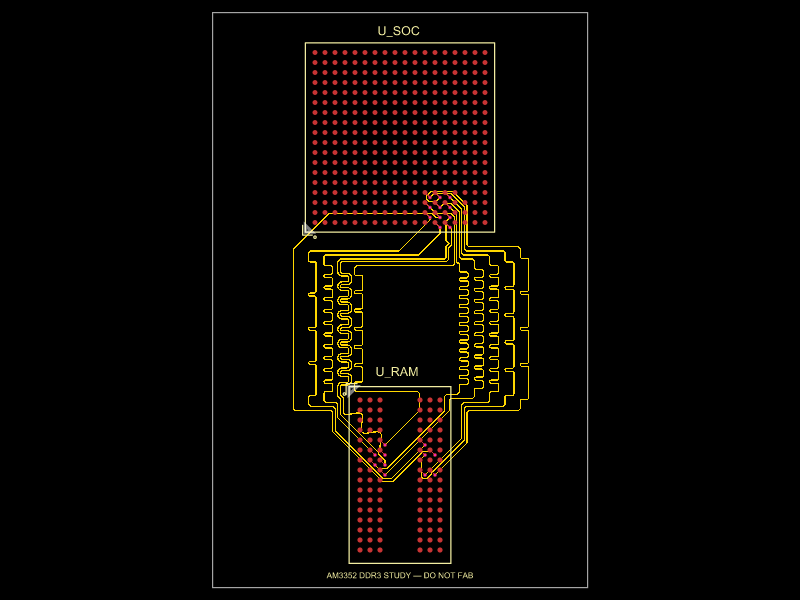
images/am3352-memory-11.png
