Abse2001/g350-linux-handheld/images/am3352-ram-bottom-flexible-fanout-747-replay-top.png

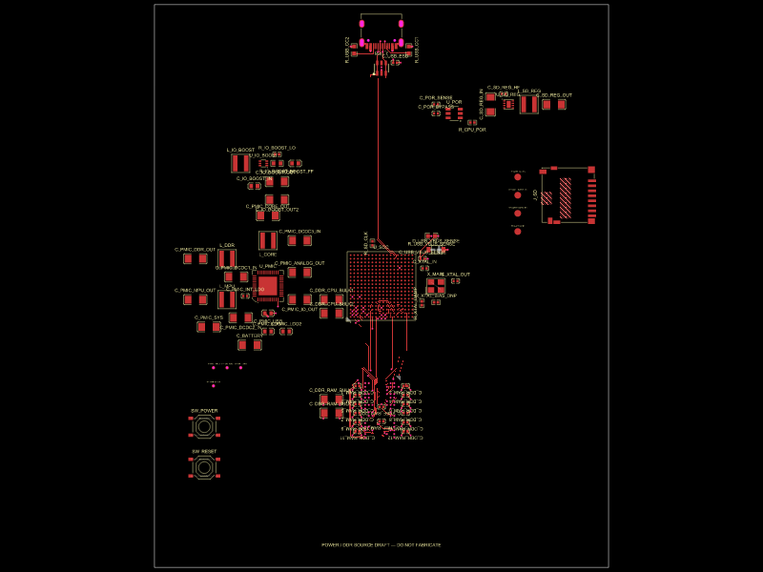
images/am3352-ram-bottom-flexible-fanout-747-replay-top.png
