Abse2001/g350-linux-handheld/images/am3352-ram-rotated-180-byte0-fixed-reused-reservations-top.png

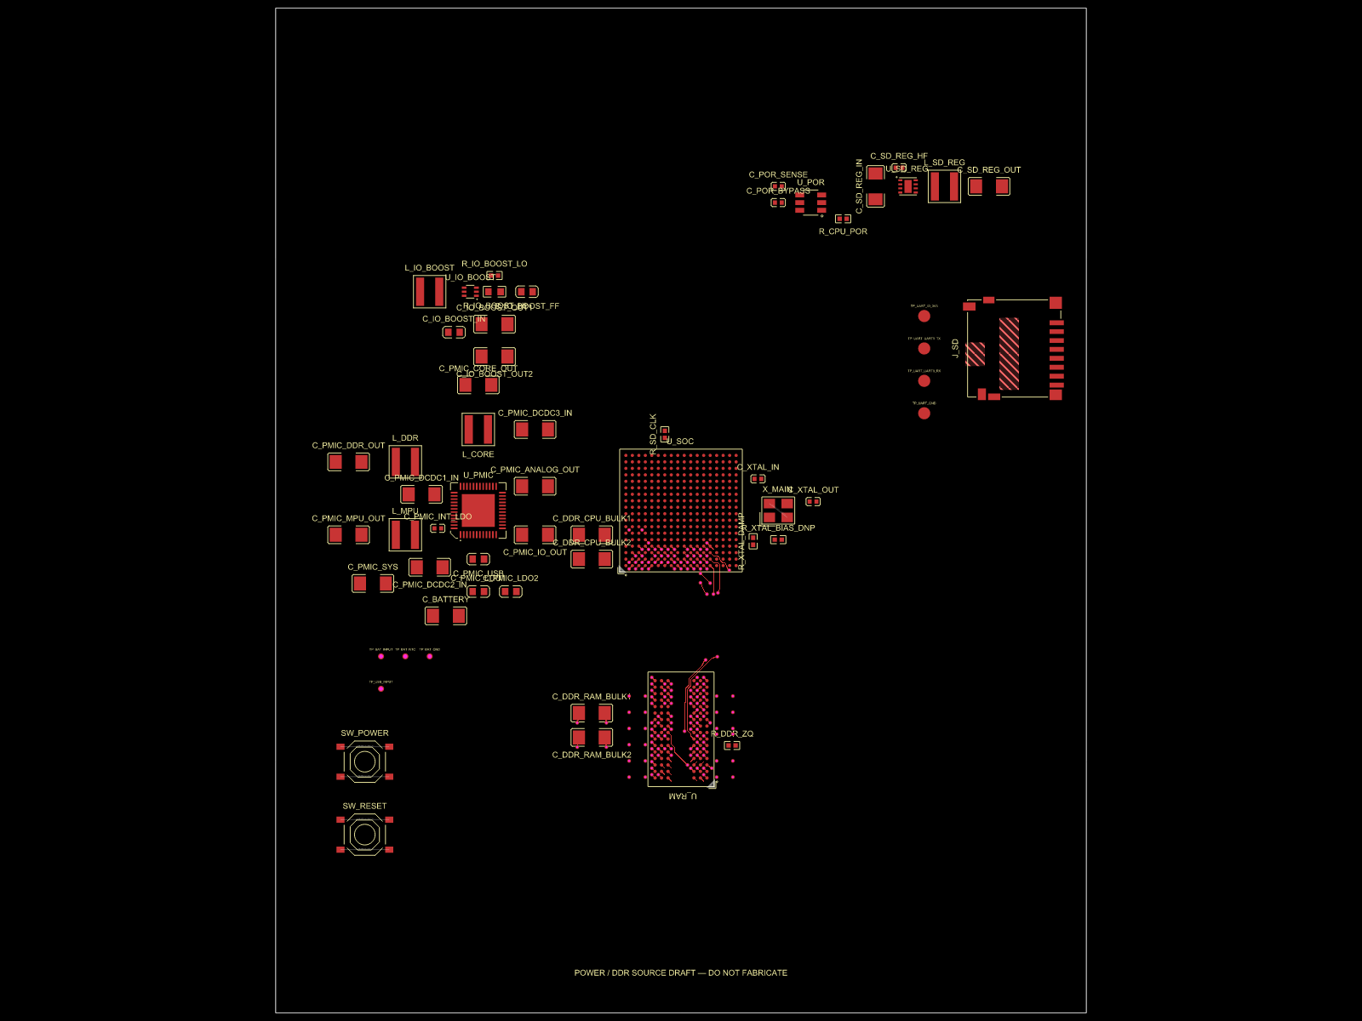
images/am3352-ram-rotated-180-byte0-fixed-reused-reservations-top.png
