Abse2001/g350-linux-handheld/images/am3352-ram-rotated-180-byte-swapped-byte0-pair-bottom-detail.png

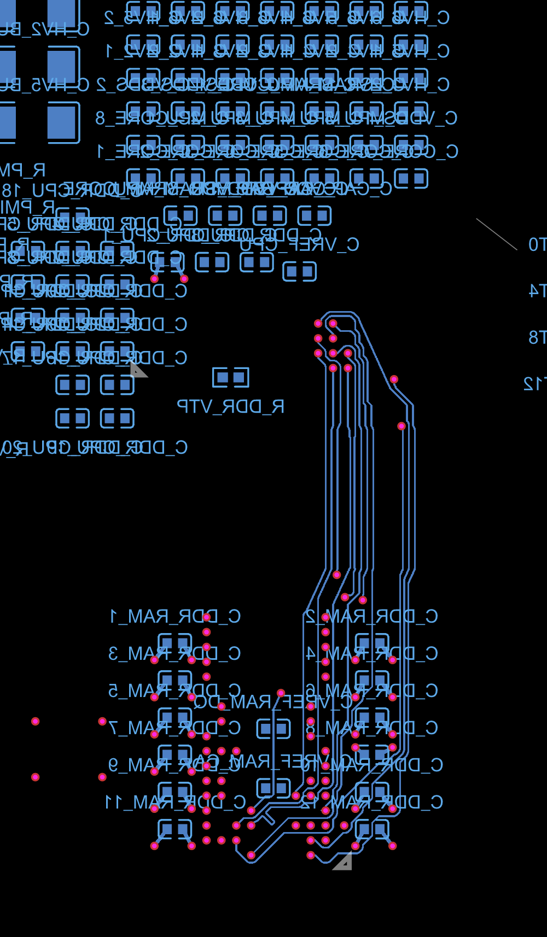
images/am3352-ram-rotated-180-byte-swapped-byte0-pair-bottom-detail.png
