Abse2001/g350-linux-handheld/images/am3352-usbc-routed-detail.png

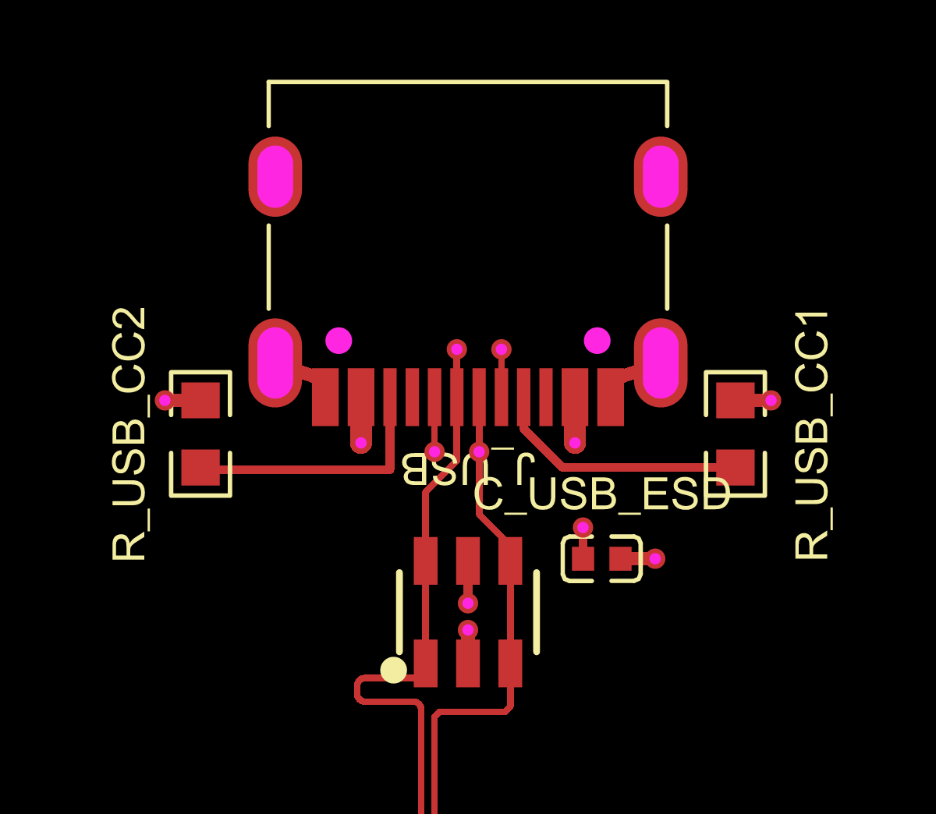
images/am3352-usbc-routed-detail.png
