Abse2001/g350-linux-handheld/images/pcb-rev-b.png

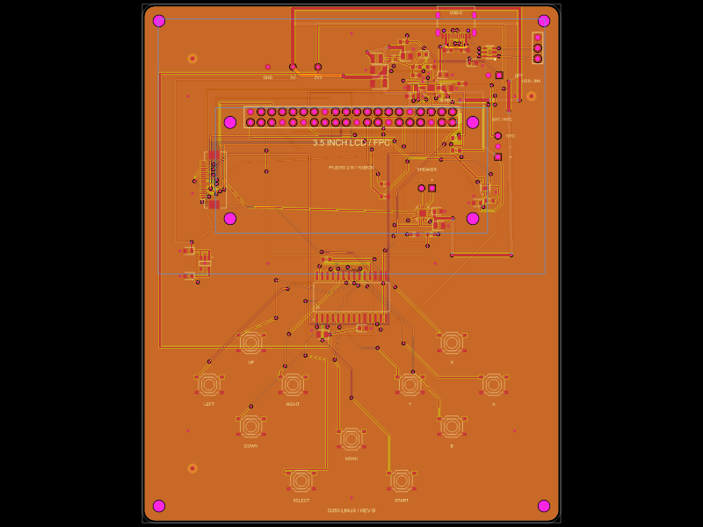
images/pcb-rev-b.png
