Abse2001/g350-linux-handheld/images/rk3566-memory-hdi-36.png

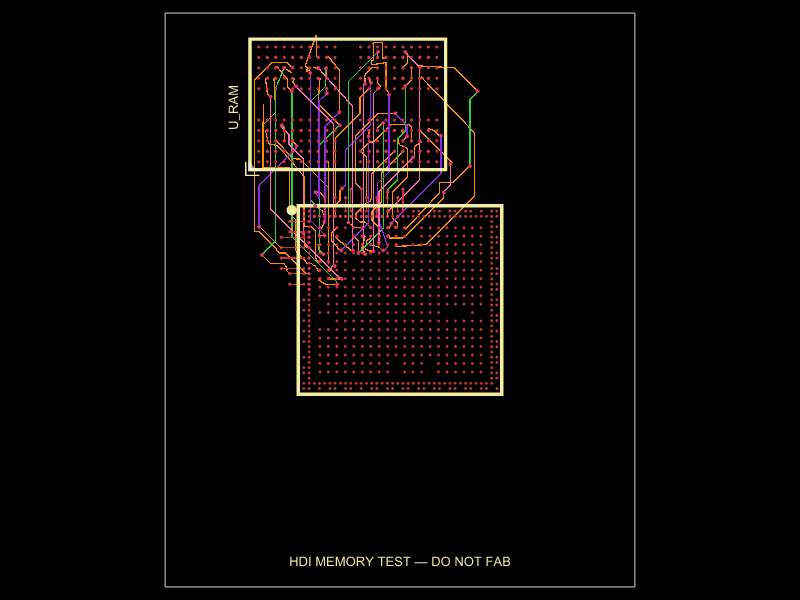
images/rk3566-memory-hdi-36.png
