Abse2001/g350-linux-handheld/mechanical/g350-fit-template-preview.png

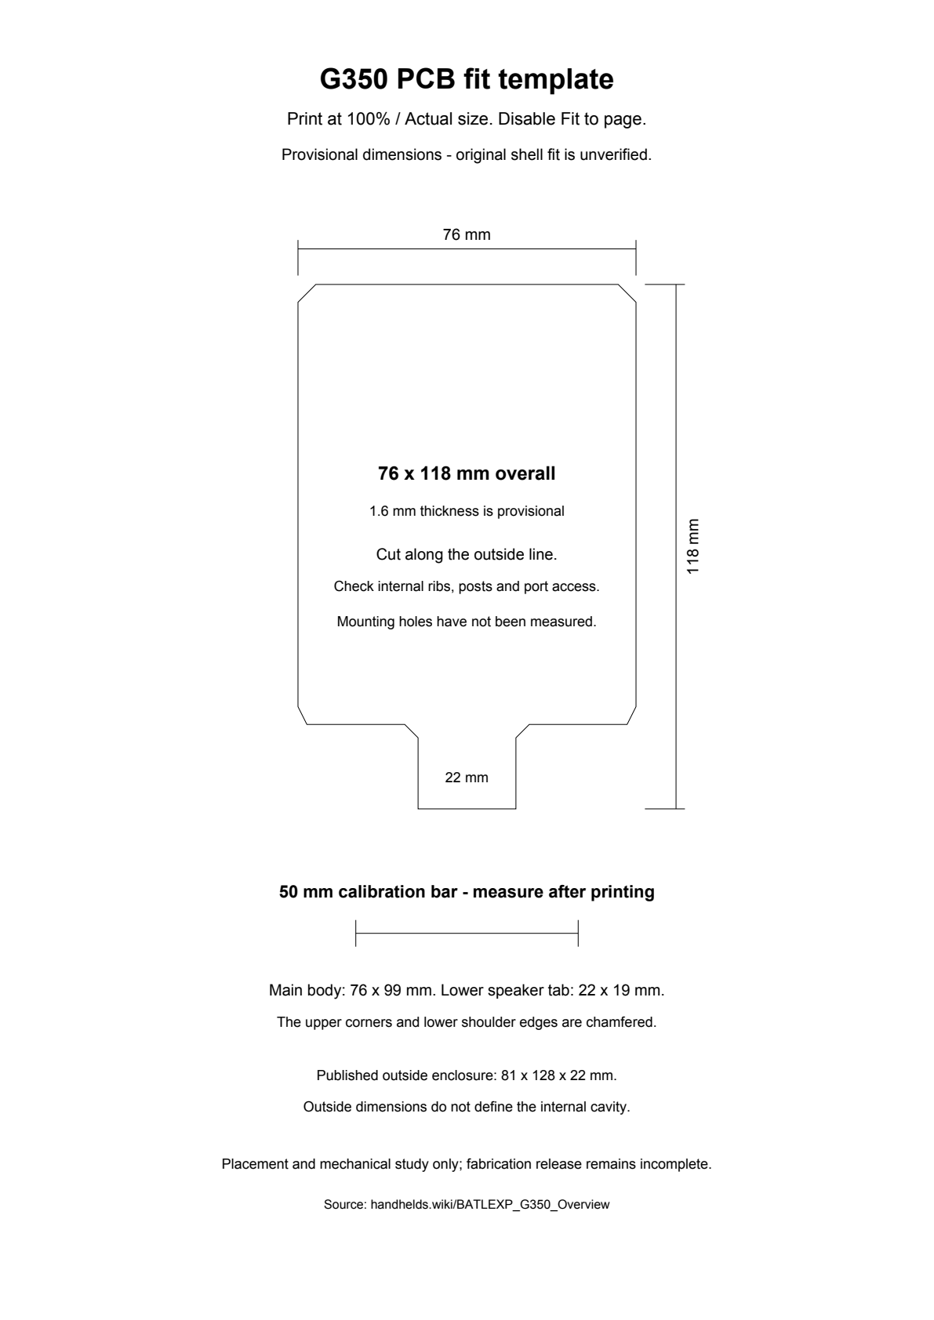
mechanical/g350-fit-template-preview.png
