Abse2001/g350-linux-handheld/mechanical/g350-provisional-outline.png

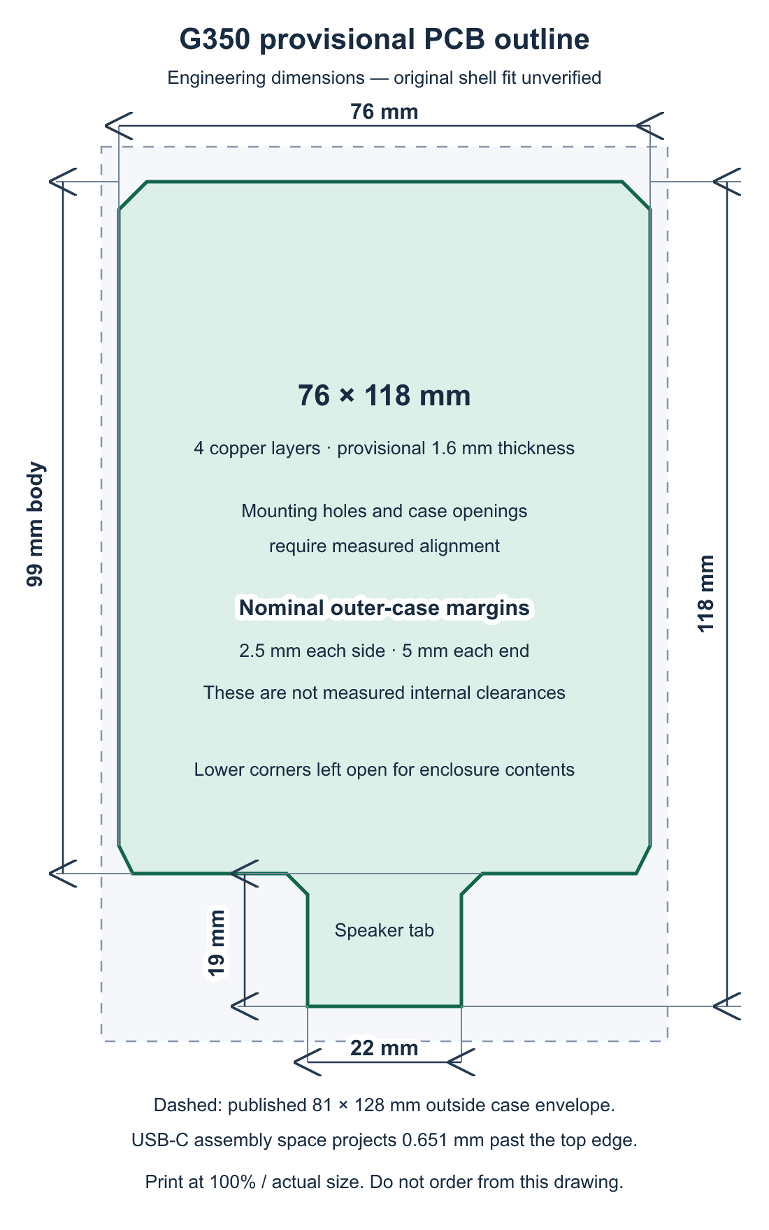
mechanical/g350-provisional-outline.png
