Abse2001/g350-linux-handheld/images/am3352-guided-byte0-48-bottom.png

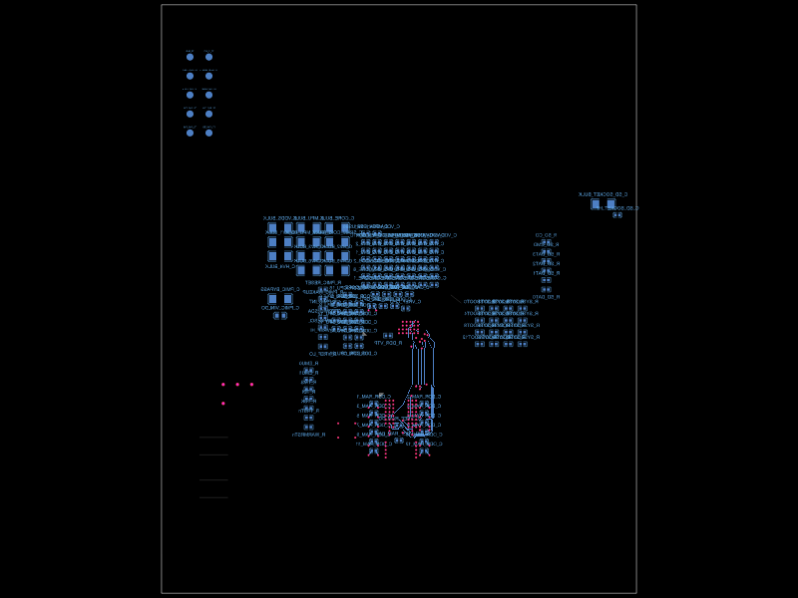
images/am3352-guided-byte0-48-bottom.png
