Abse2001/g350-linux-handheld/checks/integrated/g350-dqs0-repaired/g350-dqs0-bottom.png

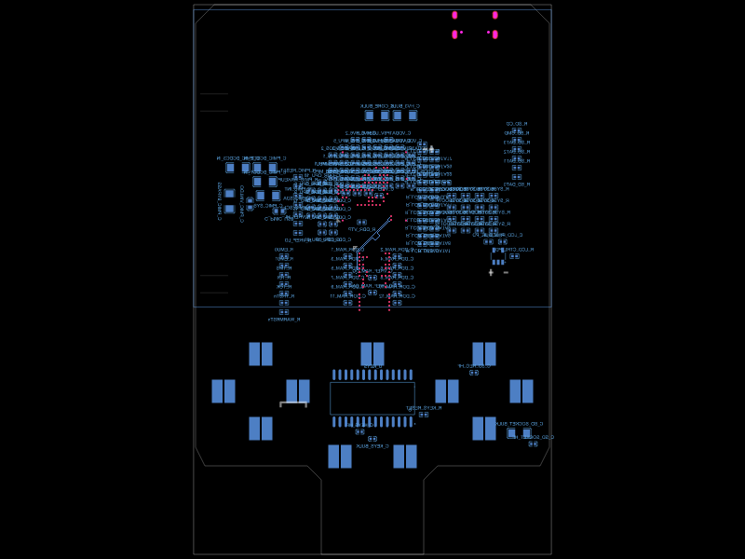
checks/integrated/g350-dqs0-repaired/g350-dqs0-bottom.png
